dave18/EBAZ4205-Daughter-Board/Test_Code/EBAZ4205_Test5.cache/ip/2019.1.3/844bc8edf4976deb/System_processing_system7_0_0_sim_netlist.v

// Copyright 1986-2019 Xilinx, Inc. All Rights Reserved.
// --------------------------------------------------------------------------------
// Tool Version: Vivado v.2019.1.3 (win64) Build 2644227 Wed Sep  4 09:45:24 MDT 2019
// Date        : Sat Jan 30 14:02:05 2021
// Host        : DESKTOP-VR9QE9J running 64-bit major release  (build 9200)
// Command     : write_verilog -force -mode funcsim -rename_top decalper_eb_ot_sdeen_pot_pi_dehcac_xnilix -prefix
//               decalper_eb_ot_sdeen_pot_pi_dehcac_xnilix_ System_processing_system7_0_0_sim_netlist.v
// Design      : System_processing_system7_0_0
// Purpose     : This verilog netlist is a functional simulation representation of the design and should not be modified
//               or synthesized. This netlist cannot be used for SDF annotated simulation.
// Device      : xc7z010clg400-1
// --------------------------------------------------------------------------------
`timescale 1 ps / 1 ps

(* CHECK_LICENSE_TYPE = "System_processing_system7_0_0,processing_system7_v5_5_processing_system7,{}" *) (* DowngradeIPIdentifiedWarnings = "yes" *) (* X_CORE_INFO = "processing_system7_v5_5_processing_system7,Vivado 2019.1.3" *) 
(* NotValidForBitStream *)
module decalper_eb_ot_sdeen_pot_pi_dehcac_xnilix
   (FCLK_CLK0,
    FCLK_RESET0_N,
    MIO,
    DDR_CAS_n,
    DDR_CKE,
    DDR_Clk_n,
    DDR_Clk,
    DDR_CS_n,
    DDR_DRSTB,
    DDR_ODT,
    DDR_RAS_n,
    DDR_WEB,
    DDR_BankAddr,
    DDR_Addr,
    DDR_VRN,
    DDR_VRP,
    DDR_DM,
    DDR_DQ,
    DDR_DQS_n,
    DDR_DQS,
    PS_SRSTB,
    PS_CLK,
    PS_PORB);
  (* X_INTERFACE_INFO = "xilinx.com:signal:clock:1.0 FCLK_CLK0 CLK" *) (* X_INTERFACE_PARAMETER = "XIL_INTERFACENAME FCLK_CLK0, FREQ_HZ 50000000, PHASE 0.000, CLK_DOMAIN System_processing_system7_0_0_FCLK_CLK0, INSERT_VIP 0" *) output FCLK_CLK0;
  (* X_INTERFACE_INFO = "xilinx.com:signal:reset:1.0 FCLK_RESET0_N RST" *) (* X_INTERFACE_PARAMETER = "XIL_INTERFACENAME FCLK_RESET0_N, POLARITY ACTIVE_LOW, INSERT_VIP 0" *) output FCLK_RESET0_N;
  (* X_INTERFACE_INFO = "xilinx.com:display_processing_system7:fixedio:1.0 FIXED_IO MIO" *) inout [53:0]MIO;
  (* X_INTERFACE_INFO = "xilinx.com:interface:ddrx:1.0 DDR CAS_N" *) inout DDR_CAS_n;
  (* X_INTERFACE_INFO = "xilinx.com:interface:ddrx:1.0 DDR CKE" *) inout DDR_CKE;
  (* X_INTERFACE_INFO = "xilinx.com:interface:ddrx:1.0 DDR CK_N" *) inout DDR_Clk_n;
  (* X_INTERFACE_INFO = "xilinx.com:interface:ddrx:1.0 DDR CK_P" *) inout DDR_Clk;
  (* X_INTERFACE_INFO = "xilinx.com:interface:ddrx:1.0 DDR CS_N" *) inout DDR_CS_n;
  (* X_INTERFACE_INFO = "xilinx.com:interface:ddrx:1.0 DDR RESET_N" *) inout DDR_DRSTB;
  (* X_INTERFACE_INFO = "xilinx.com:interface:ddrx:1.0 DDR ODT" *) inout DDR_ODT;
  (* X_INTERFACE_INFO = "xilinx.com:interface:ddrx:1.0 DDR RAS_N" *) inout DDR_RAS_n;
  (* X_INTERFACE_INFO = "xilinx.com:interface:ddrx:1.0 DDR WE_N" *) inout DDR_WEB;
  (* X_INTERFACE_INFO = "xilinx.com:interface:ddrx:1.0 DDR BA" *) inout [2:0]DDR_BankAddr;
  (* X_INTERFACE_INFO = "xilinx.com:interface:ddrx:1.0 DDR ADDR" *) inout [14:0]DDR_Addr;
  (* X_INTERFACE_INFO = "xilinx.com:display_processing_system7:fixedio:1.0 FIXED_IO DDR_VRN" *) inout DDR_VRN;
  (* X_INTERFACE_INFO = "xilinx.com:display_processing_system7:fixedio:1.0 FIXED_IO DDR_VRP" *) inout DDR_VRP;
  (* X_INTERFACE_INFO = "xilinx.com:interface:ddrx:1.0 DDR DM" *) inout [3:0]DDR_DM;
  (* X_INTERFACE_INFO = "xilinx.com:interface:ddrx:1.0 DDR DQ" *) inout [31:0]DDR_DQ;
  (* X_INTERFACE_INFO = "xilinx.com:interface:ddrx:1.0 DDR DQS_N" *) inout [3:0]DDR_DQS_n;
  (* X_INTERFACE_INFO = "xilinx.com:interface:ddrx:1.0 DDR DQS_P" *) (* X_INTERFACE_PARAMETER = "XIL_INTERFACENAME DDR, CAN_DEBUG false, TIMEPERIOD_PS 1250, MEMORY_TYPE COMPONENTS, DATA_WIDTH 8, CS_ENABLED true, DATA_MASK_ENABLED true, SLOT Single, MEM_ADDR_MAP ROW_COLUMN_BANK, BURST_LENGTH 8, AXI_ARBITRATION_SCHEME TDM, CAS_LATENCY 11, CAS_WRITE_LATENCY 11" *) inout [3:0]DDR_DQS;
  (* X_INTERFACE_INFO = "xilinx.com:display_processing_system7:fixedio:1.0 FIXED_IO PS_SRSTB" *) inout PS_SRSTB;
  (* X_INTERFACE_INFO = "xilinx.com:display_processing_system7:fixedio:1.0 FIXED_IO PS_CLK" *) inout PS_CLK;
  (* X_INTERFACE_INFO = "xilinx.com:display_processing_system7:fixedio:1.0 FIXED_IO PS_PORB" *) (* X_INTERFACE_PARAMETER = "XIL_INTERFACENAME FIXED_IO, CAN_DEBUG false" *) inout PS_PORB;

  wire [14:0]DDR_Addr;
  wire [2:0]DDR_BankAddr;
  wire DDR_CAS_n;
  wire DDR_CKE;
  wire DDR_CS_n;
  wire DDR_Clk;
  wire DDR_Clk_n;
  wire [3:0]DDR_DM;
  wire [31:0]DDR_DQ;
  wire [3:0]DDR_DQS;
  wire [3:0]DDR_DQS_n;
  wire DDR_DRSTB;
  wire DDR_ODT;
  wire DDR_RAS_n;
  wire DDR_VRN;
  wire DDR_VRP;
  wire DDR_WEB;
  wire FCLK_CLK0;
  wire FCLK_RESET0_N;
  wire [53:0]MIO;
  wire PS_CLK;
  wire PS_PORB;
  wire PS_SRSTB;
  wire NLW_inst_CAN0_PHY_TX_UNCONNECTED;
  wire NLW_inst_CAN1_PHY_TX_UNCONNECTED;
  wire NLW_inst_DMA0_DAVALID_UNCONNECTED;
  wire NLW_inst_DMA0_DRREADY_UNCONNECTED;
  wire NLW_inst_DMA0_RSTN_UNCONNECTED;
  wire NLW_inst_DMA1_DAVALID_UNCONNECTED;
  wire NLW_inst_DMA1_DRREADY_UNCONNECTED;
  wire NLW_inst_DMA1_RSTN_UNCONNECTED;
  wire NLW_inst_DMA2_DAVALID_UNCONNECTED;
  wire NLW_inst_DMA2_DRREADY_UNCONNECTED;
  wire NLW_inst_DMA2_RSTN_UNCONNECTED;
  wire NLW_inst_DMA3_DAVALID_UNCONNECTED;
  wire NLW_inst_DMA3_DRREADY_UNCONNECTED;
  wire NLW_inst_DMA3_RSTN_UNCONNECTED;
  wire NLW_inst_ENET0_GMII_TX_EN_UNCONNECTED;
  wire NLW_inst_ENET0_GMII_TX_ER_UNCONNECTED;
  wire NLW_inst_ENET0_MDIO_MDC_UNCONNECTED;
  wire NLW_inst_ENET0_MDIO_O_UNCONNECTED;
  wire NLW_inst_ENET0_MDIO_T_UNCONNECTED;
  wire NLW_inst_ENET0_PTP_DELAY_REQ_RX_UNCONNECTED;
  wire NLW_inst_ENET0_PTP_DELAY_REQ_TX_UNCONNECTED;
  wire NLW_inst_ENET0_PTP_PDELAY_REQ_RX_UNCONNECTED;
  wire NLW_inst_ENET0_PTP_PDELAY_REQ_TX_UNCONNECTED;
  wire NLW_inst_ENET0_PTP_PDELAY_RESP_RX_UNCONNECTED;
  wire NLW_inst_ENET0_PTP_PDELAY_RESP_TX_UNCONNECTED;
  wire NLW_inst_ENET0_PTP_SYNC_FRAME_RX_UNCONNECTED;
  wire NLW_inst_ENET0_PTP_SYNC_FRAME_TX_UNCONNECTED;
  wire NLW_inst_ENET0_SOF_RX_UNCONNECTED;
  wire NLW_inst_ENET0_SOF_TX_UNCONNECTED;
  wire NLW_inst_ENET1_GMII_TX_EN_UNCONNECTED;
  wire NLW_inst_ENET1_GMII_TX_ER_UNCONNECTED;
  wire NLW_inst_ENET1_MDIO_MDC_UNCONNECTED;
  wire NLW_inst_ENET1_MDIO_O_UNCONNECTED;
  wire NLW_inst_ENET1_MDIO_T_UNCONNECTED;
  wire NLW_inst_ENET1_PTP_DELAY_REQ_RX_UNCONNECTED;
  wire NLW_inst_ENET1_PTP_DELAY_REQ_TX_UNCONNECTED;
  wire NLW_inst_ENET1_PTP_PDELAY_REQ_RX_UNCONNECTED;
  wire NLW_inst_ENET1_PTP_PDELAY_REQ_TX_UNCONNECTED;
  wire NLW_inst_ENET1_PTP_PDELAY_RESP_RX_UNCONNECTED;
  wire NLW_inst_ENET1_PTP_PDELAY_RESP_TX_UNCONNECTED;
  wire NLW_inst_ENET1_PTP_SYNC_FRAME_RX_UNCONNECTED;
  wire NLW_inst_ENET1_PTP_SYNC_FRAME_TX_UNCONNECTED;
  wire NLW_inst_ENET1_SOF_RX_UNCONNECTED;
  wire NLW_inst_ENET1_SOF_TX_UNCONNECTED;
  wire NLW_inst_EVENT_EVENTO_UNCONNECTED;
  wire NLW_inst_FCLK_CLK1_UNCONNECTED;
  wire NLW_inst_FCLK_CLK2_UNCONNECTED;
  wire NLW_inst_FCLK_CLK3_UNCONNECTED;
  wire NLW_inst_FCLK_RESET1_N_UNCONNECTED;
  wire NLW_inst_FCLK_RESET2_N_UNCONNECTED;
  wire NLW_inst_FCLK_RESET3_N_UNCONNECTED;
  wire NLW_inst_FTMT_F2P_TRIGACK_0_UNCONNECTED;
  wire NLW_inst_FTMT_F2P_TRIGACK_1_UNCONNECTED;
  wire NLW_inst_FTMT_F2P_TRIGACK_2_UNCONNECTED;
  wire NLW_inst_FTMT_F2P_TRIGACK_3_UNCONNECTED;
  wire NLW_inst_FTMT_P2F_TRIG_0_UNCONNECTED;
  wire NLW_inst_FTMT_P2F_TRIG_1_UNCONNECTED;
  wire NLW_inst_FTMT_P2F_TRIG_2_UNCONNECTED;
  wire NLW_inst_FTMT_P2F_TRIG_3_UNCONNECTED;
  wire NLW_inst_I2C0_SCL_O_UNCONNECTED;
  wire NLW_inst_I2C0_SCL_T_UNCONNECTED;
  wire NLW_inst_I2C0_SDA_O_UNCONNECTED;
  wire NLW_inst_I2C0_SDA_T_UNCONNECTED;
  wire NLW_inst_I2C1_SCL_O_UNCONNECTED;
  wire NLW_inst_I2C1_SCL_T_UNCONNECTED;
  wire NLW_inst_I2C1_SDA_O_UNCONNECTED;
  wire NLW_inst_I2C1_SDA_T_UNCONNECTED;
  wire NLW_inst_IRQ_P2F_CAN0_UNCONNECTED;
  wire NLW_inst_IRQ_P2F_CAN1_UNCONNECTED;
  wire NLW_inst_IRQ_P2F_CTI_UNCONNECTED;
  wire NLW_inst_IRQ_P2F_DMAC0_UNCONNECTED;
  wire NLW_inst_IRQ_P2F_DMAC1_UNCONNECTED;
  wire NLW_inst_IRQ_P2F_DMAC2_UNCONNECTED;
  wire NLW_inst_IRQ_P2F_DMAC3_UNCONNECTED;
  wire NLW_inst_IRQ_P2F_DMAC4_UNCONNECTED;
  wire NLW_inst_IRQ_P2F_DMAC5_UNCONNECTED;
  wire NLW_inst_IRQ_P2F_DMAC6_UNCONNECTED;
  wire NLW_inst_IRQ_P2F_DMAC7_UNCONNECTED;
  wire NLW_inst_IRQ_P2F_DMAC_ABORT_UNCONNECTED;
  wire NLW_inst_IRQ_P2F_ENET0_UNCONNECTED;
  wire NLW_inst_IRQ_P2F_ENET1_UNCONNECTED;
  wire NLW_inst_IRQ_P2F_ENET_WAKE0_UNCONNECTED;
  wire NLW_inst_IRQ_P2F_ENET_WAKE1_UNCONNECTED;
  wire NLW_inst_IRQ_P2F_GPIO_UNCONNECTED;
  wire NLW_inst_IRQ_P2F_I2C0_UNCONNECTED;
  wire NLW_inst_IRQ_P2F_I2C1_UNCONNECTED;
  wire NLW_inst_IRQ_P2F_QSPI_UNCONNECTED;
  wire NLW_inst_IRQ_P2F_SDIO0_UNCONNECTED;
  wire NLW_inst_IRQ_P2F_SDIO1_UNCONNECTED;
  wire NLW_inst_IRQ_P2F_SMC_UNCONNECTED;
  wire NLW_inst_IRQ_P2F_SPI0_UNCONNECTED;
  wire NLW_inst_IRQ_P2F_SPI1_UNCONNECTED;
  wire NLW_inst_IRQ_P2F_UART0_UNCONNECTED;
  wire NLW_inst_IRQ_P2F_UART1_UNCONNECTED;
  wire NLW_inst_IRQ_P2F_USB0_UNCONNECTED;
  wire NLW_inst_IRQ_P2F_USB1_UNCONNECTED;
  wire NLW_inst_M_AXI_GP0_ARESETN_UNCONNECTED;
  wire NLW_inst_M_AXI_GP0_ARVALID_UNCONNECTED;
  wire NLW_inst_M_AXI_GP0_AWVALID_UNCONNECTED;
  wire NLW_inst_M_AXI_GP0_BREADY_UNCONNECTED;
  wire NLW_inst_M_AXI_GP0_RREADY_UNCONNECTED;
  wire NLW_inst_M_AXI_GP0_WLAST_UNCONNECTED;
  wire NLW_inst_M_AXI_GP0_WVALID_UNCONNECTED;
  wire NLW_inst_M_AXI_GP1_ARESETN_UNCONNECTED;
  wire NLW_inst_M_AXI_GP1_ARVALID_UNCONNECTED;
  wire NLW_inst_M_AXI_GP1_AWVALID_UNCONNECTED;
  wire NLW_inst_M_AXI_GP1_BREADY_UNCONNECTED;
  wire NLW_inst_M_AXI_GP1_RREADY_UNCONNECTED;
  wire NLW_inst_M_AXI_GP1_WLAST_UNCONNECTED;
  wire NLW_inst_M_AXI_GP1_WVALID_UNCONNECTED;
  wire NLW_inst_PJTAG_TDO_UNCONNECTED;
  wire NLW_inst_SDIO0_BUSPOW_UNCONNECTED;
  wire NLW_inst_SDIO0_CLK_UNCONNECTED;
  wire NLW_inst_SDIO0_CMD_O_UNCONNECTED;
  wire NLW_inst_SDIO0_CMD_T_UNCONNECTED;
  wire NLW_inst_SDIO0_LED_UNCONNECTED;
  wire NLW_inst_SDIO1_BUSPOW_UNCONNECTED;
  wire NLW_inst_SDIO1_CLK_UNCONNECTED;
  wire NLW_inst_SDIO1_CMD_O_UNCONNECTED;
  wire NLW_inst_SDIO1_CMD_T_UNCONNECTED;
  wire NLW_inst_SDIO1_LED_UNCONNECTED;
  wire NLW_inst_SPI0_MISO_O_UNCONNECTED;
  wire NLW_inst_SPI0_MISO_T_UNCONNECTED;
  wire NLW_inst_SPI0_MOSI_O_UNCONNECTED;
  wire NLW_inst_SPI0_MOSI_T_UNCONNECTED;
  wire NLW_inst_SPI0_SCLK_O_UNCONNECTED;
  wire NLW_inst_SPI0_SCLK_T_UNCONNECTED;
  wire NLW_inst_SPI0_SS1_O_UNCONNECTED;
  wire NLW_inst_SPI0_SS2_O_UNCONNECTED;
  wire NLW_inst_SPI0_SS_O_UNCONNECTED;
  wire NLW_inst_SPI0_SS_T_UNCONNECTED;
  wire NLW_inst_SPI1_MISO_O_UNCONNECTED;
  wire NLW_inst_SPI1_MISO_T_UNCONNECTED;
  wire NLW_inst_SPI1_MOSI_O_UNCONNECTED;
  wire NLW_inst_SPI1_MOSI_T_UNCONNECTED;
  wire NLW_inst_SPI1_SCLK_O_UNCONNECTED;
  wire NLW_inst_SPI1_SCLK_T_UNCONNECTED;
  wire NLW_inst_SPI1_SS1_O_UNCONNECTED;
  wire NLW_inst_SPI1_SS2_O_UNCONNECTED;
  wire NLW_inst_SPI1_SS_O_UNCONNECTED;
  wire NLW_inst_SPI1_SS_T_UNCONNECTED;
  wire NLW_inst_S_AXI_ACP_ARESETN_UNCONNECTED;
  wire NLW_inst_S_AXI_ACP_ARREADY_UNCONNECTED;
  wire NLW_inst_S_AXI_ACP_AWREADY_UNCONNECTED;
  wire NLW_inst_S_AXI_ACP_BVALID_UNCONNECTED;
  wire NLW_inst_S_AXI_ACP_RLAST_UNCONNECTED;
  wire NLW_inst_S_AXI_ACP_RVALID_UNCONNECTED;
  wire NLW_inst_S_AXI_ACP_WREADY_UNCONNECTED;
  wire NLW_inst_S_AXI_GP0_ARESETN_UNCONNECTED;
  wire NLW_inst_S_AXI_GP0_ARREADY_UNCONNECTED;
  wire NLW_inst_S_AXI_GP0_AWREADY_UNCONNECTED;
  wire NLW_inst_S_AXI_GP0_BVALID_UNCONNECTED;
  wire NLW_inst_S_AXI_GP0_RLAST_UNCONNECTED;
  wire NLW_inst_S_AXI_GP0_RVALID_UNCONNECTED;
  wire NLW_inst_S_AXI_GP0_WREADY_UNCONNECTED;
  wire NLW_inst_S_AXI_GP1_ARESETN_UNCONNECTED;
  wire NLW_inst_S_AXI_GP1_ARREADY_UNCONNECTED;
  wire NLW_inst_S_AXI_GP1_AWREADY_UNCONNECTED;
  wire NLW_inst_S_AXI_GP1_BVALID_UNCONNECTED;
  wire NLW_inst_S_AXI_GP1_RLAST_UNCONNECTED;
  wire NLW_inst_S_AXI_GP1_RVALID_UNCONNECTED;
  wire NLW_inst_S_AXI_GP1_WREADY_UNCONNECTED;
  wire NLW_inst_S_AXI_HP0_ARESETN_UNCONNECTED;
  wire NLW_inst_S_AXI_HP0_ARREADY_UNCONNECTED;
  wire NLW_inst_S_AXI_HP0_AWREADY_UNCONNECTED;
  wire NLW_inst_S_AXI_HP0_BVALID_UNCONNECTED;
  wire NLW_inst_S_AXI_HP0_RLAST_UNCONNECTED;
  wire NLW_inst_S_AXI_HP0_RVALID_UNCONNECTED;
  wire NLW_inst_S_AXI_HP0_WREADY_UNCONNECTED;
  wire NLW_inst_S_AXI_HP1_ARESETN_UNCONNECTED;
  wire NLW_inst_S_AXI_HP1_ARREADY_UNCONNECTED;
  wire NLW_inst_S_AXI_HP1_AWREADY_UNCONNECTED;
  wire NLW_inst_S_AXI_HP1_BVALID_UNCONNECTED;
  wire NLW_inst_S_AXI_HP1_RLAST_UNCONNECTED;
  wire NLW_inst_S_AXI_HP1_RVALID_UNCONNECTED;
  wire NLW_inst_S_AXI_HP1_WREADY_UNCONNECTED;
  wire NLW_inst_S_AXI_HP2_ARESETN_UNCONNECTED;
  wire NLW_inst_S_AXI_HP2_ARREADY_UNCONNECTED;
  wire NLW_inst_S_AXI_HP2_AWREADY_UNCONNECTED;
  wire NLW_inst_S_AXI_HP2_BVALID_UNCONNECTED;
  wire NLW_inst_S_AXI_HP2_RLAST_UNCONNECTED;
  wire NLW_inst_S_AXI_HP2_RVALID_UNCONNECTED;
  wire NLW_inst_S_AXI_HP2_WREADY_UNCONNECTED;
  wire NLW_inst_S_AXI_HP3_ARESETN_UNCONNECTED;
  wire NLW_inst_S_AXI_HP3_ARREADY_UNCONNECTED;
  wire NLW_inst_S_AXI_HP3_AWREADY_UNCONNECTED;
  wire NLW_inst_S_AXI_HP3_BVALID_UNCONNECTED;
  wire NLW_inst_S_AXI_HP3_RLAST_UNCONNECTED;
  wire NLW_inst_S_AXI_HP3_RVALID_UNCONNECTED;
  wire NLW_inst_S_AXI_HP3_WREADY_UNCONNECTED;
  wire NLW_inst_TRACE_CLK_OUT_UNCONNECTED;
  wire NLW_inst_TRACE_CTL_UNCONNECTED;
  wire NLW_inst_TTC0_WAVE0_OUT_UNCONNECTED;
  wire NLW_inst_TTC0_WAVE1_OUT_UNCONNECTED;
  wire NLW_inst_TTC0_WAVE2_OUT_UNCONNECTED;
  wire NLW_inst_TTC1_WAVE0_OUT_UNCONNECTED;
  wire NLW_inst_TTC1_WAVE1_OUT_UNCONNECTED;
  wire NLW_inst_TTC1_WAVE2_OUT_UNCONNECTED;
  wire NLW_inst_UART0_DTRN_UNCONNECTED;
  wire NLW_inst_UART0_RTSN_UNCONNECTED;
  wire NLW_inst_UART0_TX_UNCONNECTED;
  wire NLW_inst_UART1_DTRN_UNCONNECTED;
  wire NLW_inst_UART1_RTSN_UNCONNECTED;
  wire NLW_inst_UART1_TX_UNCONNECTED;
  wire NLW_inst_USB0_VBUS_PWRSELECT_UNCONNECTED;
  wire NLW_inst_USB1_VBUS_PWRSELECT_UNCONNECTED;
  wire NLW_inst_WDT_RST_OUT_UNCONNECTED;
  wire [1:0]NLW_inst_DMA0_DATYPE_UNCONNECTED;
  wire [1:0]NLW_inst_DMA1_DATYPE_UNCONNECTED;
  wire [1:0]NLW_inst_DMA2_DATYPE_UNCONNECTED;
  wire [1:0]NLW_inst_DMA3_DATYPE_UNCONNECTED;
  wire [7:0]NLW_inst_ENET0_GMII_TXD_UNCONNECTED;
  wire [7:0]NLW_inst_ENET1_GMII_TXD_UNCONNECTED;
  wire [1:0]NLW_inst_EVENT_STANDBYWFE_UNCONNECTED;
  wire [1:0]NLW_inst_EVENT_STANDBYWFI_UNCONNECTED;
  wire [31:0]NLW_inst_FTMT_P2F_DEBUG_UNCONNECTED;
  wire [63:0]NLW_inst_GPIO_O_UNCONNECTED;
  wire [63:0]NLW_inst_GPIO_T_UNCONNECTED;
  wire [31:0]NLW_inst_M_AXI_GP0_ARADDR_UNCONNECTED;
  wire [1:0]NLW_inst_M_AXI_GP0_ARBURST_UNCONNECTED;
  wire [3:0]NLW_inst_M_AXI_GP0_ARCACHE_UNCONNECTED;
  wire [11:0]NLW_inst_M_AXI_GP0_ARID_UNCONNECTED;
  wire [3:0]NLW_inst_M_AXI_GP0_ARLEN_UNCONNECTED;
  wire [1:0]NLW_inst_M_AXI_GP0_ARLOCK_UNCONNECTED;
  wire [2:0]NLW_inst_M_AXI_GP0_ARPROT_UNCONNECTED;
  wire [3:0]NLW_inst_M_AXI_GP0_ARQOS_UNCONNECTED;
  wire [2:0]NLW_inst_M_AXI_GP0_ARSIZE_UNCONNECTED;
  wire [31:0]NLW_inst_M_AXI_GP0_AWADDR_UNCONNECTED;
  wire [1:0]NLW_inst_M_AXI_GP0_AWBURST_UNCONNECTED;
  wire [3:0]NLW_inst_M_AXI_GP0_AWCACHE_UNCONNECTED;
  wire [11:0]NLW_inst_M_AXI_GP0_AWID_UNCONNECTED;
  wire [3:0]NLW_inst_M_AXI_GP0_AWLEN_UNCONNECTED;
  wire [1:0]NLW_inst_M_AXI_GP0_AWLOCK_UNCONNECTED;
  wire [2:0]NLW_inst_M_AXI_GP0_AWPROT_UNCONNECTED;
  wire [3:0]NLW_inst_M_AXI_GP0_AWQOS_UNCONNECTED;
  wire [2:0]NLW_inst_M_AXI_GP0_AWSIZE_UNCONNECTED;
  wire [31:0]NLW_inst_M_AXI_GP0_WDATA_UNCONNECTED;
  wire [11:0]NLW_inst_M_AXI_GP0_WID_UNCONNECTED;
  wire [3:0]NLW_inst_M_AXI_GP0_WSTRB_UNCONNECTED;
  wire [31:0]NLW_inst_M_AXI_GP1_ARADDR_UNCONNECTED;
  wire [1:0]NLW_inst_M_AXI_GP1_ARBURST_UNCONNECTED;
  wire [3:0]NLW_inst_M_AXI_GP1_ARCACHE_UNCONNECTED;
  wire [11:0]NLW_inst_M_AXI_GP1_ARID_UNCONNECTED;
  wire [3:0]NLW_inst_M_AXI_GP1_ARLEN_UNCONNECTED;
  wire [1:0]NLW_inst_M_AXI_GP1_ARLOCK_UNCONNECTED;
  wire [2:0]NLW_inst_M_AXI_GP1_ARPROT_UNCONNECTED;
  wire [3:0]NLW_inst_M_AXI_GP1_ARQOS_UNCONNECTED;
  wire [2:0]NLW_inst_M_AXI_GP1_ARSIZE_UNCONNECTED;
  wire [31:0]NLW_inst_M_AXI_GP1_AWADDR_UNCONNECTED;
  wire [1:0]NLW_inst_M_AXI_GP1_AWBURST_UNCONNECTED;
  wire [3:0]NLW_inst_M_AXI_GP1_AWCACHE_UNCONNECTED;
  wire [11:0]NLW_inst_M_AXI_GP1_AWID_UNCONNECTED;
  wire [3:0]NLW_inst_M_AXI_GP1_AWLEN_UNCONNECTED;
  wire [1:0]NLW_inst_M_AXI_GP1_AWLOCK_UNCONNECTED;
  wire [2:0]NLW_inst_M_AXI_GP1_AWPROT_UNCONNECTED;
  wire [3:0]NLW_inst_M_AXI_GP1_AWQOS_UNCONNECTED;
  wire [2:0]NLW_inst_M_AXI_GP1_AWSIZE_UNCONNECTED;
  wire [31:0]NLW_inst_M_AXI_GP1_WDATA_UNCONNECTED;
  wire [11:0]NLW_inst_M_AXI_GP1_WID_UNCONNECTED;
  wire [3:0]NLW_inst_M_AXI_GP1_WSTRB_UNCONNECTED;
  wire [2:0]NLW_inst_SDIO0_BUSVOLT_UNCONNECTED;
  wire [3:0]NLW_inst_SDIO0_DATA_O_UNCONNECTED;
  wire [3:0]NLW_inst_SDIO0_DATA_T_UNCONNECTED;
  wire [2:0]NLW_inst_SDIO1_BUSVOLT_UNCONNECTED;
  wire [3:0]NLW_inst_SDIO1_DATA_O_UNCONNECTED;
  wire [3:0]NLW_inst_SDIO1_DATA_T_UNCONNECTED;
  wire [2:0]NLW_inst_S_AXI_ACP_BID_UNCONNECTED;
  wire [1:0]NLW_inst_S_AXI_ACP_BRESP_UNCONNECTED;
  wire [63:0]NLW_inst_S_AXI_ACP_RDATA_UNCONNECTED;
  wire [2:0]NLW_inst_S_AXI_ACP_RID_UNCONNECTED;
  wire [1:0]NLW_inst_S_AXI_ACP_RRESP_UNCONNECTED;
  wire [5:0]NLW_inst_S_AXI_GP0_BID_UNCONNECTED;
  wire [1:0]NLW_inst_S_AXI_GP0_BRESP_UNCONNECTED;
  wire [31:0]NLW_inst_S_AXI_GP0_RDATA_UNCONNECTED;
  wire [5:0]NLW_inst_S_AXI_GP0_RID_UNCONNECTED;
  wire [1:0]NLW_inst_S_AXI_GP0_RRESP_UNCONNECTED;
  wire [5:0]NLW_inst_S_AXI_GP1_BID_UNCONNECTED;
  wire [1:0]NLW_inst_S_AXI_GP1_BRESP_UNCONNECTED;
  wire [31:0]NLW_inst_S_AXI_GP1_RDATA_UNCONNECTED;
  wire [5:0]NLW_inst_S_AXI_GP1_RID_UNCONNECTED;
  wire [1:0]NLW_inst_S_AXI_GP1_RRESP_UNCONNECTED;
  wire [5:0]NLW_inst_S_AXI_HP0_BID_UNCONNECTED;
  wire [1:0]NLW_inst_S_AXI_HP0_BRESP_UNCONNECTED;
  wire [2:0]NLW_inst_S_AXI_HP0_RACOUNT_UNCONNECTED;
  wire [7:0]NLW_inst_S_AXI_HP0_RCOUNT_UNCONNECTED;
  wire [63:0]NLW_inst_S_AXI_HP0_RDATA_UNCONNECTED;
  wire [5:0]NLW_inst_S_AXI_HP0_RID_UNCONNECTED;
  wire [1:0]NLW_inst_S_AXI_HP0_RRESP_UNCONNECTED;
  wire [5:0]NLW_inst_S_AXI_HP0_WACOUNT_UNCONNECTED;
  wire [7:0]NLW_inst_S_AXI_HP0_WCOUNT_UNCONNECTED;
  wire [5:0]NLW_inst_S_AXI_HP1_BID_UNCONNECTED;
  wire [1:0]NLW_inst_S_AXI_HP1_BRESP_UNCONNECTED;
  wire [2:0]NLW_inst_S_AXI_HP1_RACOUNT_UNCONNECTED;
  wire [7:0]NLW_inst_S_AXI_HP1_RCOUNT_UNCONNECTED;
  wire [63:0]NLW_inst_S_AXI_HP1_RDATA_UNCONNECTED;
  wire [5:0]NLW_inst_S_AXI_HP1_RID_UNCONNECTED;
  wire [1:0]NLW_inst_S_AXI_HP1_RRESP_UNCONNECTED;
  wire [5:0]NLW_inst_S_AXI_HP1_WACOUNT_UNCONNECTED;
  wire [7:0]NLW_inst_S_AXI_HP1_WCOUNT_UNCONNECTED;
  wire [5:0]NLW_inst_S_AXI_HP2_BID_UNCONNECTED;
  wire [1:0]NLW_inst_S_AXI_HP2_BRESP_UNCONNECTED;
  wire [2:0]NLW_inst_S_AXI_HP2_RACOUNT_UNCONNECTED;
  wire [7:0]NLW_inst_S_AXI_HP2_RCOUNT_UNCONNECTED;
  wire [63:0]NLW_inst_S_AXI_HP2_RDATA_UNCONNECTED;
  wire [5:0]NLW_inst_S_AXI_HP2_RID_UNCONNECTED;
  wire [1:0]NLW_inst_S_AXI_HP2_RRESP_UNCONNECTED;
  wire [5:0]NLW_inst_S_AXI_HP2_WACOUNT_UNCONNECTED;
  wire [7:0]NLW_inst_S_AXI_HP2_WCOUNT_UNCONNECTED;
  wire [5:0]NLW_inst_S_AXI_HP3_BID_UNCONNECTED;
  wire [1:0]NLW_inst_S_AXI_HP3_BRESP_UNCONNECTED;
  wire [2:0]NLW_inst_S_AXI_HP3_RACOUNT_UNCONNECTED;
  wire [7:0]NLW_inst_S_AXI_HP3_RCOUNT_UNCONNECTED;
  wire [63:0]NLW_inst_S_AXI_HP3_RDATA_UNCONNECTED;
  wire [5:0]NLW_inst_S_AXI_HP3_RID_UNCONNECTED;
  wire [1:0]NLW_inst_S_AXI_HP3_RRESP_UNCONNECTED;
  wire [5:0]NLW_inst_S_AXI_HP3_WACOUNT_UNCONNECTED;
  wire [7:0]NLW_inst_S_AXI_HP3_WCOUNT_UNCONNECTED;
  wire [1:0]NLW_inst_TRACE_DATA_UNCONNECTED;
  wire [1:0]NLW_inst_USB0_PORT_INDCTL_UNCONNECTED;
  wire [1:0]NLW_inst_USB1_PORT_INDCTL_UNCONNECTED;

  (* C_DM_WIDTH = "4" *) 
  (* C_DQS_WIDTH = "4" *) 
  (* C_DQ_WIDTH = "32" *) 
  (* C_EMIO_GPIO_WIDTH = "64" *) 
  (* C_EN_EMIO_ENET0 = "0" *) 
  (* C_EN_EMIO_ENET1 = "0" *) 
  (* C_EN_EMIO_PJTAG = "0" *) 
  (* C_EN_EMIO_TRACE = "0" *) 
  (* C_FCLK_CLK0_BUF = "TRUE" *) 
  (* C_FCLK_CLK1_BUF = "FALSE" *) 
  (* C_FCLK_CLK2_BUF = "FALSE" *) 
  (* C_FCLK_CLK3_BUF = "FALSE" *) 
  (* C_GP0_EN_MODIFIABLE_TXN = "1" *) 
  (* C_GP1_EN_MODIFIABLE_TXN = "1" *) 
  (* C_INCLUDE_ACP_TRANS_CHECK = "0" *) 
  (* C_INCLUDE_TRACE_BUFFER = "0" *) 
  (* C_IRQ_F2P_MODE = "DIRECT" *) 
  (* C_MIO_PRIMITIVE = "54" *) 
  (* C_M_AXI_GP0_ENABLE_STATIC_REMAP = "0" *) 
  (* C_M_AXI_GP0_ID_WIDTH = "12" *) 
  (* C_M_AXI_GP0_THREAD_ID_WIDTH = "12" *) 
  (* C_M_AXI_GP1_ENABLE_STATIC_REMAP = "0" *) 
  (* C_M_AXI_GP1_ID_WIDTH = "12" *) 
  (* C_M_AXI_GP1_THREAD_ID_WIDTH = "12" *) 
  (* C_NUM_F2P_INTR_INPUTS = "1" *) 
  (* C_PACKAGE_NAME = "clg400" *) 
  (* C_PS7_SI_REV = "PRODUCTION" *) 
  (* C_S_AXI_ACP_ARUSER_VAL = "31" *) 
  (* C_S_AXI_ACP_AWUSER_VAL = "31" *) 
  (* C_S_AXI_ACP_ID_WIDTH = "3" *) 
  (* C_S_AXI_GP0_ID_WIDTH = "6" *) 
  (* C_S_AXI_GP1_ID_WIDTH = "6" *) 
  (* C_S_AXI_HP0_DATA_WIDTH = "64" *) 
  (* C_S_AXI_HP0_ID_WIDTH = "6" *) 
  (* C_S_AXI_HP1_DATA_WIDTH = "64" *) 
  (* C_S_AXI_HP1_ID_WIDTH = "6" *) 
  (* C_S_AXI_HP2_DATA_WIDTH = "64" *) 
  (* C_S_AXI_HP2_ID_WIDTH = "6" *) 
  (* C_S_AXI_HP3_DATA_WIDTH = "64" *) 
  (* C_S_AXI_HP3_ID_WIDTH = "6" *) 
  (* C_TRACE_BUFFER_CLOCK_DELAY = "12" *) 
  (* C_TRACE_BUFFER_FIFO_SIZE = "128" *) 
  (* C_TRACE_INTERNAL_WIDTH = "2" *) 
  (* C_TRACE_PIPELINE_WIDTH = "8" *) 
  (* C_USE_AXI_NONSECURE = "0" *) 
  (* C_USE_DEFAULT_ACP_USER_VAL = "0" *) 
  (* C_USE_M_AXI_GP0 = "0" *) 
  (* C_USE_M_AXI_GP1 = "0" *) 
  (* C_USE_S_AXI_ACP = "0" *) 
  (* C_USE_S_AXI_GP0 = "0" *) 
  (* C_USE_S_AXI_GP1 = "0" *) 
  (* C_USE_S_AXI_HP0 = "0" *) 
  (* C_USE_S_AXI_HP1 = "0" *) 
  (* C_USE_S_AXI_HP2 = "0" *) 
  (* C_USE_S_AXI_HP3 = "0" *) 
  (* HW_HANDOFF = "System_processing_system7_0_0.hwdef" *) 
  (* POWER = "<PROCESSOR name={system} numA9Cores={2} clockFreq={666.666666} load={0.5} /><MEMORY name={code} memType={DDR3} dataWidth={16} clockFreq={533.333333} readRate={0.5} writeRate={0.5} /><IO interface={UART} ioStandard={LVCMOS33} bidis={2} ioBank={Vcco_p1} clockFreq={100.000000} usageRate={0.5} /><IO interface={NAND} ioStandard={} bidis={14} ioBank={} clockFreq={100.000000} usageRate={0.5} /><PLL domain={Processor} vco={1333.333} /><PLL domain={Memory} vco={1066.667} /><PLL domain={IO} vco={1600.000} />/>" *) 
  (* USE_TRACE_DATA_EDGE_DETECTOR = "0" *) 
  decalper_eb_ot_sdeen_pot_pi_dehcac_xnilix_processing_system7_v5_5_processing_system7 inst
       (.CAN0_PHY_RX(1'b0),
        .CAN0_PHY_TX(NLW_inst_CAN0_PHY_TX_UNCONNECTED),
        .CAN1_PHY_RX(1'b0),
        .CAN1_PHY_TX(NLW_inst_CAN1_PHY_TX_UNCONNECTED),
        .Core0_nFIQ(1'b0),
        .Core0_nIRQ(1'b0),
        .Core1_nFIQ(1'b0),
        .Core1_nIRQ(1'b0),
        .DDR_ARB({1'b0,1'b0,1'b0,1'b0}),
        .DDR_Addr(DDR_Addr),
        .DDR_BankAddr(DDR_BankAddr),
        .DDR_CAS_n(DDR_CAS_n),
        .DDR_CKE(DDR_CKE),
        .DDR_CS_n(DDR_CS_n),
        .DDR_Clk(DDR_Clk),
        .DDR_Clk_n(DDR_Clk_n),
        .DDR_DM(DDR_DM),
        .DDR_DQ(DDR_DQ),
        .DDR_DQS(DDR_DQS),
        .DDR_DQS_n(DDR_DQS_n),
        .DDR_DRSTB(DDR_DRSTB),
        .DDR_ODT(DDR_ODT),
        .DDR_RAS_n(DDR_RAS_n),
        .DDR_VRN(DDR_VRN),
        .DDR_VRP(DDR_VRP),
        .DDR_WEB(DDR_WEB),
        .DMA0_ACLK(1'b0),
        .DMA0_DAREADY(1'b0),
        .DMA0_DATYPE(NLW_inst_DMA0_DATYPE_UNCONNECTED[1:0]),
        .DMA0_DAVALID(NLW_inst_DMA0_DAVALID_UNCONNECTED),
        .DMA0_DRLAST(1'b0),
        .DMA0_DRREADY(NLW_inst_DMA0_DRREADY_UNCONNECTED),
        .DMA0_DRTYPE({1'b0,1'b0}),
        .DMA0_DRVALID(1'b0),
        .DMA0_RSTN(NLW_inst_DMA0_RSTN_UNCONNECTED),
        .DMA1_ACLK(1'b0),
        .DMA1_DAREADY(1'b0),
        .DMA1_DATYPE(NLW_inst_DMA1_DATYPE_UNCONNECTED[1:0]),
        .DMA1_DAVALID(NLW_inst_DMA1_DAVALID_UNCONNECTED),
        .DMA1_DRLAST(1'b0),
        .DMA1_DRREADY(NLW_inst_DMA1_DRREADY_UNCONNECTED),
        .DMA1_DRTYPE({1'b0,1'b0}),
        .DMA1_DRVALID(1'b0),
        .DMA1_RSTN(NLW_inst_DMA1_RSTN_UNCONNECTED),
        .DMA2_ACLK(1'b0),
        .DMA2_DAREADY(1'b0),
        .DMA2_DATYPE(NLW_inst_DMA2_DATYPE_UNCONNECTED[1:0]),
        .DMA2_DAVALID(NLW_inst_DMA2_DAVALID_UNCONNECTED),
        .DMA2_DRLAST(1'b0),
        .DMA2_DRREADY(NLW_inst_DMA2_DRREADY_UNCONNECTED),
        .DMA2_DRTYPE({1'b0,1'b0}),
        .DMA2_DRVALID(1'b0),
        .DMA2_RSTN(NLW_inst_DMA2_RSTN_UNCONNECTED),
        .DMA3_ACLK(1'b0),
        .DMA3_DAREADY(1'b0),
        .DMA3_DATYPE(NLW_inst_DMA3_DATYPE_UNCONNECTED[1:0]),
        .DMA3_DAVALID(NLW_inst_DMA3_DAVALID_UNCONNECTED),
        .DMA3_DRLAST(1'b0),
        .DMA3_DRREADY(NLW_inst_DMA3_DRREADY_UNCONNECTED),
        .DMA3_DRTYPE({1'b0,1'b0}),
        .DMA3_DRVALID(1'b0),
        .DMA3_RSTN(NLW_inst_DMA3_RSTN_UNCONNECTED),
        .ENET0_EXT_INTIN(1'b0),
        .ENET0_GMII_COL(1'b0),
        .ENET0_GMII_CRS(1'b0),
        .ENET0_GMII_RXD({1'b0,1'b0,1'b0,1'b0,1'b0,1'b0,1'b0,1'b0}),
        .ENET0_GMII_RX_CLK(1'b0),
        .ENET0_GMII_RX_DV(1'b0),
        .ENET0_GMII_RX_ER(1'b0),
        .ENET0_GMII_TXD(NLW_inst_ENET0_GMII_TXD_UNCONNECTED[7:0]),
        .ENET0_GMII_TX_CLK(1'b0),
        .ENET0_GMII_TX_EN(NLW_inst_ENET0_GMII_TX_EN_UNCONNECTED),
        .ENET0_GMII_TX_ER(NLW_inst_ENET0_GMII_TX_ER_UNCONNECTED),
        .ENET0_MDIO_I(1'b0),
        .ENET0_MDIO_MDC(NLW_inst_ENET0_MDIO_MDC_UNCONNECTED),
        .ENET0_MDIO_O(NLW_inst_ENET0_MDIO_O_UNCONNECTED),
        .ENET0_MDIO_T(NLW_inst_ENET0_MDIO_T_UNCONNECTED),
        .ENET0_PTP_DELAY_REQ_RX(NLW_inst_ENET0_PTP_DELAY_REQ_RX_UNCONNECTED),
        .ENET0_PTP_DELAY_REQ_TX(NLW_inst_ENET0_PTP_DELAY_REQ_TX_UNCONNECTED),
        .ENET0_PTP_PDELAY_REQ_RX(NLW_inst_ENET0_PTP_PDELAY_REQ_RX_UNCONNECTED),
        .ENET0_PTP_PDELAY_REQ_TX(NLW_inst_ENET0_PTP_PDELAY_REQ_TX_UNCONNECTED),
        .ENET0_PTP_PDELAY_RESP_RX(NLW_inst_ENET0_PTP_PDELAY_RESP_RX_UNCONNECTED),
        .ENET0_PTP_PDELAY_RESP_TX(NLW_inst_ENET0_PTP_PDELAY_RESP_TX_UNCONNECTED),
        .ENET0_PTP_SYNC_FRAME_RX(NLW_inst_ENET0_PTP_SYNC_FRAME_RX_UNCONNECTED),
        .ENET0_PTP_SYNC_FRAME_TX(NLW_inst_ENET0_PTP_SYNC_FRAME_TX_UNCONNECTED),
        .ENET0_SOF_RX(NLW_inst_ENET0_SOF_RX_UNCONNECTED),
        .ENET0_SOF_TX(NLW_inst_ENET0_SOF_TX_UNCONNECTED),
        .ENET1_EXT_INTIN(1'b0),
        .ENET1_GMII_COL(1'b0),
        .ENET1_GMII_CRS(1'b0),
        .ENET1_GMII_RXD({1'b0,1'b0,1'b0,1'b0,1'b0,1'b0,1'b0,1'b0}),
        .ENET1_GMII_RX_CLK(1'b0),
        .ENET1_GMII_RX_DV(1'b0),
        .ENET1_GMII_RX_ER(1'b0),
        .ENET1_GMII_TXD(NLW_inst_ENET1_GMII_TXD_UNCONNECTED[7:0]),
        .ENET1_GMII_TX_CLK(1'b0),
        .ENET1_GMII_TX_EN(NLW_inst_ENET1_GMII_TX_EN_UNCONNECTED),
        .ENET1_GMII_TX_ER(NLW_inst_ENET1_GMII_TX_ER_UNCONNECTED),
        .ENET1_MDIO_I(1'b0),
        .ENET1_MDIO_MDC(NLW_inst_ENET1_MDIO_MDC_UNCONNECTED),
        .ENET1_MDIO_O(NLW_inst_ENET1_MDIO_O_UNCONNECTED),
        .ENET1_MDIO_T(NLW_inst_ENET1_MDIO_T_UNCONNECTED),
        .ENET1_PTP_DELAY_REQ_RX(NLW_inst_ENET1_PTP_DELAY_REQ_RX_UNCONNECTED),
        .ENET1_PTP_DELAY_REQ_TX(NLW_inst_ENET1_PTP_DELAY_REQ_TX_UNCONNECTED),
        .ENET1_PTP_PDELAY_REQ_RX(NLW_inst_ENET1_PTP_PDELAY_REQ_RX_UNCONNECTED),
        .ENET1_PTP_PDELAY_REQ_TX(NLW_inst_ENET1_PTP_PDELAY_REQ_TX_UNCONNECTED),
        .ENET1_PTP_PDELAY_RESP_RX(NLW_inst_ENET1_PTP_PDELAY_RESP_RX_UNCONNECTED),
        .ENET1_PTP_PDELAY_RESP_TX(NLW_inst_ENET1_PTP_PDELAY_RESP_TX_UNCONNECTED),
        .ENET1_PTP_SYNC_FRAME_RX(NLW_inst_ENET1_PTP_SYNC_FRAME_RX_UNCONNECTED),
        .ENET1_PTP_SYNC_FRAME_TX(NLW_inst_ENET1_PTP_SYNC_FRAME_TX_UNCONNECTED),
        .ENET1_SOF_RX(NLW_inst_ENET1_SOF_RX_UNCONNECTED),
        .ENET1_SOF_TX(NLW_inst_ENET1_SOF_TX_UNCONNECTED),
        .EVENT_EVENTI(1'b0),
        .EVENT_EVENTO(NLW_inst_EVENT_EVENTO_UNCONNECTED),
        .EVENT_STANDBYWFE(NLW_inst_EVENT_STANDBYWFE_UNCONNECTED[1:0]),
        .EVENT_STANDBYWFI(NLW_inst_EVENT_STANDBYWFI_UNCONNECTED[1:0]),
        .FCLK_CLK0(FCLK_CLK0),
        .FCLK_CLK1(NLW_inst_FCLK_CLK1_UNCONNECTED),
        .FCLK_CLK2(NLW_inst_FCLK_CLK2_UNCONNECTED),
        .FCLK_CLK3(NLW_inst_FCLK_CLK3_UNCONNECTED),
        .FCLK_CLKTRIG0_N(1'b0),
        .FCLK_CLKTRIG1_N(1'b0),
        .FCLK_CLKTRIG2_N(1'b0),
        .FCLK_CLKTRIG3_N(1'b0),
        .FCLK_RESET0_N(FCLK_RESET0_N),
        .FCLK_RESET1_N(NLW_inst_FCLK_RESET1_N_UNCONNECTED),
        .FCLK_RESET2_N(NLW_inst_FCLK_RESET2_N_UNCONNECTED),
        .FCLK_RESET3_N(NLW_inst_FCLK_RESET3_N_UNCONNECTED),
        .FPGA_IDLE_N(1'b0),
        .FTMD_TRACEIN_ATID({1'b0,1'b0,1'b0,1'b0}),
        .FTMD_TRACEIN_CLK(1'b0),
        .FTMD_TRACEIN_DATA({1'b0,1'b0,1'b0,1'b0,1'b0,1'b0,1'b0,1'b0,1'b0,1'b0,1'b0,1'b0,1'b0,1'b0,1'b0,1'b0,1'b0,1'b0,1'b0,1'b0,1'b0,1'b0,1'b0,1'b0,1'b0,1'b0,1'b0,1'b0,1'b0,1'b0,1'b0,1'b0}),
        .FTMD_TRACEIN_VALID(1'b0),
        .FTMT_F2P_DEBUG({1'b0,1'b0,1'b0,1'b0,1'b0,1'b0,1'b0,1'b0,1'b0,1'b0,1'b0,1'b0,1'b0,1'b0,1'b0,1'b0,1'b0,1'b0,1'b0,1'b0,1'b0,1'b0,1'b0,1'b0,1'b0,1'b0,1'b0,1'b0,1'b0,1'b0,1'b0,1'b0}),
        .FTMT_F2P_TRIGACK_0(NLW_inst_FTMT_F2P_TRIGACK_0_UNCONNECTED),
        .FTMT_F2P_TRIGACK_1(NLW_inst_FTMT_F2P_TRIGACK_1_UNCONNECTED),
        .FTMT_F2P_TRIGACK_2(NLW_inst_FTMT_F2P_TRIGACK_2_UNCONNECTED),
        .FTMT_F2P_TRIGACK_3(NLW_inst_FTMT_F2P_TRIGACK_3_UNCONNECTED),
        .FTMT_F2P_TRIG_0(1'b0),
        .FTMT_F2P_TRIG_1(1'b0),
        .FTMT_F2P_TRIG_2(1'b0),
        .FTMT_F2P_TRIG_3(1'b0),
        .FTMT_P2F_DEBUG(NLW_inst_FTMT_P2F_DEBUG_UNCONNECTED[31:0]),
        .FTMT_P2F_TRIGACK_0(1'b0),
        .FTMT_P2F_TRIGACK_1(1'b0),
        .FTMT_P2F_TRIGACK_2(1'b0),
        .FTMT_P2F_TRIGACK_3(1'b0),
        .FTMT_P2F_TRIG_0(NLW_inst_FTMT_P2F_TRIG_0_UNCONNECTED),
        .FTMT_P2F_TRIG_1(NLW_inst_FTMT_P2F_TRIG_1_UNCONNECTED),
        .FTMT_P2F_TRIG_2(NLW_inst_FTMT_P2F_TRIG_2_UNCONNECTED),
        .FTMT_P2F_TRIG_3(NLW_inst_FTMT_P2F_TRIG_3_UNCONNECTED),
        .GPIO_I({1'b0,1'b0,1'b0,1'b0,1'b0,1'b0,1'b0,1'b0,1'b0,1'b0,1'b0,1'b0,1'b0,1'b0,1'b0,1'b0,1'b0,1'b0,1'b0,1'b0,1'b0,1'b0,1'b0,1'b0,1'b0,1'b0,1'b0,1'b0,1'b0,1'b0,1'b0,1'b0,1'b0,1'b0,1'b0,1'b0,1'b0,1'b0,1'b0,1'b0,1'b0,1'b0,1'b0,1'b0,1'b0,1'b0,1'b0,1'b0,1'b0,1'b0,1'b0,1'b0,1'b0,1'b0,1'b0,1'b0,1'b0,1'b0,1'b0,1'b0,1'b0,1'b0,1'b0,1'b0}),
        .GPIO_O(NLW_inst_GPIO_O_UNCONNECTED[63:0]),
        .GPIO_T(NLW_inst_GPIO_T_UNCONNECTED[63:0]),
        .I2C0_SCL_I(1'b0),
        .I2C0_SCL_O(NLW_inst_I2C0_SCL_O_UNCONNECTED),
        .I2C0_SCL_T(NLW_inst_I2C0_SCL_T_UNCONNECTED),
        .I2C0_SDA_I(1'b0),
        .I2C0_SDA_O(NLW_inst_I2C0_SDA_O_UNCONNECTED),
        .I2C0_SDA_T(NLW_inst_I2C0_SDA_T_UNCONNECTED),
        .I2C1_SCL_I(1'b0),
        .I2C1_SCL_O(NLW_inst_I2C1_SCL_O_UNCONNECTED),
        .I2C1_SCL_T(NLW_inst_I2C1_SCL_T_UNCONNECTED),
        .I2C1_SDA_I(1'b0),
        .I2C1_SDA_O(NLW_inst_I2C1_SDA_O_UNCONNECTED),
        .I2C1_SDA_T(NLW_inst_I2C1_SDA_T_UNCONNECTED),
        .IRQ_F2P(1'b0),
        .IRQ_P2F_CAN0(NLW_inst_IRQ_P2F_CAN0_UNCONNECTED),
        .IRQ_P2F_CAN1(NLW_inst_IRQ_P2F_CAN1_UNCONNECTED),
        .IRQ_P2F_CTI(NLW_inst_IRQ_P2F_CTI_UNCONNECTED),
        .IRQ_P2F_DMAC0(NLW_inst_IRQ_P2F_DMAC0_UNCONNECTED),
        .IRQ_P2F_DMAC1(NLW_inst_IRQ_P2F_DMAC1_UNCONNECTED),
        .IRQ_P2F_DMAC2(NLW_inst_IRQ_P2F_DMAC2_UNCONNECTED),
        .IRQ_P2F_DMAC3(NLW_inst_IRQ_P2F_DMAC3_UNCONNECTED),
        .IRQ_P2F_DMAC4(NLW_inst_IRQ_P2F_DMAC4_UNCONNECTED),
        .IRQ_P2F_DMAC5(NLW_inst_IRQ_P2F_DMAC5_UNCONNECTED),
        .IRQ_P2F_DMAC6(NLW_inst_IRQ_P2F_DMAC6_UNCONNECTED),
        .IRQ_P2F_DMAC7(NLW_inst_IRQ_P2F_DMAC7_UNCONNECTED),
        .IRQ_P2F_DMAC_ABORT(NLW_inst_IRQ_P2F_DMAC_ABORT_UNCONNECTED),
        .IRQ_P2F_ENET0(NLW_inst_IRQ_P2F_ENET0_UNCONNECTED),
        .IRQ_P2F_ENET1(NLW_inst_IRQ_P2F_ENET1_UNCONNECTED),
        .IRQ_P2F_ENET_WAKE0(NLW_inst_IRQ_P2F_ENET_WAKE0_UNCONNECTED),
        .IRQ_P2F_ENET_WAKE1(NLW_inst_IRQ_P2F_ENET_WAKE1_UNCONNECTED),
        .IRQ_P2F_GPIO(NLW_inst_IRQ_P2F_GPIO_UNCONNECTED),
        .IRQ_P2F_I2C0(NLW_inst_IRQ_P2F_I2C0_UNCONNECTED),
        .IRQ_P2F_I2C1(NLW_inst_IRQ_P2F_I2C1_UNCONNECTED),
        .IRQ_P2F_QSPI(NLW_inst_IRQ_P2F_QSPI_UNCONNECTED),
        .IRQ_P2F_SDIO0(NLW_inst_IRQ_P2F_SDIO0_UNCONNECTED),
        .IRQ_P2F_SDIO1(NLW_inst_IRQ_P2F_SDIO1_UNCONNECTED),
        .IRQ_P2F_SMC(NLW_inst_IRQ_P2F_SMC_UNCONNECTED),
        .IRQ_P2F_SPI0(NLW_inst_IRQ_P2F_SPI0_UNCONNECTED),
        .IRQ_P2F_SPI1(NLW_inst_IRQ_P2F_SPI1_UNCONNECTED),
        .IRQ_P2F_UART0(NLW_inst_IRQ_P2F_UART0_UNCONNECTED),
        .IRQ_P2F_UART1(NLW_inst_IRQ_P2F_UART1_UNCONNECTED),
        .IRQ_P2F_USB0(NLW_inst_IRQ_P2F_USB0_UNCONNECTED),
        .IRQ_P2F_USB1(NLW_inst_IRQ_P2F_USB1_UNCONNECTED),
        .MIO(MIO),
        .M_AXI_GP0_ACLK(1'b0),
        .M_AXI_GP0_ARADDR(NLW_inst_M_AXI_GP0_ARADDR_UNCONNECTED[31:0]),
        .M_AXI_GP0_ARBURST(NLW_inst_M_AXI_GP0_ARBURST_UNCONNECTED[1:0]),
        .M_AXI_GP0_ARCACHE(NLW_inst_M_AXI_GP0_ARCACHE_UNCONNECTED[3:0]),
        .M_AXI_GP0_ARESETN(NLW_inst_M_AXI_GP0_ARESETN_UNCONNECTED),
        .M_AXI_GP0_ARID(NLW_inst_M_AXI_GP0_ARID_UNCONNECTED[11:0]),
        .M_AXI_GP0_ARLEN(NLW_inst_M_AXI_GP0_ARLEN_UNCONNECTED[3:0]),
        .M_AXI_GP0_ARLOCK(NLW_inst_M_AXI_GP0_ARLOCK_UNCONNECTED[1:0]),
        .M_AXI_GP0_ARPROT(NLW_inst_M_AXI_GP0_ARPROT_UNCONNECTED[2:0]),
        .M_AXI_GP0_ARQOS(NLW_inst_M_AXI_GP0_ARQOS_UNCONNECTED[3:0]),
        .M_AXI_GP0_ARREADY(1'b0),
        .M_AXI_GP0_ARSIZE(NLW_inst_M_AXI_GP0_ARSIZE_UNCONNECTED[2:0]),
        .M_AXI_GP0_ARVALID(NLW_inst_M_AXI_GP0_ARVALID_UNCONNECTED),
        .M_AXI_GP0_AWADDR(NLW_inst_M_AXI_GP0_AWADDR_UNCONNECTED[31:0]),
        .M_AXI_GP0_AWBURST(NLW_inst_M_AXI_GP0_AWBURST_UNCONNECTED[1:0]),
        .M_AXI_GP0_AWCACHE(NLW_inst_M_AXI_GP0_AWCACHE_UNCONNECTED[3:0]),
        .M_AXI_GP0_AWID(NLW_inst_M_AXI_GP0_AWID_UNCONNECTED[11:0]),
        .M_AXI_GP0_AWLEN(NLW_inst_M_AXI_GP0_AWLEN_UNCONNECTED[3:0]),
        .M_AXI_GP0_AWLOCK(NLW_inst_M_AXI_GP0_AWLOCK_UNCONNECTED[1:0]),
        .M_AXI_GP0_AWPROT(NLW_inst_M_AXI_GP0_AWPROT_UNCONNECTED[2:0]),
        .M_AXI_GP0_AWQOS(NLW_inst_M_AXI_GP0_AWQOS_UNCONNECTED[3:0]),
        .M_AXI_GP0_AWREADY(1'b0),
        .M_AXI_GP0_AWSIZE(NLW_inst_M_AXI_GP0_AWSIZE_UNCONNECTED[2:0]),
        .M_AXI_GP0_AWVALID(NLW_inst_M_AXI_GP0_AWVALID_UNCONNECTED),
        .M_AXI_GP0_BID({1'b0,1'b0,1'b0,1'b0,1'b0,1'b0,1'b0,1'b0,1'b0,1'b0,1'b0,1'b0}),
        .M_AXI_GP0_BREADY(NLW_inst_M_AXI_GP0_BREADY_UNCONNECTED),
        .M_AXI_GP0_BRESP({1'b0,1'b0}),
        .M_AXI_GP0_BVALID(1'b0),
        .M_AXI_GP0_RDATA({1'b0,1'b0,1'b0,1'b0,1'b0,1'b0,1'b0,1'b0,1'b0,1'b0,1'b0,1'b0,1'b0,1'b0,1'b0,1'b0,1'b0,1'b0,1'b0,1'b0,1'b0,1'b0,1'b0,1'b0,1'b0,1'b0,1'b0,1'b0,1'b0,1'b0,1'b0,1'b0}),
        .M_AXI_GP0_RID({1'b0,1'b0,1'b0,1'b0,1'b0,1'b0,1'b0,1'b0,1'b0,1'b0,1'b0,1'b0}),
        .M_AXI_GP0_RLAST(1'b0),
        .M_AXI_GP0_RREADY(NLW_inst_M_AXI_GP0_RREADY_UNCONNECTED),
        .M_AXI_GP0_RRESP({1'b0,1'b0}),
        .M_AXI_GP0_RVALID(1'b0),
        .M_AXI_GP0_WDATA(NLW_inst_M_AXI_GP0_WDATA_UNCONNECTED[31:0]),
        .M_AXI_GP0_WID(NLW_inst_M_AXI_GP0_WID_UNCONNECTED[11:0]),
        .M_AXI_GP0_WLAST(NLW_inst_M_AXI_GP0_WLAST_UNCONNECTED),
        .M_AXI_GP0_WREADY(1'b0),
        .M_AXI_GP0_WSTRB(NLW_inst_M_AXI_GP0_WSTRB_UNCONNECTED[3:0]),
        .M_AXI_GP0_WVALID(NLW_inst_M_AXI_GP0_WVALID_UNCONNECTED),
        .M_AXI_GP1_ACLK(1'b0),
        .M_AXI_GP1_ARADDR(NLW_inst_M_AXI_GP1_ARADDR_UNCONNECTED[31:0]),
        .M_AXI_GP1_ARBURST(NLW_inst_M_AXI_GP1_ARBURST_UNCONNECTED[1:0]),
        .M_AXI_GP1_ARCACHE(NLW_inst_M_AXI_GP1_ARCACHE_UNCONNECTED[3:0]),
        .M_AXI_GP1_ARESETN(NLW_inst_M_AXI_GP1_ARESETN_UNCONNECTED),
        .M_AXI_GP1_ARID(NLW_inst_M_AXI_GP1_ARID_UNCONNECTED[11:0]),
        .M_AXI_GP1_ARLEN(NLW_inst_M_AXI_GP1_ARLEN_UNCONNECTED[3:0]),
        .M_AXI_GP1_ARLOCK(NLW_inst_M_AXI_GP1_ARLOCK_UNCONNECTED[1:0]),
        .M_AXI_GP1_ARPROT(NLW_inst_M_AXI_GP1_ARPROT_UNCONNECTED[2:0]),
        .M_AXI_GP1_ARQOS(NLW_inst_M_AXI_GP1_ARQOS_UNCONNECTED[3:0]),
        .M_AXI_GP1_ARREADY(1'b0),
        .M_AXI_GP1_ARSIZE(NLW_inst_M_AXI_GP1_ARSIZE_UNCONNECTED[2:0]),
        .M_AXI_GP1_ARVALID(NLW_inst_M_AXI_GP1_ARVALID_UNCONNECTED),
        .M_AXI_GP1_AWADDR(NLW_inst_M_AXI_GP1_AWADDR_UNCONNECTED[31:0]),
        .M_AXI_GP1_AWBURST(NLW_inst_M_AXI_GP1_AWBURST_UNCONNECTED[1:0]),
        .M_AXI_GP1_AWCACHE(NLW_inst_M_AXI_GP1_AWCACHE_UNCONNECTED[3:0]),
        .M_AXI_GP1_AWID(NLW_inst_M_AXI_GP1_AWID_UNCONNECTED[11:0]),
        .M_AXI_GP1_AWLEN(NLW_inst_M_AXI_GP1_AWLEN_UNCONNECTED[3:0]),
        .M_AXI_GP1_AWLOCK(NLW_inst_M_AXI_GP1_AWLOCK_UNCONNECTED[1:0]),
        .M_AXI_GP1_AWPROT(NLW_inst_M_AXI_GP1_AWPROT_UNCONNECTED[2:0]),
        .M_AXI_GP1_AWQOS(NLW_inst_M_AXI_GP1_AWQOS_UNCONNECTED[3:0]),
        .M_AXI_GP1_AWREADY(1'b0),
        .M_AXI_GP1_AWSIZE(NLW_inst_M_AXI_GP1_AWSIZE_UNCONNECTED[2:0]),
        .M_AXI_GP1_AWVALID(NLW_inst_M_AXI_GP1_AWVALID_UNCONNECTED),
        .M_AXI_GP1_BID({1'b0,1'b0,1'b0,1'b0,1'b0,1'b0,1'b0,1'b0,1'b0,1'b0,1'b0,1'b0}),
        .M_AXI_GP1_BREADY(NLW_inst_M_AXI_GP1_BREADY_UNCONNECTED),
        .M_AXI_GP1_BRESP({1'b0,1'b0}),
        .M_AXI_GP1_BVALID(1'b0),
        .M_AXI_GP1_RDATA({1'b0,1'b0,1'b0,1'b0,1'b0,1'b0,1'b0,1'b0,1'b0,1'b0,1'b0,1'b0,1'b0,1'b0,1'b0,1'b0,1'b0,1'b0,1'b0,1'b0,1'b0,1'b0,1'b0,1'b0,1'b0,1'b0,1'b0,1'b0,1'b0,1'b0,1'b0,1'b0}),
        .M_AXI_GP1_RID({1'b0,1'b0,1'b0,1'b0,1'b0,1'b0,1'b0,1'b0,1'b0,1'b0,1'b0,1'b0}),
        .M_AXI_GP1_RLAST(1'b0),
        .M_AXI_GP1_RREADY(NLW_inst_M_AXI_GP1_RREADY_UNCONNECTED),
        .M_AXI_GP1_RRESP({1'b0,1'b0}),
        .M_AXI_GP1_RVALID(1'b0),
        .M_AXI_GP1_WDATA(NLW_inst_M_AXI_GP1_WDATA_UNCONNECTED[31:0]),
        .M_AXI_GP1_WID(NLW_inst_M_AXI_GP1_WID_UNCONNECTED[11:0]),
        .M_AXI_GP1_WLAST(NLW_inst_M_AXI_GP1_WLAST_UNCONNECTED),
        .M_AXI_GP1_WREADY(1'b0),
        .M_AXI_GP1_WSTRB(NLW_inst_M_AXI_GP1_WSTRB_UNCONNECTED[3:0]),
        .M_AXI_GP1_WVALID(NLW_inst_M_AXI_GP1_WVALID_UNCONNECTED),
        .PJTAG_TCK(1'b0),
        .PJTAG_TDI(1'b0),
        .PJTAG_TDO(NLW_inst_PJTAG_TDO_UNCONNECTED),
        .PJTAG_TMS(1'b0),
        .PS_CLK(PS_CLK),
        .PS_PORB(PS_PORB),
        .PS_SRSTB(PS_SRSTB),
        .SDIO0_BUSPOW(NLW_inst_SDIO0_BUSPOW_UNCONNECTED),
        .SDIO0_BUSVOLT(NLW_inst_SDIO0_BUSVOLT_UNCONNECTED[2:0]),
        .SDIO0_CDN(1'b0),
        .SDIO0_CLK(NLW_inst_SDIO0_CLK_UNCONNECTED),
        .SDIO0_CLK_FB(1'b0),
        .SDIO0_CMD_I(1'b0),
        .SDIO0_CMD_O(NLW_inst_SDIO0_CMD_O_UNCONNECTED),
        .SDIO0_CMD_T(NLW_inst_SDIO0_CMD_T_UNCONNECTED),
        .SDIO0_DATA_I({1'b0,1'b0,1'b0,1'b0}),
        .SDIO0_DATA_O(NLW_inst_SDIO0_DATA_O_UNCONNECTED[3:0]),
        .SDIO0_DATA_T(NLW_inst_SDIO0_DATA_T_UNCONNECTED[3:0]),
        .SDIO0_LED(NLW_inst_SDIO0_LED_UNCONNECTED),
        .SDIO0_WP(1'b0),
        .SDIO1_BUSPOW(NLW_inst_SDIO1_BUSPOW_UNCONNECTED),
        .SDIO1_BUSVOLT(NLW_inst_SDIO1_BUSVOLT_UNCONNECTED[2:0]),
        .SDIO1_CDN(1'b0),
        .SDIO1_CLK(NLW_inst_SDIO1_CLK_UNCONNECTED),
        .SDIO1_CLK_FB(1'b0),
        .SDIO1_CMD_I(1'b0),
        .SDIO1_CMD_O(NLW_inst_SDIO1_CMD_O_UNCONNECTED),
        .SDIO1_CMD_T(NLW_inst_SDIO1_CMD_T_UNCONNECTED),
        .SDIO1_DATA_I({1'b0,1'b0,1'b0,1'b0}),
        .SDIO1_DATA_O(NLW_inst_SDIO1_DATA_O_UNCONNECTED[3:0]),
        .SDIO1_DATA_T(NLW_inst_SDIO1_DATA_T_UNCONNECTED[3:0]),
        .SDIO1_LED(NLW_inst_SDIO1_LED_UNCONNECTED),
        .SDIO1_WP(1'b0),
        .SPI0_MISO_I(1'b0),
        .SPI0_MISO_O(NLW_inst_SPI0_MISO_O_UNCONNECTED),
        .SPI0_MISO_T(NLW_inst_SPI0_MISO_T_UNCONNECTED),
        .SPI0_MOSI_I(1'b0),
        .SPI0_MOSI_O(NLW_inst_SPI0_MOSI_O_UNCONNECTED),
        .SPI0_MOSI_T(NLW_inst_SPI0_MOSI_T_UNCONNECTED),
        .SPI0_SCLK_I(1'b0),
        .SPI0_SCLK_O(NLW_inst_SPI0_SCLK_O_UNCONNECTED),
        .SPI0_SCLK_T(NLW_inst_SPI0_SCLK_T_UNCONNECTED),
        .SPI0_SS1_O(NLW_inst_SPI0_SS1_O_UNCONNECTED),
        .SPI0_SS2_O(NLW_inst_SPI0_SS2_O_UNCONNECTED),
        .SPI0_SS_I(1'b0),
        .SPI0_SS_O(NLW_inst_SPI0_SS_O_UNCONNECTED),
        .SPI0_SS_T(NLW_inst_SPI0_SS_T_UNCONNECTED),
        .SPI1_MISO_I(1'b0),
        .SPI1_MISO_O(NLW_inst_SPI1_MISO_O_UNCONNECTED),
        .SPI1_MISO_T(NLW_inst_SPI1_MISO_T_UNCONNECTED),
        .SPI1_MOSI_I(1'b0),
        .SPI1_MOSI_O(NLW_inst_SPI1_MOSI_O_UNCONNECTED),
        .SPI1_MOSI_T(NLW_inst_SPI1_MOSI_T_UNCONNECTED),
        .SPI1_SCLK_I(1'b0),
        .SPI1_SCLK_O(NLW_inst_SPI1_SCLK_O_UNCONNECTED),
        .SPI1_SCLK_T(NLW_inst_SPI1_SCLK_T_UNCONNECTED),
        .SPI1_SS1_O(NLW_inst_SPI1_SS1_O_UNCONNECTED),
        .SPI1_SS2_O(NLW_inst_SPI1_SS2_O_UNCONNECTED),
        .SPI1_SS_I(1'b0),
        .SPI1_SS_O(NLW_inst_SPI1_SS_O_UNCONNECTED),
        .SPI1_SS_T(NLW_inst_SPI1_SS_T_UNCONNECTED),
        .SRAM_INTIN(1'b0),
        .S_AXI_ACP_ACLK(1'b0),
        .S_AXI_ACP_ARADDR({1'b0,1'b0,1'b0,1'b0,1'b0,1'b0,1'b0,1'b0,1'b0,1'b0,1'b0,1'b0,1'b0,1'b0,1'b0,1'b0,1'b0,1'b0,1'b0,1'b0,1'b0,1'b0,1'b0,1'b0,1'b0,1'b0,1'b0,1'b0,1'b0,1'b0,1'b0,1'b0}),
        .S_AXI_ACP_ARBURST({1'b0,1'b0}),
        .S_AXI_ACP_ARCACHE({1'b0,1'b0,1'b0,1'b0}),
        .S_AXI_ACP_ARESETN(NLW_inst_S_AXI_ACP_ARESETN_UNCONNECTED),
        .S_AXI_ACP_ARID({1'b0,1'b0,1'b0}),
        .S_AXI_ACP_ARLEN({1'b0,1'b0,1'b0,1'b0}),
        .S_AXI_ACP_ARLOCK({1'b0,1'b0}),
        .S_AXI_ACP_ARPROT({1'b0,1'b0,1'b0}),
        .S_AXI_ACP_ARQOS({1'b0,1'b0,1'b0,1'b0}),
        .S_AXI_ACP_ARREADY(NLW_inst_S_AXI_ACP_ARREADY_UNCONNECTED),
        .S_AXI_ACP_ARSIZE({1'b0,1'b0,1'b0}),
        .S_AXI_ACP_ARUSER({1'b0,1'b0,1'b0,1'b0,1'b0}),
        .S_AXI_ACP_ARVALID(1'b0),
        .S_AXI_ACP_AWADDR({1'b0,1'b0,1'b0,1'b0,1'b0,1'b0,1'b0,1'b0,1'b0,1'b0,1'b0,1'b0,1'b0,1'b0,1'b0,1'b0,1'b0,1'b0,1'b0,1'b0,1'b0,1'b0,1'b0,1'b0,1'b0,1'b0,1'b0,1'b0,1'b0,1'b0,1'b0,1'b0}),
        .S_AXI_ACP_AWBURST({1'b0,1'b0}),
        .S_AXI_ACP_AWCACHE({1'b0,1'b0,1'b0,1'b0}),
        .S_AXI_ACP_AWID({1'b0,1'b0,1'b0}),
        .S_AXI_ACP_AWLEN({1'b0,1'b0,1'b0,1'b0}),
        .S_AXI_ACP_AWLOCK({1'b0,1'b0}),
        .S_AXI_ACP_AWPROT({1'b0,1'b0,1'b0}),
        .S_AXI_ACP_AWQOS({1'b0,1'b0,1'b0,1'b0}),
        .S_AXI_ACP_AWREADY(NLW_inst_S_AXI_ACP_AWREADY_UNCONNECTED),
        .S_AXI_ACP_AWSIZE({1'b0,1'b0,1'b0}),
        .S_AXI_ACP_AWUSER({1'b0,1'b0,1'b0,1'b0,1'b0}),
        .S_AXI_ACP_AWVALID(1'b0),
        .S_AXI_ACP_BID(NLW_inst_S_AXI_ACP_BID_UNCONNECTED[2:0]),
        .S_AXI_ACP_BREADY(1'b0),
        .S_AXI_ACP_BRESP(NLW_inst_S_AXI_ACP_BRESP_UNCONNECTED[1:0]),
        .S_AXI_ACP_BVALID(NLW_inst_S_AXI_ACP_BVALID_UNCONNECTED),
        .S_AXI_ACP_RDATA(NLW_inst_S_AXI_ACP_RDATA_UNCONNECTED[63:0]),
        .S_AXI_ACP_RID(NLW_inst_S_AXI_ACP_RID_UNCONNECTED[2:0]),
        .S_AXI_ACP_RLAST(NLW_inst_S_AXI_ACP_RLAST_UNCONNECTED),
        .S_AXI_ACP_RREADY(1'b0),
        .S_AXI_ACP_RRESP(NLW_inst_S_AXI_ACP_RRESP_UNCONNECTED[1:0]),
        .S_AXI_ACP_RVALID(NLW_inst_S_AXI_ACP_RVALID_UNCONNECTED),
        .S_AXI_ACP_WDATA({1'b0,1'b0,1'b0,1'b0,1'b0,1'b0,1'b0,1'b0,1'b0,1'b0,1'b0,1'b0,1'b0,1'b0,1'b0,1'b0,1'b0,1'b0,1'b0,1'b0,1'b0,1'b0,1'b0,1'b0,1'b0,1'b0,1'b0,1'b0,1'b0,1'b0,1'b0,1'b0,1'b0,1'b0,1'b0,1'b0,1'b0,1'b0,1'b0,1'b0,1'b0,1'b0,1'b0,1'b0,1'b0,1'b0,1'b0,1'b0,1'b0,1'b0,1'b0,1'b0,1'b0,1'b0,1'b0,1'b0,1'b0,1'b0,1'b0,1'b0,1'b0,1'b0,1'b0,1'b0}),
        .S_AXI_ACP_WID({1'b0,1'b0,1'b0}),
        .S_AXI_ACP_WLAST(1'b0),
        .S_AXI_ACP_WREADY(NLW_inst_S_AXI_ACP_WREADY_UNCONNECTED),
        .S_AXI_ACP_WSTRB({1'b0,1'b0,1'b0,1'b0,1'b0,1'b0,1'b0,1'b0}),
        .S_AXI_ACP_WVALID(1'b0),
        .S_AXI_GP0_ACLK(1'b0),
        .S_AXI_GP0_ARADDR({1'b0,1'b0,1'b0,1'b0,1'b0,1'b0,1'b0,1'b0,1'b0,1'b0,1'b0,1'b0,1'b0,1'b0,1'b0,1'b0,1'b0,1'b0,1'b0,1'b0,1'b0,1'b0,1'b0,1'b0,1'b0,1'b0,1'b0,1'b0,1'b0,1'b0,1'b0,1'b0}),
        .S_AXI_GP0_ARBURST({1'b0,1'b0}),
        .S_AXI_GP0_ARCACHE({1'b0,1'b0,1'b0,1'b0}),
        .S_AXI_GP0_ARESETN(NLW_inst_S_AXI_GP0_ARESETN_UNCONNECTED),
        .S_AXI_GP0_ARID({1'b0,1'b0,1'b0,1'b0,1'b0,1'b0}),
        .S_AXI_GP0_ARLEN({1'b0,1'b0,1'b0,1'b0}),
        .S_AXI_GP0_ARLOCK({1'b0,1'b0}),
        .S_AXI_GP0_ARPROT({1'b0,1'b0,1'b0}),
        .S_AXI_GP0_ARQOS({1'b0,1'b0,1'b0,1'b0}),
        .S_AXI_GP0_ARREADY(NLW_inst_S_AXI_GP0_ARREADY_UNCONNECTED),
        .S_AXI_GP0_ARSIZE({1'b0,1'b0,1'b0}),
        .S_AXI_GP0_ARVALID(1'b0),
        .S_AXI_GP0_AWADDR({1'b0,1'b0,1'b0,1'b0,1'b0,1'b0,1'b0,1'b0,1'b0,1'b0,1'b0,1'b0,1'b0,1'b0,1'b0,1'b0,1'b0,1'b0,1'b0,1'b0,1'b0,1'b0,1'b0,1'b0,1'b0,1'b0,1'b0,1'b0,1'b0,1'b0,1'b0,1'b0}),
        .S_AXI_GP0_AWBURST({1'b0,1'b0}),
        .S_AXI_GP0_AWCACHE({1'b0,1'b0,1'b0,1'b0}),
        .S_AXI_GP0_AWID({1'b0,1'b0,1'b0,1'b0,1'b0,1'b0}),
        .S_AXI_GP0_AWLEN({1'b0,1'b0,1'b0,1'b0}),
        .S_AXI_GP0_AWLOCK({1'b0,1'b0}),
        .S_AXI_GP0_AWPROT({1'b0,1'b0,1'b0}),
        .S_AXI_GP0_AWQOS({1'b0,1'b0,1'b0,1'b0}),
        .S_AXI_GP0_AWREADY(NLW_inst_S_AXI_GP0_AWREADY_UNCONNECTED),
        .S_AXI_GP0_AWSIZE({1'b0,1'b0,1'b0}),
        .S_AXI_GP0_AWVALID(1'b0),
        .S_AXI_GP0_BID(NLW_inst_S_AXI_GP0_BID_UNCONNECTED[5:0]),
        .S_AXI_GP0_BREADY(1'b0),
        .S_AXI_GP0_BRESP(NLW_inst_S_AXI_GP0_BRESP_UNCONNECTED[1:0]),
        .S_AXI_GP0_BVALID(NLW_inst_S_AXI_GP0_BVALID_UNCONNECTED),
        .S_AXI_GP0_RDATA(NLW_inst_S_AXI_GP0_RDATA_UNCONNECTED[31:0]),
        .S_AXI_GP0_RID(NLW_inst_S_AXI_GP0_RID_UNCONNECTED[5:0]),
        .S_AXI_GP0_RLAST(NLW_inst_S_AXI_GP0_RLAST_UNCONNECTED),
        .S_AXI_GP0_RREADY(1'b0),
        .S_AXI_GP0_RRESP(NLW_inst_S_AXI_GP0_RRESP_UNCONNECTED[1:0]),
        .S_AXI_GP0_RVALID(NLW_inst_S_AXI_GP0_RVALID_UNCONNECTED),
        .S_AXI_GP0_WDATA({1'b0,1'b0,1'b0,1'b0,1'b0,1'b0,1'b0,1'b0,1'b0,1'b0,1'b0,1'b0,1'b0,1'b0,1'b0,1'b0,1'b0,1'b0,1'b0,1'b0,1'b0,1'b0,1'b0,1'b0,1'b0,1'b0,1'b0,1'b0,1'b0,1'b0,1'b0,1'b0}),
        .S_AXI_GP0_WID({1'b0,1'b0,1'b0,1'b0,1'b0,1'b0}),
        .S_AXI_GP0_WLAST(1'b0),
        .S_AXI_GP0_WREADY(NLW_inst_S_AXI_GP0_WREADY_UNCONNECTED),
        .S_AXI_GP0_WSTRB({1'b0,1'b0,1'b0,1'b0}),
        .S_AXI_GP0_WVALID(1'b0),
        .S_AXI_GP1_ACLK(1'b0),
        .S_AXI_GP1_ARADDR({1'b0,1'b0,1'b0,1'b0,1'b0,1'b0,1'b0,1'b0,1'b0,1'b0,1'b0,1'b0,1'b0,1'b0,1'b0,1'b0,1'b0,1'b0,1'b0,1'b0,1'b0,1'b0,1'b0,1'b0,1'b0,1'b0,1'b0,1'b0,1'b0,1'b0,1'b0,1'b0}),
        .S_AXI_GP1_ARBURST({1'b0,1'b0}),
        .S_AXI_GP1_ARCACHE({1'b0,1'b0,1'b0,1'b0}),
        .S_AXI_GP1_ARESETN(NLW_inst_S_AXI_GP1_ARESETN_UNCONNECTED),
        .S_AXI_GP1_ARID({1'b0,1'b0,1'b0,1'b0,1'b0,1'b0}),
        .S_AXI_GP1_ARLEN({1'b0,1'b0,1'b0,1'b0}),
        .S_AXI_GP1_ARLOCK({1'b0,1'b0}),
        .S_AXI_GP1_ARPROT({1'b0,1'b0,1'b0}),
        .S_AXI_GP1_ARQOS({1'b0,1'b0,1'b0,1'b0}),
        .S_AXI_GP1_ARREADY(NLW_inst_S_AXI_GP1_ARREADY_UNCONNECTED),
        .S_AXI_GP1_ARSIZE({1'b0,1'b0,1'b0}),
        .S_AXI_GP1_ARVALID(1'b0),
        .S_AXI_GP1_AWADDR({1'b0,1'b0,1'b0,1'b0,1'b0,1'b0,1'b0,1'b0,1'b0,1'b0,1'b0,1'b0,1'b0,1'b0,1'b0,1'b0,1'b0,1'b0,1'b0,1'b0,1'b0,1'b0,1'b0,1'b0,1'b0,1'b0,1'b0,1'b0,1'b0,1'b0,1'b0,1'b0}),
        .S_AXI_GP1_AWBURST({1'b0,1'b0}),
        .S_AXI_GP1_AWCACHE({1'b0,1'b0,1'b0,1'b0}),
        .S_AXI_GP1_AWID({1'b0,1'b0,1'b0,1'b0,1'b0,1'b0}),
        .S_AXI_GP1_AWLEN({1'b0,1'b0,1'b0,1'b0}),
        .S_AXI_GP1_AWLOCK({1'b0,1'b0}),
        .S_AXI_GP1_AWPROT({1'b0,1'b0,1'b0}),
        .S_AXI_GP1_AWQOS({1'b0,1'b0,1'b0,1'b0}),
        .S_AXI_GP1_AWREADY(NLW_inst_S_AXI_GP1_AWREADY_UNCONNECTED),
        .S_AXI_GP1_AWSIZE({1'b0,1'b0,1'b0}),
        .S_AXI_GP1_AWVALID(1'b0),
        .S_AXI_GP1_BID(NLW_inst_S_AXI_GP1_BID_UNCONNECTED[5:0]),
        .S_AXI_GP1_BREADY(1'b0),
        .S_AXI_GP1_BRESP(NLW_inst_S_AXI_GP1_BRESP_UNCONNECTED[1:0]),
        .S_AXI_GP1_BVALID(NLW_inst_S_AXI_GP1_BVALID_UNCONNECTED),
        .S_AXI_GP1_RDATA(NLW_inst_S_AXI_GP1_RDATA_UNCONNECTED[31:0]),
        .S_AXI_GP1_RID(NLW_inst_S_AXI_GP1_RID_UNCONNECTED[5:0]),
        .S_AXI_GP1_RLAST(NLW_inst_S_AXI_GP1_RLAST_UNCONNECTED),
        .S_AXI_GP1_RREADY(1'b0),
        .S_AXI_GP1_RRESP(NLW_inst_S_AXI_GP1_RRESP_UNCONNECTED[1:0]),
        .S_AXI_GP1_RVALID(NLW_inst_S_AXI_GP1_RVALID_UNCONNECTED),
        .S_AXI_GP1_WDATA({1'b0,1'b0,1'b0,1'b0,1'b0,1'b0,1'b0,1'b0,1'b0,1'b0,1'b0,1'b0,1'b0,1'b0,1'b0,1'b0,1'b0,1'b0,1'b0,1'b0,1'b0,1'b0,1'b0,1'b0,1'b0,1'b0,1'b0,1'b0,1'b0,1'b0,1'b0,1'b0}),
        .S_AXI_GP1_WID({1'b0,1'b0,1'b0,1'b0,1'b0,1'b0}),
        .S_AXI_GP1_WLAST(1'b0),
        .S_AXI_GP1_WREADY(NLW_inst_S_AXI_GP1_WREADY_UNCONNECTED),
        .S_AXI_GP1_WSTRB({1'b0,1'b0,1'b0,1'b0}),
        .S_AXI_GP1_WVALID(1'b0),
        .S_AXI_HP0_ACLK(1'b0),
        .S_AXI_HP0_ARADDR({1'b0,1'b0,1'b0,1'b0,1'b0,1'b0,1'b0,1'b0,1'b0,1'b0,1'b0,1'b0,1'b0,1'b0,1'b0,1'b0,1'b0,1'b0,1'b0,1'b0,1'b0,1'b0,1'b0,1'b0,1'b0,1'b0,1'b0,1'b0,1'b0,1'b0,1'b0,1'b0}),
        .S_AXI_HP0_ARBURST({1'b0,1'b0}),
        .S_AXI_HP0_ARCACHE({1'b0,1'b0,1'b0,1'b0}),
        .S_AXI_HP0_ARESETN(NLW_inst_S_AXI_HP0_ARESETN_UNCONNECTED),
        .S_AXI_HP0_ARID({1'b0,1'b0,1'b0,1'b0,1'b0,1'b0}),
        .S_AXI_HP0_ARLEN({1'b0,1'b0,1'b0,1'b0}),
        .S_AXI_HP0_ARLOCK({1'b0,1'b0}),
        .S_AXI_HP0_ARPROT({1'b0,1'b0,1'b0}),
        .S_AXI_HP0_ARQOS({1'b0,1'b0,1'b0,1'b0}),
        .S_AXI_HP0_ARREADY(NLW_inst_S_AXI_HP0_ARREADY_UNCONNECTED),
        .S_AXI_HP0_ARSIZE({1'b0,1'b0,1'b0}),
        .S_AXI_HP0_ARVALID(1'b0),
        .S_AXI_HP0_AWADDR({1'b0,1'b0,1'b0,1'b0,1'b0,1'b0,1'b0,1'b0,1'b0,1'b0,1'b0,1'b0,1'b0,1'b0,1'b0,1'b0,1'b0,1'b0,1'b0,1'b0,1'b0,1'b0,1'b0,1'b0,1'b0,1'b0,1'b0,1'b0,1'b0,1'b0,1'b0,1'b0}),
        .S_AXI_HP0_AWBURST({1'b0,1'b0}),
        .S_AXI_HP0_AWCACHE({1'b0,1'b0,1'b0,1'b0}),
        .S_AXI_HP0_AWID({1'b0,1'b0,1'b0,1'b0,1'b0,1'b0}),
        .S_AXI_HP0_AWLEN({1'b0,1'b0,1'b0,1'b0}),
        .S_AXI_HP0_AWLOCK({1'b0,1'b0}),
        .S_AXI_HP0_AWPROT({1'b0,1'b0,1'b0}),
        .S_AXI_HP0_AWQOS({1'b0,1'b0,1'b0,1'b0}),
        .S_AXI_HP0_AWREADY(NLW_inst_S_AXI_HP0_AWREADY_UNCONNECTED),
        .S_AXI_HP0_AWSIZE({1'b0,1'b0,1'b0}),
        .S_AXI_HP0_AWVALID(1'b0),
        .S_AXI_HP0_BID(NLW_inst_S_AXI_HP0_BID_UNCONNECTED[5:0]),
        .S_AXI_HP0_BREADY(1'b0),
        .S_AXI_HP0_BRESP(NLW_inst_S_AXI_HP0_BRESP_UNCONNECTED[1:0]),
        .S_AXI_HP0_BVALID(NLW_inst_S_AXI_HP0_BVALID_UNCONNECTED),
        .S_AXI_HP0_RACOUNT(NLW_inst_S_AXI_HP0_RACOUNT_UNCONNECTED[2:0]),
        .S_AXI_HP0_RCOUNT(NLW_inst_S_AXI_HP0_RCOUNT_UNCONNECTED[7:0]),
        .S_AXI_HP0_RDATA(NLW_inst_S_AXI_HP0_RDATA_UNCONNECTED[63:0]),
        .S_AXI_HP0_RDISSUECAP1_EN(1'b0),
        .S_AXI_HP0_RID(NLW_inst_S_AXI_HP0_RID_UNCONNECTED[5:0]),
        .S_AXI_HP0_RLAST(NLW_inst_S_AXI_HP0_RLAST_UNCONNECTED),
        .S_AXI_HP0_RREADY(1'b0),
        .S_AXI_HP0_RRESP(NLW_inst_S_AXI_HP0_RRESP_UNCONNECTED[1:0]),
        .S_AXI_HP0_RVALID(NLW_inst_S_AXI_HP0_RVALID_UNCONNECTED),
        .S_AXI_HP0_WACOUNT(NLW_inst_S_AXI_HP0_WACOUNT_UNCONNECTED[5:0]),
        .S_AXI_HP0_WCOUNT(NLW_inst_S_AXI_HP0_WCOUNT_UNCONNECTED[7:0]),
        .S_AXI_HP0_WDATA({1'b0,1'b0,1'b0,1'b0,1'b0,1'b0,1'b0,1'b0,1'b0,1'b0,1'b0,1'b0,1'b0,1'b0,1'b0,1'b0,1'b0,1'b0,1'b0,1'b0,1'b0,1'b0,1'b0,1'b0,1'b0,1'b0,1'b0,1'b0,1'b0,1'b0,1'b0,1'b0,1'b0,1'b0,1'b0,1'b0,1'b0,1'b0,1'b0,1'b0,1'b0,1'b0,1'b0,1'b0,1'b0,1'b0,1'b0,1'b0,1'b0,1'b0,1'b0,1'b0,1'b0,1'b0,1'b0,1'b0,1'b0,1'b0,1'b0,1'b0,1'b0,1'b0,1'b0,1'b0}),
        .S_AXI_HP0_WID({1'b0,1'b0,1'b0,1'b0,1'b0,1'b0}),
        .S_AXI_HP0_WLAST(1'b0),
        .S_AXI_HP0_WREADY(NLW_inst_S_AXI_HP0_WREADY_UNCONNECTED),
        .S_AXI_HP0_WRISSUECAP1_EN(1'b0),
        .S_AXI_HP0_WSTRB({1'b0,1'b0,1'b0,1'b0,1'b0,1'b0,1'b0,1'b0}),
        .S_AXI_HP0_WVALID(1'b0),
        .S_AXI_HP1_ACLK(1'b0),
        .S_AXI_HP1_ARADDR({1'b0,1'b0,1'b0,1'b0,1'b0,1'b0,1'b0,1'b0,1'b0,1'b0,1'b0,1'b0,1'b0,1'b0,1'b0,1'b0,1'b0,1'b0,1'b0,1'b0,1'b0,1'b0,1'b0,1'b0,1'b0,1'b0,1'b0,1'b0,1'b0,1'b0,1'b0,1'b0}),
        .S_AXI_HP1_ARBURST({1'b0,1'b0}),
        .S_AXI_HP1_ARCACHE({1'b0,1'b0,1'b0,1'b0}),
        .S_AXI_HP1_ARESETN(NLW_inst_S_AXI_HP1_ARESETN_UNCONNECTED),
        .S_AXI_HP1_ARID({1'b0,1'b0,1'b0,1'b0,1'b0,1'b0}),
        .S_AXI_HP1_ARLEN({1'b0,1'b0,1'b0,1'b0}),
        .S_AXI_HP1_ARLOCK({1'b0,1'b0}),
        .S_AXI_HP1_ARPROT({1'b0,1'b0,1'b0}),
        .S_AXI_HP1_ARQOS({1'b0,1'b0,1'b0,1'b0}),
        .S_AXI_HP1_ARREADY(NLW_inst_S_AXI_HP1_ARREADY_UNCONNECTED),
        .S_AXI_HP1_ARSIZE({1'b0,1'b0,1'b0}),
        .S_AXI_HP1_ARVALID(1'b0),
        .S_AXI_HP1_AWADDR({1'b0,1'b0,1'b0,1'b0,1'b0,1'b0,1'b0,1'b0,1'b0,1'b0,1'b0,1'b0,1'b0,1'b0,1'b0,1'b0,1'b0,1'b0,1'b0,1'b0,1'b0,1'b0,1'b0,1'b0,1'b0,1'b0,1'b0,1'b0,1'b0,1'b0,1'b0,1'b0}),
        .S_AXI_HP1_AWBURST({1'b0,1'b0}),
        .S_AXI_HP1_AWCACHE({1'b0,1'b0,1'b0,1'b0}),
        .S_AXI_HP1_AWID({1'b0,1'b0,1'b0,1'b0,1'b0,1'b0}),
        .S_AXI_HP1_AWLEN({1'b0,1'b0,1'b0,1'b0}),
        .S_AXI_HP1_AWLOCK({1'b0,1'b0}),
        .S_AXI_HP1_AWPROT({1'b0,1'b0,1'b0}),
        .S_AXI_HP1_AWQOS({1'b0,1'b0,1'b0,1'b0}),
        .S_AXI_HP1_AWREADY(NLW_inst_S_AXI_HP1_AWREADY_UNCONNECTED),
        .S_AXI_HP1_AWSIZE({1'b0,1'b0,1'b0}),
        .S_AXI_HP1_AWVALID(1'b0),
        .S_AXI_HP1_BID(NLW_inst_S_AXI_HP1_BID_UNCONNECTED[5:0]),
        .S_AXI_HP1_BREADY(1'b0),
        .S_AXI_HP1_BRESP(NLW_inst_S_AXI_HP1_BRESP_UNCONNECTED[1:0]),
        .S_AXI_HP1_BVALID(NLW_inst_S_AXI_HP1_BVALID_UNCONNECTED),
        .S_AXI_HP1_RACOUNT(NLW_inst_S_AXI_HP1_RACOUNT_UNCONNECTED[2:0]),
        .S_AXI_HP1_RCOUNT(NLW_inst_S_AXI_HP1_RCOUNT_UNCONNECTED[7:0]),
        .S_AXI_HP1_RDATA(NLW_inst_S_AXI_HP1_RDATA_UNCONNECTED[63:0]),
        .S_AXI_HP1_RDISSUECAP1_EN(1'b0),
        .S_AXI_HP1_RID(NLW_inst_S_AXI_HP1_RID_UNCONNECTED[5:0]),
        .S_AXI_HP1_RLAST(NLW_inst_S_AXI_HP1_RLAST_UNCONNECTED),
        .S_AXI_HP1_RREADY(1'b0),
        .S_AXI_HP1_RRESP(NLW_inst_S_AXI_HP1_RRESP_UNCONNECTED[1:0]),
        .S_AXI_HP1_RVALID(NLW_inst_S_AXI_HP1_RVALID_UNCONNECTED),
        .S_AXI_HP1_WACOUNT(NLW_inst_S_AXI_HP1_WACOUNT_UNCONNECTED[5:0]),
        .S_AXI_HP1_WCOUNT(NLW_inst_S_AXI_HP1_WCOUNT_UNCONNECTED[7:0]),
        .S_AXI_HP1_WDATA({1'b0,1'b0,1'b0,1'b0,1'b0,1'b0,1'b0,1'b0,1'b0,1'b0,1'b0,1'b0,1'b0,1'b0,1'b0,1'b0,1'b0,1'b0,1'b0,1'b0,1'b0,1'b0,1'b0,1'b0,1'b0,1'b0,1'b0,1'b0,1'b0,1'b0,1'b0,1'b0,1'b0,1'b0,1'b0,1'b0,1'b0,1'b0,1'b0,1'b0,1'b0,1'b0,1'b0,1'b0,1'b0,1'b0,1'b0,1'b0,1'b0,1'b0,1'b0,1'b0,1'b0,1'b0,1'b0,1'b0,1'b0,1'b0,1'b0,1'b0,1'b0,1'b0,1'b0,1'b0}),
        .S_AXI_HP1_WID({1'b0,1'b0,1'b0,1'b0,1'b0,1'b0}),
        .S_AXI_HP1_WLAST(1'b0),
        .S_AXI_HP1_WREADY(NLW_inst_S_AXI_HP1_WREADY_UNCONNECTED),
        .S_AXI_HP1_WRISSUECAP1_EN(1'b0),
        .S_AXI_HP1_WSTRB({1'b0,1'b0,1'b0,1'b0,1'b0,1'b0,1'b0,1'b0}),
        .S_AXI_HP1_WVALID(1'b0),
        .S_AXI_HP2_ACLK(1'b0),
        .S_AXI_HP2_ARADDR({1'b0,1'b0,1'b0,1'b0,1'b0,1'b0,1'b0,1'b0,1'b0,1'b0,1'b0,1'b0,1'b0,1'b0,1'b0,1'b0,1'b0,1'b0,1'b0,1'b0,1'b0,1'b0,1'b0,1'b0,1'b0,1'b0,1'b0,1'b0,1'b0,1'b0,1'b0,1'b0}),
        .S_AXI_HP2_ARBURST({1'b0,1'b0}),
        .S_AXI_HP2_ARCACHE({1'b0,1'b0,1'b0,1'b0}),
        .S_AXI_HP2_ARESETN(NLW_inst_S_AXI_HP2_ARESETN_UNCONNECTED),
        .S_AXI_HP2_ARID({1'b0,1'b0,1'b0,1'b0,1'b0,1'b0}),
        .S_AXI_HP2_ARLEN({1'b0,1'b0,1'b0,1'b0}),
        .S_AXI_HP2_ARLOCK({1'b0,1'b0}),
        .S_AXI_HP2_ARPROT({1'b0,1'b0,1'b0}),
        .S_AXI_HP2_ARQOS({1'b0,1'b0,1'b0,1'b0}),
        .S_AXI_HP2_ARREADY(NLW_inst_S_AXI_HP2_ARREADY_UNCONNECTED),
        .S_AXI_HP2_ARSIZE({1'b0,1'b0,1'b0}),
        .S_AXI_HP2_ARVALID(1'b0),
        .S_AXI_HP2_AWADDR({1'b0,1'b0,1'b0,1'b0,1'b0,1'b0,1'b0,1'b0,1'b0,1'b0,1'b0,1'b0,1'b0,1'b0,1'b0,1'b0,1'b0,1'b0,1'b0,1'b0,1'b0,1'b0,1'b0,1'b0,1'b0,1'b0,1'b0,1'b0,1'b0,1'b0,1'b0,1'b0}),
        .S_AXI_HP2_AWBURST({1'b0,1'b0}),
        .S_AXI_HP2_AWCACHE({1'b0,1'b0,1'b0,1'b0}),
        .S_AXI_HP2_AWID({1'b0,1'b0,1'b0,1'b0,1'b0,1'b0}),
        .S_AXI_HP2_AWLEN({1'b0,1'b0,1'b0,1'b0}),
        .S_AXI_HP2_AWLOCK({1'b0,1'b0}),
        .S_AXI_HP2_AWPROT({1'b0,1'b0,1'b0}),
        .S_AXI_HP2_AWQOS({1'b0,1'b0,1'b0,1'b0}),
        .S_AXI_HP2_AWREADY(NLW_inst_S_AXI_HP2_AWREADY_UNCONNECTED),
        .S_AXI_HP2_AWSIZE({1'b0,1'b0,1'b0}),
        .S_AXI_HP2_AWVALID(1'b0),
        .S_AXI_HP2_BID(NLW_inst_S_AXI_HP2_BID_UNCONNECTED[5:0]),
        .S_AXI_HP2_BREADY(1'b0),
        .S_AXI_HP2_BRESP(NLW_inst_S_AXI_HP2_BRESP_UNCONNECTED[1:0]),
        .S_AXI_HP2_BVALID(NLW_inst_S_AXI_HP2_BVALID_UNCONNECTED),
        .S_AXI_HP2_RACOUNT(NLW_inst_S_AXI_HP2_RACOUNT_UNCONNECTED[2:0]),
        .S_AXI_HP2_RCOUNT(NLW_inst_S_AXI_HP2_RCOUNT_UNCONNECTED[7:0]),
        .S_AXI_HP2_RDATA(NLW_inst_S_AXI_HP2_RDATA_UNCONNECTED[63:0]),
        .S_AXI_HP2_RDISSUECAP1_EN(1'b0),
        .S_AXI_HP2_RID(NLW_inst_S_AXI_HP2_RID_UNCONNECTED[5:0]),
        .S_AXI_HP2_RLAST(NLW_inst_S_AXI_HP2_RLAST_UNCONNECTED),
        .S_AXI_HP2_RREADY(1'b0),
        .S_AXI_HP2_RRESP(NLW_inst_S_AXI_HP2_RRESP_UNCONNECTED[1:0]),
        .S_AXI_HP2_RVALID(NLW_inst_S_AXI_HP2_RVALID_UNCONNECTED),
        .S_AXI_HP2_WACOUNT(NLW_inst_S_AXI_HP2_WACOUNT_UNCONNECTED[5:0]),
        .S_AXI_HP2_WCOUNT(NLW_inst_S_AXI_HP2_WCOUNT_UNCONNECTED[7:0]),
        .S_AXI_HP2_WDATA({1'b0,1'b0,1'b0,1'b0,1'b0,1'b0,1'b0,1'b0,1'b0,1'b0,1'b0,1'b0,1'b0,1'b0,1'b0,1'b0,1'b0,1'b0,1'b0,1'b0,1'b0,1'b0,1'b0,1'b0,1'b0,1'b0,1'b0,1'b0,1'b0,1'b0,1'b0,1'b0,1'b0,1'b0,1'b0,1'b0,1'b0,1'b0,1'b0,1'b0,1'b0,1'b0,1'b0,1'b0,1'b0,1'b0,1'b0,1'b0,1'b0,1'b0,1'b0,1'b0,1'b0,1'b0,1'b0,1'b0,1'b0,1'b0,1'b0,1'b0,1'b0,1'b0,1'b0,1'b0}),
        .S_AXI_HP2_WID({1'b0,1'b0,1'b0,1'b0,1'b0,1'b0}),
        .S_AXI_HP2_WLAST(1'b0),
        .S_AXI_HP2_WREADY(NLW_inst_S_AXI_HP2_WREADY_UNCONNECTED),
        .S_AXI_HP2_WRISSUECAP1_EN(1'b0),
        .S_AXI_HP2_WSTRB({1'b0,1'b0,1'b0,1'b0,1'b0,1'b0,1'b0,1'b0}),
        .S_AXI_HP2_WVALID(1'b0),
        .S_AXI_HP3_ACLK(1'b0),
        .S_AXI_HP3_ARADDR({1'b0,1'b0,1'b0,1'b0,1'b0,1'b0,1'b0,1'b0,1'b0,1'b0,1'b0,1'b0,1'b0,1'b0,1'b0,1'b0,1'b0,1'b0,1'b0,1'b0,1'b0,1'b0,1'b0,1'b0,1'b0,1'b0,1'b0,1'b0,1'b0,1'b0,1'b0,1'b0}),
        .S_AXI_HP3_ARBURST({1'b0,1'b0}),
        .S_AXI_HP3_ARCACHE({1'b0,1'b0,1'b0,1'b0}),
        .S_AXI_HP3_ARESETN(NLW_inst_S_AXI_HP3_ARESETN_UNCONNECTED),
        .S_AXI_HP3_ARID({1'b0,1'b0,1'b0,1'b0,1'b0,1'b0}),
        .S_AXI_HP3_ARLEN({1'b0,1'b0,1'b0,1'b0}),
        .S_AXI_HP3_ARLOCK({1'b0,1'b0}),
        .S_AXI_HP3_ARPROT({1'b0,1'b0,1'b0}),
        .S_AXI_HP3_ARQOS({1'b0,1'b0,1'b0,1'b0}),
        .S_AXI_HP3_ARREADY(NLW_inst_S_AXI_HP3_ARREADY_UNCONNECTED),
        .S_AXI_HP3_ARSIZE({1'b0,1'b0,1'b0}),
        .S_AXI_HP3_ARVALID(1'b0),
        .S_AXI_HP3_AWADDR({1'b0,1'b0,1'b0,1'b0,1'b0,1'b0,1'b0,1'b0,1'b0,1'b0,1'b0,1'b0,1'b0,1'b0,1'b0,1'b0,1'b0,1'b0,1'b0,1'b0,1'b0,1'b0,1'b0,1'b0,1'b0,1'b0,1'b0,1'b0,1'b0,1'b0,1'b0,1'b0}),
        .S_AXI_HP3_AWBURST({1'b0,1'b0}),
        .S_AXI_HP3_AWCACHE({1'b0,1'b0,1'b0,1'b0}),
        .S_AXI_HP3_AWID({1'b0,1'b0,1'b0,1'b0,1'b0,1'b0}),
        .S_AXI_HP3_AWLEN({1'b0,1'b0,1'b0,1'b0}),
        .S_AXI_HP3_AWLOCK({1'b0,1'b0}),
        .S_AXI_HP3_AWPROT({1'b0,1'b0,1'b0}),
        .S_AXI_HP3_AWQOS({1'b0,1'b0,1'b0,1'b0}),
        .S_AXI_HP3_AWREADY(NLW_inst_S_AXI_HP3_AWREADY_UNCONNECTED),
        .S_AXI_HP3_AWSIZE({1'b0,1'b0,1'b0}),
        .S_AXI_HP3_AWVALID(1'b0),
        .S_AXI_HP3_BID(NLW_inst_S_AXI_HP3_BID_UNCONNECTED[5:0]),
        .S_AXI_HP3_BREADY(1'b0),
        .S_AXI_HP3_BRESP(NLW_inst_S_AXI_HP3_BRESP_UNCONNECTED[1:0]),
        .S_AXI_HP3_BVALID(NLW_inst_S_AXI_HP3_BVALID_UNCONNECTED),
        .S_AXI_HP3_RACOUNT(NLW_inst_S_AXI_HP3_RACOUNT_UNCONNECTED[2:0]),
        .S_AXI_HP3_RCOUNT(NLW_inst_S_AXI_HP3_RCOUNT_UNCONNECTED[7:0]),
        .S_AXI_HP3_RDATA(NLW_inst_S_AXI_HP3_RDATA_UNCONNECTED[63:0]),
        .S_AXI_HP3_RDISSUECAP1_EN(1'b0),
        .S_AXI_HP3_RID(NLW_inst_S_AXI_HP3_RID_UNCONNECTED[5:0]),
        .S_AXI_HP3_RLAST(NLW_inst_S_AXI_HP3_RLAST_UNCONNECTED),
        .S_AXI_HP3_RREADY(1'b0),
        .S_AXI_HP3_RRESP(NLW_inst_S_AXI_HP3_RRESP_UNCONNECTED[1:0]),
        .S_AXI_HP3_RVALID(NLW_inst_S_AXI_HP3_RVALID_UNCONNECTED),
        .S_AXI_HP3_WACOUNT(NLW_inst_S_AXI_HP3_WACOUNT_UNCONNECTED[5:0]),
        .S_AXI_HP3_WCOUNT(NLW_inst_S_AXI_HP3_WCOUNT_UNCONNECTED[7:0]),
        .S_AXI_HP3_WDATA({1'b0,1'b0,1'b0,1'b0,1'b0,1'b0,1'b0,1'b0,1'b0,1'b0,1'b0,1'b0,1'b0,1'b0,1'b0,1'b0,1'b0,1'b0,1'b0,1'b0,1'b0,1'b0,1'b0,1'b0,1'b0,1'b0,1'b0,1'b0,1'b0,1'b0,1'b0,1'b0,1'b0,1'b0,1'b0,1'b0,1'b0,1'b0,1'b0,1'b0,1'b0,1'b0,1'b0,1'b0,1'b0,1'b0,1'b0,1'b0,1'b0,1'b0,1'b0,1'b0,1'b0,1'b0,1'b0,1'b0,1'b0,1'b0,1'b0,1'b0,1'b0,1'b0,1'b0,1'b0}),
        .S_AXI_HP3_WID({1'b0,1'b0,1'b0,1'b0,1'b0,1'b0}),
        .S_AXI_HP3_WLAST(1'b0),
        .S_AXI_HP3_WREADY(NLW_inst_S_AXI_HP3_WREADY_UNCONNECTED),
        .S_AXI_HP3_WRISSUECAP1_EN(1'b0),
        .S_AXI_HP3_WSTRB({1'b0,1'b0,1'b0,1'b0,1'b0,1'b0,1'b0,1'b0}),
        .S_AXI_HP3_WVALID(1'b0),
        .TRACE_CLK(1'b0),
        .TRACE_CLK_OUT(NLW_inst_TRACE_CLK_OUT_UNCONNECTED),
        .TRACE_CTL(NLW_inst_TRACE_CTL_UNCONNECTED),
        .TRACE_DATA(NLW_inst_TRACE_DATA_UNCONNECTED[1:0]),
        .TTC0_CLK0_IN(1'b0),
        .TTC0_CLK1_IN(1'b0),
        .TTC0_CLK2_IN(1'b0),
        .TTC0_WAVE0_OUT(NLW_inst_TTC0_WAVE0_OUT_UNCONNECTED),
        .TTC0_WAVE1_OUT(NLW_inst_TTC0_WAVE1_OUT_UNCONNECTED),
        .TTC0_WAVE2_OUT(NLW_inst_TTC0_WAVE2_OUT_UNCONNECTED),
        .TTC1_CLK0_IN(1'b0),
        .TTC1_CLK1_IN(1'b0),
        .TTC1_CLK2_IN(1'b0),
        .TTC1_WAVE0_OUT(NLW_inst_TTC1_WAVE0_OUT_UNCONNECTED),
        .TTC1_WAVE1_OUT(NLW_inst_TTC1_WAVE1_OUT_UNCONNECTED),
        .TTC1_WAVE2_OUT(NLW_inst_TTC1_WAVE2_OUT_UNCONNECTED),
        .UART0_CTSN(1'b0),
        .UART0_DCDN(1'b0),
        .UART0_DSRN(1'b0),
        .UART0_DTRN(NLW_inst_UART0_DTRN_UNCONNECTED),
        .UART0_RIN(1'b0),
        .UART0_RTSN(NLW_inst_UART0_RTSN_UNCONNECTED),
        .UART0_RX(1'b1),
        .UART0_TX(NLW_inst_UART0_TX_UNCONNECTED),
        .UART1_CTSN(1'b0),
        .UART1_DCDN(1'b0),
        .UART1_DSRN(1'b0),
        .UART1_DTRN(NLW_inst_UART1_DTRN_UNCONNECTED),
        .UART1_RIN(1'b0),
        .UART1_RTSN(NLW_inst_UART1_RTSN_UNCONNECTED),
        .UART1_RX(1'b1),
        .UART1_TX(NLW_inst_UART1_TX_UNCONNECTED),
        .USB0_PORT_INDCTL(NLW_inst_USB0_PORT_INDCTL_UNCONNECTED[1:0]),
        .USB0_VBUS_PWRFAULT(1'b0),
        .USB0_VBUS_PWRSELECT(NLW_inst_USB0_VBUS_PWRSELECT_UNCONNECTED),
        .USB1_PORT_INDCTL(NLW_inst_USB1_PORT_INDCTL_UNCONNECTED[1:0]),
        .USB1_VBUS_PWRFAULT(1'b0),
        .USB1_VBUS_PWRSELECT(NLW_inst_USB1_VBUS_PWRSELECT_UNCONNECTED),
        .WDT_CLK_IN(1'b0),
        .WDT_RST_OUT(NLW_inst_WDT_RST_OUT_UNCONNECTED));
endmodule

(* C_DM_WIDTH = "4" *) (* C_DQS_WIDTH = "4" *) (* C_DQ_WIDTH = "32" *) 
(* C_EMIO_GPIO_WIDTH = "64" *) (* C_EN_EMIO_ENET0 = "0" *) (* C_EN_EMIO_ENET1 = "0" *) 
(* C_EN_EMIO_PJTAG = "0" *) (* C_EN_EMIO_TRACE = "0" *) (* C_FCLK_CLK0_BUF = "TRUE" *) 
(* C_FCLK_CLK1_BUF = "FALSE" *) (* C_FCLK_CLK2_BUF = "FALSE" *) (* C_FCLK_CLK3_BUF = "FALSE" *) 
(* C_GP0_EN_MODIFIABLE_TXN = "1" *) (* C_GP1_EN_MODIFIABLE_TXN = "1" *) (* C_INCLUDE_ACP_TRANS_CHECK = "0" *) 
(* C_INCLUDE_TRACE_BUFFER = "0" *) (* C_IRQ_F2P_MODE = "DIRECT" *) (* C_MIO_PRIMITIVE = "54" *) 
(* C_M_AXI_GP0_ENABLE_STATIC_REMAP = "0" *) (* C_M_AXI_GP0_ID_WIDTH = "12" *) (* C_M_AXI_GP0_THREAD_ID_WIDTH = "12" *) 
(* C_M_AXI_GP1_ENABLE_STATIC_REMAP = "0" *) (* C_M_AXI_GP1_ID_WIDTH = "12" *) (* C_M_AXI_GP1_THREAD_ID_WIDTH = "12" *) 
(* C_NUM_F2P_INTR_INPUTS = "1" *) (* C_PACKAGE_NAME = "clg400" *) (* C_PS7_SI_REV = "PRODUCTION" *) 
(* C_S_AXI_ACP_ARUSER_VAL = "31" *) (* C_S_AXI_ACP_AWUSER_VAL = "31" *) (* C_S_AXI_ACP_ID_WIDTH = "3" *) 
(* C_S_AXI_GP0_ID_WIDTH = "6" *) (* C_S_AXI_GP1_ID_WIDTH = "6" *) (* C_S_AXI_HP0_DATA_WIDTH = "64" *) 
(* C_S_AXI_HP0_ID_WIDTH = "6" *) (* C_S_AXI_HP1_DATA_WIDTH = "64" *) (* C_S_AXI_HP1_ID_WIDTH = "6" *) 
(* C_S_AXI_HP2_DATA_WIDTH = "64" *) (* C_S_AXI_HP2_ID_WIDTH = "6" *) (* C_S_AXI_HP3_DATA_WIDTH = "64" *) 
(* C_S_AXI_HP3_ID_WIDTH = "6" *) (* C_TRACE_BUFFER_CLOCK_DELAY = "12" *) (* C_TRACE_BUFFER_FIFO_SIZE = "128" *) 
(* C_TRACE_INTERNAL_WIDTH = "2" *) (* C_TRACE_PIPELINE_WIDTH = "8" *) (* C_USE_AXI_NONSECURE = "0" *) 
(* C_USE_DEFAULT_ACP_USER_VAL = "0" *) (* C_USE_M_AXI_GP0 = "0" *) (* C_USE_M_AXI_GP1 = "0" *) 
(* C_USE_S_AXI_ACP = "0" *) (* C_USE_S_AXI_GP0 = "0" *) (* C_USE_S_AXI_GP1 = "0" *) 
(* C_USE_S_AXI_HP0 = "0" *) (* C_USE_S_AXI_HP1 = "0" *) (* C_USE_S_AXI_HP2 = "0" *) 
(* C_USE_S_AXI_HP3 = "0" *) (* HW_HANDOFF = "System_processing_system7_0_0.hwdef" *) (* POWER = "<PROCESSOR name={system} numA9Cores={2} clockFreq={666.666666} load={0.5} /><MEMORY name={code} memType={DDR3} dataWidth={16} clockFreq={533.333333} readRate={0.5} writeRate={0.5} /><IO interface={UART} ioStandard={LVCMOS33} bidis={2} ioBank={Vcco_p1} clockFreq={100.000000} usageRate={0.5} /><IO interface={NAND} ioStandard={} bidis={14} ioBank={} clockFreq={100.000000} usageRate={0.5} /><PLL domain={Processor} vco={1333.333} /><PLL domain={Memory} vco={1066.667} /><PLL domain={IO} vco={1600.000} />/>" *) 
(* USE_TRACE_DATA_EDGE_DETECTOR = "0" *) 
module decalper_eb_ot_sdeen_pot_pi_dehcac_xnilix_processing_system7_v5_5_processing_system7
   (CAN0_PHY_TX,
    CAN0_PHY_RX,
    CAN1_PHY_TX,
    CAN1_PHY_RX,
    ENET0_GMII_TX_EN,
    ENET0_GMII_TX_ER,
    ENET0_MDIO_MDC,
    ENET0_MDIO_O,
    ENET0_MDIO_T,
    ENET0_PTP_DELAY_REQ_RX,
    ENET0_PTP_DELAY_REQ_TX,
    ENET0_PTP_PDELAY_REQ_RX,
    ENET0_PTP_PDELAY_REQ_TX,
    ENET0_PTP_PDELAY_RESP_RX,
    ENET0_PTP_PDELAY_RESP_TX,
    ENET0_PTP_SYNC_FRAME_RX,
    ENET0_PTP_SYNC_FRAME_TX,
    ENET0_SOF_RX,
    ENET0_SOF_TX,
    ENET0_GMII_TXD,
    ENET0_GMII_COL,
    ENET0_GMII_CRS,
    ENET0_GMII_RX_CLK,
    ENET0_GMII_RX_DV,
    ENET0_GMII_RX_ER,
    ENET0_GMII_TX_CLK,
    ENET0_MDIO_I,
    ENET0_EXT_INTIN,
    ENET0_GMII_RXD,
    ENET1_GMII_TX_EN,
    ENET1_GMII_TX_ER,
    ENET1_MDIO_MDC,
    ENET1_MDIO_O,
    ENET1_MDIO_T,
    ENET1_PTP_DELAY_REQ_RX,
    ENET1_PTP_DELAY_REQ_TX,
    ENET1_PTP_PDELAY_REQ_RX,
    ENET1_PTP_PDELAY_REQ_TX,
    ENET1_PTP_PDELAY_RESP_RX,
    ENET1_PTP_PDELAY_RESP_TX,
    ENET1_PTP_SYNC_FRAME_RX,
    ENET1_PTP_SYNC_FRAME_TX,
    ENET1_SOF_RX,
    ENET1_SOF_TX,
    ENET1_GMII_TXD,
    ENET1_GMII_COL,
    ENET1_GMII_CRS,
    ENET1_GMII_RX_CLK,
    ENET1_GMII_RX_DV,
    ENET1_GMII_RX_ER,
    ENET1_GMII_TX_CLK,
    ENET1_MDIO_I,
    ENET1_EXT_INTIN,
    ENET1_GMII_RXD,
    GPIO_I,
    GPIO_O,
    GPIO_T,
    I2C0_SDA_I,
    I2C0_SDA_O,
    I2C0_SDA_T,
    I2C0_SCL_I,
    I2C0_SCL_O,
    I2C0_SCL_T,
    I2C1_SDA_I,
    I2C1_SDA_O,
    I2C1_SDA_T,
    I2C1_SCL_I,
    I2C1_SCL_O,
    I2C1_SCL_T,
    PJTAG_TCK,
    PJTAG_TMS,
    PJTAG_TDI,
    PJTAG_TDO,
    SDIO0_CLK,
    SDIO0_CLK_FB,
    SDIO0_CMD_O,
    SDIO0_CMD_I,
    SDIO0_CMD_T,
    SDIO0_DATA_I,
    SDIO0_DATA_O,
    SDIO0_DATA_T,
    SDIO0_LED,
    SDIO0_CDN,
    SDIO0_WP,
    SDIO0_BUSPOW,
    SDIO0_BUSVOLT,
    SDIO1_CLK,
    SDIO1_CLK_FB,
    SDIO1_CMD_O,
    SDIO1_CMD_I,
    SDIO1_CMD_T,
    SDIO1_DATA_I,
    SDIO1_DATA_O,
    SDIO1_DATA_T,
    SDIO1_LED,
    SDIO1_CDN,
    SDIO1_WP,
    SDIO1_BUSPOW,
    SDIO1_BUSVOLT,
    SPI0_SCLK_I,
    SPI0_SCLK_O,
    SPI0_SCLK_T,
    SPI0_MOSI_I,
    SPI0_MOSI_O,
    SPI0_MOSI_T,
    SPI0_MISO_I,
    SPI0_MISO_O,
    SPI0_MISO_T,
    SPI0_SS_I,
    SPI0_SS_O,
    SPI0_SS1_O,
    SPI0_SS2_O,
    SPI0_SS_T,
    SPI1_SCLK_I,
    SPI1_SCLK_O,
    SPI1_SCLK_T,
    SPI1_MOSI_I,
    SPI1_MOSI_O,
    SPI1_MOSI_T,
    SPI1_MISO_I,
    SPI1_MISO_O,
    SPI1_MISO_T,
    SPI1_SS_I,
    SPI1_SS_O,
    SPI1_SS1_O,
    SPI1_SS2_O,
    SPI1_SS_T,
    UART0_DTRN,
    UART0_RTSN,
    UART0_TX,
    UART0_CTSN,
    UART0_DCDN,
    UART0_DSRN,
    UART0_RIN,
    UART0_RX,
    UART1_DTRN,
    UART1_RTSN,
    UART1_TX,
    UART1_CTSN,
    UART1_DCDN,
    UART1_DSRN,
    UART1_RIN,
    UART1_RX,
    TTC0_WAVE0_OUT,
    TTC0_WAVE1_OUT,
    TTC0_WAVE2_OUT,
    TTC0_CLK0_IN,
    TTC0_CLK1_IN,
    TTC0_CLK2_IN,
    TTC1_WAVE0_OUT,
    TTC1_WAVE1_OUT,
    TTC1_WAVE2_OUT,
    TTC1_CLK0_IN,
    TTC1_CLK1_IN,
    TTC1_CLK2_IN,
    WDT_CLK_IN,
    WDT_RST_OUT,
    TRACE_CLK,
    TRACE_CTL,
    TRACE_DATA,
    TRACE_CLK_OUT,
    USB0_PORT_INDCTL,
    USB0_VBUS_PWRSELECT,
    USB0_VBUS_PWRFAULT,
    USB1_PORT_INDCTL,
    USB1_VBUS_PWRSELECT,
    USB1_VBUS_PWRFAULT,
    SRAM_INTIN,
    M_AXI_GP0_ARESETN,
    M_AXI_GP0_ARVALID,
    M_AXI_GP0_AWVALID,
    M_AXI_GP0_BREADY,
    M_AXI_GP0_RREADY,
    M_AXI_GP0_WLAST,
    M_AXI_GP0_WVALID,
    M_AXI_GP0_ARID,
    M_AXI_GP0_AWID,
    M_AXI_GP0_WID,
    M_AXI_GP0_ARBURST,
    M_AXI_GP0_ARLOCK,
    M_AXI_GP0_ARSIZE,
    M_AXI_GP0_AWBURST,
    M_AXI_GP0_AWLOCK,
    M_AXI_GP0_AWSIZE,
    M_AXI_GP0_ARPROT,
    M_AXI_GP0_AWPROT,
    M_AXI_GP0_ARADDR,
    M_AXI_GP0_AWADDR,
    M_AXI_GP0_WDATA,
    M_AXI_GP0_ARCACHE,
    M_AXI_GP0_ARLEN,
    M_AXI_GP0_ARQOS,
    M_AXI_GP0_AWCACHE,
    M_AXI_GP0_AWLEN,
    M_AXI_GP0_AWQOS,
    M_AXI_GP0_WSTRB,
    M_AXI_GP0_ACLK,
    M_AXI_GP0_ARREADY,
    M_AXI_GP0_AWREADY,
    M_AXI_GP0_BVALID,
    M_AXI_GP0_RLAST,
    M_AXI_GP0_RVALID,
    M_AXI_GP0_WREADY,
    M_AXI_GP0_BID,
    M_AXI_GP0_RID,
    M_AXI_GP0_BRESP,
    M_AXI_GP0_RRESP,
    M_AXI_GP0_RDATA,
    M_AXI_GP1_ARESETN,
    M_AXI_GP1_ARVALID,
    M_AXI_GP1_AWVALID,
    M_AXI_GP1_BREADY,
    M_AXI_GP1_RREADY,
    M_AXI_GP1_WLAST,
    M_AXI_GP1_WVALID,
    M_AXI_GP1_ARID,
    M_AXI_GP1_AWID,
    M_AXI_GP1_WID,
    M_AXI_GP1_ARBURST,
    M_AXI_GP1_ARLOCK,
    M_AXI_GP1_ARSIZE,
    M_AXI_GP1_AWBURST,
    M_AXI_GP1_AWLOCK,
    M_AXI_GP1_AWSIZE,
    M_AXI_GP1_ARPROT,
    M_AXI_GP1_AWPROT,
    M_AXI_GP1_ARADDR,
    M_AXI_GP1_AWADDR,
    M_AXI_GP1_WDATA,
    M_AXI_GP1_ARCACHE,
    M_AXI_GP1_ARLEN,
    M_AXI_GP1_ARQOS,
    M_AXI_GP1_AWCACHE,
    M_AXI_GP1_AWLEN,
    M_AXI_GP1_AWQOS,
    M_AXI_GP1_WSTRB,
    M_AXI_GP1_ACLK,
    M_AXI_GP1_ARREADY,
    M_AXI_GP1_AWREADY,
    M_AXI_GP1_BVALID,
    M_AXI_GP1_RLAST,
    M_AXI_GP1_RVALID,
    M_AXI_GP1_WREADY,
    M_AXI_GP1_BID,
    M_AXI_GP1_RID,
    M_AXI_GP1_BRESP,
    M_AXI_GP1_RRESP,
    M_AXI_GP1_RDATA,
    S_AXI_GP0_ARESETN,
    S_AXI_GP0_ARREADY,
    S_AXI_GP0_AWREADY,
    S_AXI_GP0_BVALID,
    S_AXI_GP0_RLAST,
    S_AXI_GP0_RVALID,
    S_AXI_GP0_WREADY,
    S_AXI_GP0_BRESP,
    S_AXI_GP0_RRESP,
    S_AXI_GP0_RDATA,
    S_AXI_GP0_BID,
    S_AXI_GP0_RID,
    S_AXI_GP0_ACLK,
    S_AXI_GP0_ARVALID,
    S_AXI_GP0_AWVALID,
    S_AXI_GP0_BREADY,
    S_AXI_GP0_RREADY,
    S_AXI_GP0_WLAST,
    S_AXI_GP0_WVALID,
    S_AXI_GP0_ARBURST,
    S_AXI_GP0_ARLOCK,
    S_AXI_GP0_ARSIZE,
    S_AXI_GP0_AWBURST,
    S_AXI_GP0_AWLOCK,
    S_AXI_GP0_AWSIZE,
    S_AXI_GP0_ARPROT,
    S_AXI_GP0_AWPROT,
    S_AXI_GP0_ARADDR,
    S_AXI_GP0_AWADDR,
    S_AXI_GP0_WDATA,
    S_AXI_GP0_ARCACHE,
    S_AXI_GP0_ARLEN,
    S_AXI_GP0_ARQOS,
    S_AXI_GP0_AWCACHE,
    S_AXI_GP0_AWLEN,
    S_AXI_GP0_AWQOS,
    S_AXI_GP0_WSTRB,
    S_AXI_GP0_ARID,
    S_AXI_GP0_AWID,
    S_AXI_GP0_WID,
    S_AXI_GP1_ARESETN,
    S_AXI_GP1_ARREADY,
    S_AXI_GP1_AWREADY,
    S_AXI_GP1_BVALID,
    S_AXI_GP1_RLAST,
    S_AXI_GP1_RVALID,
    S_AXI_GP1_WREADY,
    S_AXI_GP1_BRESP,
    S_AXI_GP1_RRESP,
    S_AXI_GP1_RDATA,
    S_AXI_GP1_BID,
    S_AXI_GP1_RID,
    S_AXI_GP1_ACLK,
    S_AXI_GP1_ARVALID,
    S_AXI_GP1_AWVALID,
    S_AXI_GP1_BREADY,
    S_AXI_GP1_RREADY,
    S_AXI_GP1_WLAST,
    S_AXI_GP1_WVALID,
    S_AXI_GP1_ARBURST,
    S_AXI_GP1_ARLOCK,
    S_AXI_GP1_ARSIZE,
    S_AXI_GP1_AWBURST,
    S_AXI_GP1_AWLOCK,
    S_AXI_GP1_AWSIZE,
    S_AXI_GP1_ARPROT,
    S_AXI_GP1_AWPROT,
    S_AXI_GP1_ARADDR,
    S_AXI_GP1_AWADDR,
    S_AXI_GP1_WDATA,
    S_AXI_GP1_ARCACHE,
    S_AXI_GP1_ARLEN,
    S_AXI_GP1_ARQOS,
    S_AXI_GP1_AWCACHE,
    S_AXI_GP1_AWLEN,
    S_AXI_GP1_AWQOS,
    S_AXI_GP1_WSTRB,
    S_AXI_GP1_ARID,
    S_AXI_GP1_AWID,
    S_AXI_GP1_WID,
    S_AXI_ACP_ARESETN,
    S_AXI_ACP_ARREADY,
    S_AXI_ACP_AWREADY,
    S_AXI_ACP_BVALID,
    S_AXI_ACP_RLAST,
    S_AXI_ACP_RVALID,
    S_AXI_ACP_WREADY,
    S_AXI_ACP_BRESP,
    S_AXI_ACP_RRESP,
    S_AXI_ACP_BID,
    S_AXI_ACP_RID,
    S_AXI_ACP_RDATA,
    S_AXI_ACP_ACLK,
    S_AXI_ACP_ARVALID,
    S_AXI_ACP_AWVALID,
    S_AXI_ACP_BREADY,
    S_AXI_ACP_RREADY,
    S_AXI_ACP_WLAST,
    S_AXI_ACP_WVALID,
    S_AXI_ACP_ARID,
    S_AXI_ACP_ARPROT,
    S_AXI_ACP_AWID,
    S_AXI_ACP_AWPROT,
    S_AXI_ACP_WID,
    S_AXI_ACP_ARADDR,
    S_AXI_ACP_AWADDR,
    S_AXI_ACP_ARCACHE,
    S_AXI_ACP_ARLEN,
    S_AXI_ACP_ARQOS,
    S_AXI_ACP_AWCACHE,
    S_AXI_ACP_AWLEN,
    S_AXI_ACP_AWQOS,
    S_AXI_ACP_ARBURST,
    S_AXI_ACP_ARLOCK,
    S_AXI_ACP_ARSIZE,
    S_AXI_ACP_AWBURST,
    S_AXI_ACP_AWLOCK,
    S_AXI_ACP_AWSIZE,
    S_AXI_ACP_ARUSER,
    S_AXI_ACP_AWUSER,
    S_AXI_ACP_WDATA,
    S_AXI_ACP_WSTRB,
    S_AXI_HP0_ARESETN,
    S_AXI_HP0_ARREADY,
    S_AXI_HP0_AWREADY,
    S_AXI_HP0_BVALID,
    S_AXI_HP0_RLAST,
    S_AXI_HP0_RVALID,
    S_AXI_HP0_WREADY,
    S_AXI_HP0_BRESP,
    S_AXI_HP0_RRESP,
    S_AXI_HP0_BID,
    S_AXI_HP0_RID,
    S_AXI_HP0_RDATA,
    S_AXI_HP0_RCOUNT,
    S_AXI_HP0_WCOUNT,
    S_AXI_HP0_RACOUNT,
    S_AXI_HP0_WACOUNT,
    S_AXI_HP0_ACLK,
    S_AXI_HP0_ARVALID,
    S_AXI_HP0_AWVALID,
    S_AXI_HP0_BREADY,
    S_AXI_HP0_RDISSUECAP1_EN,
    S_AXI_HP0_RREADY,
    S_AXI_HP0_WLAST,
    S_AXI_HP0_WRISSUECAP1_EN,
    S_AXI_HP0_WVALID,
    S_AXI_HP0_ARBURST,
    S_AXI_HP0_ARLOCK,
    S_AXI_HP0_ARSIZE,
    S_AXI_HP0_AWBURST,
    S_AXI_HP0_AWLOCK,
    S_AXI_HP0_AWSIZE,
    S_AXI_HP0_ARPROT,
    S_AXI_HP0_AWPROT,
    S_AXI_HP0_ARADDR,
    S_AXI_HP0_AWADDR,
    S_AXI_HP0_ARCACHE,
    S_AXI_HP0_ARLEN,
    S_AXI_HP0_ARQOS,
    S_AXI_HP0_AWCACHE,
    S_AXI_HP0_AWLEN,
    S_AXI_HP0_AWQOS,
    S_AXI_HP0_ARID,
    S_AXI_HP0_AWID,
    S_AXI_HP0_WID,
    S_AXI_HP0_WDATA,
    S_AXI_HP0_WSTRB,
    S_AXI_HP1_ARESETN,
    S_AXI_HP1_ARREADY,
    S_AXI_HP1_AWREADY,
    S_AXI_HP1_BVALID,
    S_AXI_HP1_RLAST,
    S_AXI_HP1_RVALID,
    S_AXI_HP1_WREADY,
    S_AXI_HP1_BRESP,
    S_AXI_HP1_RRESP,
    S_AXI_HP1_BID,
    S_AXI_HP1_RID,
    S_AXI_HP1_RDATA,
    S_AXI_HP1_RCOUNT,
    S_AXI_HP1_WCOUNT,
    S_AXI_HP1_RACOUNT,
    S_AXI_HP1_WACOUNT,
    S_AXI_HP1_ACLK,
    S_AXI_HP1_ARVALID,
    S_AXI_HP1_AWVALID,
    S_AXI_HP1_BREADY,
    S_AXI_HP1_RDISSUECAP1_EN,
    S_AXI_HP1_RREADY,
    S_AXI_HP1_WLAST,
    S_AXI_HP1_WRISSUECAP1_EN,
    S_AXI_HP1_WVALID,
    S_AXI_HP1_ARBURST,
    S_AXI_HP1_ARLOCK,
    S_AXI_HP1_ARSIZE,
    S_AXI_HP1_AWBURST,
    S_AXI_HP1_AWLOCK,
    S_AXI_HP1_AWSIZE,
    S_AXI_HP1_ARPROT,
    S_AXI_HP1_AWPROT,
    S_AXI_HP1_ARADDR,
    S_AXI_HP1_AWADDR,
    S_AXI_HP1_ARCACHE,
    S_AXI_HP1_ARLEN,
    S_AXI_HP1_ARQOS,
    S_AXI_HP1_AWCACHE,
    S_AXI_HP1_AWLEN,
    S_AXI_HP1_AWQOS,
    S_AXI_HP1_ARID,
    S_AXI_HP1_AWID,
    S_AXI_HP1_WID,
    S_AXI_HP1_WDATA,
    S_AXI_HP1_WSTRB,
    S_AXI_HP2_ARESETN,
    S_AXI_HP2_ARREADY,
    S_AXI_HP2_AWREADY,
    S_AXI_HP2_BVALID,
    S_AXI_HP2_RLAST,
    S_AXI_HP2_RVALID,
    S_AXI_HP2_WREADY,
    S_AXI_HP2_BRESP,
    S_AXI_HP2_RRESP,
    S_AXI_HP2_BID,
    S_AXI_HP2_RID,
    S_AXI_HP2_RDATA,
    S_AXI_HP2_RCOUNT,
    S_AXI_HP2_WCOUNT,
    S_AXI_HP2_RACOUNT,
    S_AXI_HP2_WACOUNT,
    S_AXI_HP2_ACLK,
    S_AXI_HP2_ARVALID,
    S_AXI_HP2_AWVALID,
    S_AXI_HP2_BREADY,
    S_AXI_HP2_RDISSUECAP1_EN,
    S_AXI_HP2_RREADY,
    S_AXI_HP2_WLAST,
    S_AXI_HP2_WRISSUECAP1_EN,
    S_AXI_HP2_WVALID,
    S_AXI_HP2_ARBURST,
    S_AXI_HP2_ARLOCK,
    S_AXI_HP2_ARSIZE,
    S_AXI_HP2_AWBURST,
    S_AXI_HP2_AWLOCK,
    S_AXI_HP2_AWSIZE,
    S_AXI_HP2_ARPROT,
    S_AXI_HP2_AWPROT,
    S_AXI_HP2_ARADDR,
    S_AXI_HP2_AWADDR,
    S_AXI_HP2_ARCACHE,
    S_AXI_HP2_ARLEN,
    S_AXI_HP2_ARQOS,
    S_AXI_HP2_AWCACHE,
    S_AXI_HP2_AWLEN,
    S_AXI_HP2_AWQOS,
    S_AXI_HP2_ARID,
    S_AXI_HP2_AWID,
    S_AXI_HP2_WID,
    S_AXI_HP2_WDATA,
    S_AXI_HP2_WSTRB,
    S_AXI_HP3_ARESETN,
    S_AXI_HP3_ARREADY,
    S_AXI_HP3_AWREADY,
    S_AXI_HP3_BVALID,
    S_AXI_HP3_RLAST,
    S_AXI_HP3_RVALID,
    S_AXI_HP3_WREADY,
    S_AXI_HP3_BRESP,
    S_AXI_HP3_RRESP,
    S_AXI_HP3_BID,
    S_AXI_HP3_RID,
    S_AXI_HP3_RDATA,
    S_AXI_HP3_RCOUNT,
    S_AXI_HP3_WCOUNT,
    S_AXI_HP3_RACOUNT,
    S_AXI_HP3_WACOUNT,
    S_AXI_HP3_ACLK,
    S_AXI_HP3_ARVALID,
    S_AXI_HP3_AWVALID,
    S_AXI_HP3_BREADY,
    S_AXI_HP3_RDISSUECAP1_EN,
    S_AXI_HP3_RREADY,
    S_AXI_HP3_WLAST,
    S_AXI_HP3_WRISSUECAP1_EN,
    S_AXI_HP3_WVALID,
    S_AXI_HP3_ARBURST,
    S_AXI_HP3_ARLOCK,
    S_AXI_HP3_ARSIZE,
    S_AXI_HP3_AWBURST,
    S_AXI_HP3_AWLOCK,
    S_AXI_HP3_AWSIZE,
    S_AXI_HP3_ARPROT,
    S_AXI_HP3_AWPROT,
    S_AXI_HP3_ARADDR,
    S_AXI_HP3_AWADDR,
    S_AXI_HP3_ARCACHE,
    S_AXI_HP3_ARLEN,
    S_AXI_HP3_ARQOS,
    S_AXI_HP3_AWCACHE,
    S_AXI_HP3_AWLEN,
    S_AXI_HP3_AWQOS,
    S_AXI_HP3_ARID,
    S_AXI_HP3_AWID,
    S_AXI_HP3_WID,
    S_AXI_HP3_WDATA,
    S_AXI_HP3_WSTRB,
    IRQ_P2F_DMAC_ABORT,
    IRQ_P2F_DMAC0,
    IRQ_P2F_DMAC1,
    IRQ_P2F_DMAC2,
    IRQ_P2F_DMAC3,
    IRQ_P2F_DMAC4,
    IRQ_P2F_DMAC5,
    IRQ_P2F_DMAC6,
    IRQ_P2F_DMAC7,
    IRQ_P2F_SMC,
    IRQ_P2F_QSPI,
    IRQ_P2F_CTI,
    IRQ_P2F_GPIO,
    IRQ_P2F_USB0,
    IRQ_P2F_ENET0,
    IRQ_P2F_ENET_WAKE0,
    IRQ_P2F_SDIO0,
    IRQ_P2F_I2C0,
    IRQ_P2F_SPI0,
    IRQ_P2F_UART0,
    IRQ_P2F_CAN0,
    IRQ_P2F_USB1,
    IRQ_P2F_ENET1,
    IRQ_P2F_ENET_WAKE1,
    IRQ_P2F_SDIO1,
    IRQ_P2F_I2C1,
    IRQ_P2F_SPI1,
    IRQ_P2F_UART1,
    IRQ_P2F_CAN1,
    IRQ_F2P,
    Core0_nFIQ,
    Core0_nIRQ,
    Core1_nFIQ,
    Core1_nIRQ,
    DMA0_DATYPE,
    DMA0_DAVALID,
    DMA0_DRREADY,
    DMA0_RSTN,
    DMA1_DATYPE,
    DMA1_DAVALID,
    DMA1_DRREADY,
    DMA1_RSTN,
    DMA2_DATYPE,
    DMA2_DAVALID,
    DMA2_DRREADY,
    DMA2_RSTN,
    DMA3_DATYPE,
    DMA3_DAVALID,
    DMA3_DRREADY,
    DMA3_RSTN,
    DMA0_ACLK,
    DMA0_DAREADY,
    DMA0_DRLAST,
    DMA0_DRVALID,
    DMA1_ACLK,
    DMA1_DAREADY,
    DMA1_DRLAST,
    DMA1_DRVALID,
    DMA2_ACLK,
    DMA2_DAREADY,
    DMA2_DRLAST,
    DMA2_DRVALID,
    DMA3_ACLK,
    DMA3_DAREADY,
    DMA3_DRLAST,
    DMA3_DRVALID,
    DMA0_DRTYPE,
    DMA1_DRTYPE,
    DMA2_DRTYPE,
    DMA3_DRTYPE,
    FCLK_CLK3,
    FCLK_CLK2,
    FCLK_CLK1,
    FCLK_CLK0,
    FCLK_CLKTRIG3_N,
    FCLK_CLKTRIG2_N,
    FCLK_CLKTRIG1_N,
    FCLK_CLKTRIG0_N,
    FCLK_RESET3_N,
    FCLK_RESET2_N,
    FCLK_RESET1_N,
    FCLK_RESET0_N,
    FTMD_TRACEIN_DATA,
    FTMD_TRACEIN_VALID,
    FTMD_TRACEIN_CLK,
    FTMD_TRACEIN_ATID,
    FTMT_F2P_TRIG_0,
    FTMT_F2P_TRIGACK_0,
    FTMT_F2P_TRIG_1,
    FTMT_F2P_TRIGACK_1,
    FTMT_F2P_TRIG_2,
    FTMT_F2P_TRIGACK_2,
    FTMT_F2P_TRIG_3,
    FTMT_F2P_TRIGACK_3,
    FTMT_F2P_DEBUG,
    FTMT_P2F_TRIGACK_0,
    FTMT_P2F_TRIG_0,
    FTMT_P2F_TRIGACK_1,
    FTMT_P2F_TRIG_1,
    FTMT_P2F_TRIGACK_2,
    FTMT_P2F_TRIG_2,
    FTMT_P2F_TRIGACK_3,
    FTMT_P2F_TRIG_3,
    FTMT_P2F_DEBUG,
    FPGA_IDLE_N,
    EVENT_EVENTO,
    EVENT_STANDBYWFE,
    EVENT_STANDBYWFI,
    EVENT_EVENTI,
    DDR_ARB,
    MIO,
    DDR_CAS_n,
    DDR_CKE,
    DDR_Clk_n,
    DDR_Clk,
    DDR_CS_n,
    DDR_DRSTB,
    DDR_ODT,
    DDR_RAS_n,
    DDR_WEB,
    DDR_BankAddr,
    DDR_Addr,
    DDR_VRN,
    DDR_VRP,
    DDR_DM,
    DDR_DQ,
    DDR_DQS_n,
    DDR_DQS,
    PS_SRSTB,
    PS_CLK,
    PS_PORB);
  output CAN0_PHY_TX;
  input CAN0_PHY_RX;
  output CAN1_PHY_TX;
  input CAN1_PHY_RX;
  output ENET0_GMII_TX_EN;
  output ENET0_GMII_TX_ER;
  output ENET0_MDIO_MDC;
  output ENET0_MDIO_O;
  output ENET0_MDIO_T;
  output ENET0_PTP_DELAY_REQ_RX;
  output ENET0_PTP_DELAY_REQ_TX;
  output ENET0_PTP_PDELAY_REQ_RX;
  output ENET0_PTP_PDELAY_REQ_TX;
  output ENET0_PTP_PDELAY_RESP_RX;
  output ENET0_PTP_PDELAY_RESP_TX;
  output ENET0_PTP_SYNC_FRAME_RX;
  output ENET0_PTP_SYNC_FRAME_TX;
  output ENET0_SOF_RX;
  output ENET0_SOF_TX;
  output [7:0]ENET0_GMII_TXD;
  input ENET0_GMII_COL;
  input ENET0_GMII_CRS;
  input ENET0_GMII_RX_CLK;
  input ENET0_GMII_RX_DV;
  input ENET0_GMII_RX_ER;
  input ENET0_GMII_TX_CLK;
  input ENET0_MDIO_I;
  input ENET0_EXT_INTIN;
  input [7:0]ENET0_GMII_RXD;
  output ENET1_GMII_TX_EN;
  output ENET1_GMII_TX_ER;
  output ENET1_MDIO_MDC;
  output ENET1_MDIO_O;
  output ENET1_MDIO_T;
  output ENET1_PTP_DELAY_REQ_RX;
  output ENET1_PTP_DELAY_REQ_TX;
  output ENET1_PTP_PDELAY_REQ_RX;
  output ENET1_PTP_PDELAY_REQ_TX;
  output ENET1_PTP_PDELAY_RESP_RX;
  output ENET1_PTP_PDELAY_RESP_TX;
  output ENET1_PTP_SYNC_FRAME_RX;
  output ENET1_PTP_SYNC_FRAME_TX;
  output ENET1_SOF_RX;
  output ENET1_SOF_TX;
  output [7:0]ENET1_GMII_TXD;
  input ENET1_GMII_COL;
  input ENET1_GMII_CRS;
  input ENET1_GMII_RX_CLK;
  input ENET1_GMII_RX_DV;
  input ENET1_GMII_RX_ER;
  input ENET1_GMII_TX_CLK;
  input ENET1_MDIO_I;
  input ENET1_EXT_INTIN;
  input [7:0]ENET1_GMII_RXD;
  input [63:0]GPIO_I;
  output [63:0]GPIO_O;
  output [63:0]GPIO_T;
  input I2C0_SDA_I;
  output I2C0_SDA_O;
  output I2C0_SDA_T;
  input I2C0_SCL_I;
  output I2C0_SCL_O;
  output I2C0_SCL_T;
  input I2C1_SDA_I;
  output I2C1_SDA_O;
  output I2C1_SDA_T;
  input I2C1_SCL_I;
  output I2C1_SCL_O;
  output I2C1_SCL_T;
  input PJTAG_TCK;
  input PJTAG_TMS;
  input PJTAG_TDI;
  output PJTAG_TDO;
  output SDIO0_CLK;
  input SDIO0_CLK_FB;
  output SDIO0_CMD_O;
  input SDIO0_CMD_I;
  output SDIO0_CMD_T;
  input [3:0]SDIO0_DATA_I;
  output [3:0]SDIO0_DATA_O;
  output [3:0]SDIO0_DATA_T;
  output SDIO0_LED;
  input SDIO0_CDN;
  input SDIO0_WP;
  output SDIO0_BUSPOW;
  output [2:0]SDIO0_BUSVOLT;
  output SDIO1_CLK;
  input SDIO1_CLK_FB;
  output SDIO1_CMD_O;
  input SDIO1_CMD_I;
  output SDIO1_CMD_T;
  input [3:0]SDIO1_DATA_I;
  output [3:0]SDIO1_DATA_O;
  output [3:0]SDIO1_DATA_T;
  output SDIO1_LED;
  input SDIO1_CDN;
  input SDIO1_WP;
  output SDIO1_BUSPOW;
  output [2:0]SDIO1_BUSVOLT;
  input SPI0_SCLK_I;
  output SPI0_SCLK_O;
  output SPI0_SCLK_T;
  input SPI0_MOSI_I;
  output SPI0_MOSI_O;
  output SPI0_MOSI_T;
  input SPI0_MISO_I;
  output SPI0_MISO_O;
  output SPI0_MISO_T;
  input SPI0_SS_I;
  output SPI0_SS_O;
  output SPI0_SS1_O;
  output SPI0_SS2_O;
  output SPI0_SS_T;
  input SPI1_SCLK_I;
  output SPI1_SCLK_O;
  output SPI1_SCLK_T;
  input SPI1_MOSI_I;
  output SPI1_MOSI_O;
  output SPI1_MOSI_T;
  input SPI1_MISO_I;
  output SPI1_MISO_O;
  output SPI1_MISO_T;
  input SPI1_SS_I;
  output SPI1_SS_O;
  output SPI1_SS1_O;
  output SPI1_SS2_O;
  output SPI1_SS_T;
  output UART0_DTRN;
  output UART0_RTSN;
  output UART0_TX;
  input UART0_CTSN;
  input UART0_DCDN;
  input UART0_DSRN;
  input UART0_RIN;
  input UART0_RX;
  output UART1_DTRN;
  output UART1_RTSN;
  output UART1_TX;
  input UART1_CTSN;
  input UART1_DCDN;
  input UART1_DSRN;
  input UART1_RIN;
  input UART1_RX;
  output TTC0_WAVE0_OUT;
  output TTC0_WAVE1_OUT;
  output TTC0_WAVE2_OUT;
  input TTC0_CLK0_IN;
  input TTC0_CLK1_IN;
  input TTC0_CLK2_IN;
  output TTC1_WAVE0_OUT;
  output TTC1_WAVE1_OUT;
  output TTC1_WAVE2_OUT;
  input TTC1_CLK0_IN;
  input TTC1_CLK1_IN;
  input TTC1_CLK2_IN;
  input WDT_CLK_IN;
  output WDT_RST_OUT;
  input TRACE_CLK;
  output TRACE_CTL;
  output [1:0]TRACE_DATA;
  output TRACE_CLK_OUT;
  output [1:0]USB0_PORT_INDCTL;
  output USB0_VBUS_PWRSELECT;
  input USB0_VBUS_PWRFAULT;
  output [1:0]USB1_PORT_INDCTL;
  output USB1_VBUS_PWRSELECT;
  input USB1_VBUS_PWRFAULT;
  input SRAM_INTIN;
  output M_AXI_GP0_ARESETN;
  output M_AXI_GP0_ARVALID;
  output M_AXI_GP0_AWVALID;
  output M_AXI_GP0_BREADY;
  output M_AXI_GP0_RREADY;
  output M_AXI_GP0_WLAST;
  output M_AXI_GP0_WVALID;
  output [11:0]M_AXI_GP0_ARID;
  output [11:0]M_AXI_GP0_AWID;
  output [11:0]M_AXI_GP0_WID;
  output [1:0]M_AXI_GP0_ARBURST;
  output [1:0]M_AXI_GP0_ARLOCK;
  output [2:0]M_AXI_GP0_ARSIZE;
  output [1:0]M_AXI_GP0_AWBURST;
  output [1:0]M_AXI_GP0_AWLOCK;
  output [2:0]M_AXI_GP0_AWSIZE;
  output [2:0]M_AXI_GP0_ARPROT;
  output [2:0]M_AXI_GP0_AWPROT;
  output [31:0]M_AXI_GP0_ARADDR;
  output [31:0]M_AXI_GP0_AWADDR;
  output [31:0]M_AXI_GP0_WDATA;
  output [3:0]M_AXI_GP0_ARCACHE;
  output [3:0]M_AXI_GP0_ARLEN;
  output [3:0]M_AXI_GP0_ARQOS;
  output [3:0]M_AXI_GP0_AWCACHE;
  output [3:0]M_AXI_GP0_AWLEN;
  output [3:0]M_AXI_GP0_AWQOS;
  output [3:0]M_AXI_GP0_WSTRB;
  input M_AXI_GP0_ACLK;
  input M_AXI_GP0_ARREADY;
  input M_AXI_GP0_AWREADY;
  input M_AXI_GP0_BVALID;
  input M_AXI_GP0_RLAST;
  input M_AXI_GP0_RVALID;
  input M_AXI_GP0_WREADY;
  input [11:0]M_AXI_GP0_BID;
  input [11:0]M_AXI_GP0_RID;
  input [1:0]M_AXI_GP0_BRESP;
  input [1:0]M_AXI_GP0_RRESP;
  input [31:0]M_AXI_GP0_RDATA;
  output M_AXI_GP1_ARESETN;
  output M_AXI_GP1_ARVALID;
  output M_AXI_GP1_AWVALID;
  output M_AXI_GP1_BREADY;
  output M_AXI_GP1_RREADY;
  output M_AXI_GP1_WLAST;
  output M_AXI_GP1_WVALID;
  output [11:0]M_AXI_GP1_ARID;
  output [11:0]M_AXI_GP1_AWID;
  output [11:0]M_AXI_GP1_WID;
  output [1:0]M_AXI_GP1_ARBURST;
  output [1:0]M_AXI_GP1_ARLOCK;
  output [2:0]M_AXI_GP1_ARSIZE;
  output [1:0]M_AXI_GP1_AWBURST;
  output [1:0]M_AXI_GP1_AWLOCK;
  output [2:0]M_AXI_GP1_AWSIZE;
  output [2:0]M_AXI_GP1_ARPROT;
  output [2:0]M_AXI_GP1_AWPROT;
  output [31:0]M_AXI_GP1_ARADDR;
  output [31:0]M_AXI_GP1_AWADDR;
  output [31:0]M_AXI_GP1_WDATA;
  output [3:0]M_AXI_GP1_ARCACHE;
  output [3:0]M_AXI_GP1_ARLEN;
  output [3:0]M_AXI_GP1_ARQOS;
  output [3:0]M_AXI_GP1_AWCACHE;
  output [3:0]M_AXI_GP1_AWLEN;
  output [3:0]M_AXI_GP1_AWQOS;
  output [3:0]M_AXI_GP1_WSTRB;
  input M_AXI_GP1_ACLK;
  input M_AXI_GP1_ARREADY;
  input M_AXI_GP1_AWREADY;
  input M_AXI_GP1_BVALID;
  input M_AXI_GP1_RLAST;
  input M_AXI_GP1_RVALID;
  input M_AXI_GP1_WREADY;
  input [11:0]M_AXI_GP1_BID;
  input [11:0]M_AXI_GP1_RID;
  input [1:0]M_AXI_GP1_BRESP;
  input [1:0]M_AXI_GP1_RRESP;
  input [31:0]M_AXI_GP1_RDATA;
  output S_AXI_GP0_ARESETN;
  output S_AXI_GP0_ARREADY;
  output S_AXI_GP0_AWREADY;
  output S_AXI_GP0_BVALID;
  output S_AXI_GP0_RLAST;
  output S_AXI_GP0_RVALID;
  output S_AXI_GP0_WREADY;
  output [1:0]S_AXI_GP0_BRESP;
  output [1:0]S_AXI_GP0_RRESP;
  output [31:0]S_AXI_GP0_RDATA;
  output [5:0]S_AXI_GP0_BID;
  output [5:0]S_AXI_GP0_RID;
  input S_AXI_GP0_ACLK;
  input S_AXI_GP0_ARVALID;
  input S_AXI_GP0_AWVALID;
  input S_AXI_GP0_BREADY;
  input S_AXI_GP0_RREADY;
  input S_AXI_GP0_WLAST;
  input S_AXI_GP0_WVALID;
  input [1:0]S_AXI_GP0_ARBURST;
  input [1:0]S_AXI_GP0_ARLOCK;
  input [2:0]S_AXI_GP0_ARSIZE;
  input [1:0]S_AXI_GP0_AWBURST;
  input [1:0]S_AXI_GP0_AWLOCK;
  input [2:0]S_AXI_GP0_AWSIZE;
  input [2:0]S_AXI_GP0_ARPROT;
  input [2:0]S_AXI_GP0_AWPROT;
  input [31:0]S_AXI_GP0_ARADDR;
  input [31:0]S_AXI_GP0_AWADDR;
  input [31:0]S_AXI_GP0_WDATA;
  input [3:0]S_AXI_GP0_ARCACHE;
  input [3:0]S_AXI_GP0_ARLEN;
  input [3:0]S_AXI_GP0_ARQOS;
  input [3:0]S_AXI_GP0_AWCACHE;
  input [3:0]S_AXI_GP0_AWLEN;
  input [3:0]S_AXI_GP0_AWQOS;
  input [3:0]S_AXI_GP0_WSTRB;
  input [5:0]S_AXI_GP0_ARID;
  input [5:0]S_AXI_GP0_AWID;
  input [5:0]S_AXI_GP0_WID;
  output S_AXI_GP1_ARESETN;
  output S_AXI_GP1_ARREADY;
  output S_AXI_GP1_AWREADY;
  output S_AXI_GP1_BVALID;
  output S_AXI_GP1_RLAST;
  output S_AXI_GP1_RVALID;
  output S_AXI_GP1_WREADY;
  output [1:0]S_AXI_GP1_BRESP;
  output [1:0]S_AXI_GP1_RRESP;
  output [31:0]S_AXI_GP1_RDATA;
  output [5:0]S_AXI_GP1_BID;
  output [5:0]S_AXI_GP1_RID;
  input S_AXI_GP1_ACLK;
  input S_AXI_GP1_ARVALID;
  input S_AXI_GP1_AWVALID;
  input S_AXI_GP1_BREADY;
  input S_AXI_GP1_RREADY;
  input S_AXI_GP1_WLAST;
  input S_AXI_GP1_WVALID;
  input [1:0]S_AXI_GP1_ARBURST;
  input [1:0]S_AXI_GP1_ARLOCK;
  input [2:0]S_AXI_GP1_ARSIZE;
  input [1:0]S_AXI_GP1_AWBURST;
  input [1:0]S_AXI_GP1_AWLOCK;
  input [2:0]S_AXI_GP1_AWSIZE;
  input [2:0]S_AXI_GP1_ARPROT;
  input [2:0]S_AXI_GP1_AWPROT;
  input [31:0]S_AXI_GP1_ARADDR;
  input [31:0]S_AXI_GP1_AWADDR;
  input [31:0]S_AXI_GP1_WDATA;
  input [3:0]S_AXI_GP1_ARCACHE;
  input [3:0]S_AXI_GP1_ARLEN;
  input [3:0]S_AXI_GP1_ARQOS;
  input [3:0]S_AXI_GP1_AWCACHE;
  input [3:0]S_AXI_GP1_AWLEN;
  input [3:0]S_AXI_GP1_AWQOS;
  input [3:0]S_AXI_GP1_WSTRB;
  input [5:0]S_AXI_GP1_ARID;
  input [5:0]S_AXI_GP1_AWID;
  input [5:0]S_AXI_GP1_WID;
  output S_AXI_ACP_ARESETN;
  output S_AXI_ACP_ARREADY;
  output S_AXI_ACP_AWREADY;
  output S_AXI_ACP_BVALID;
  output S_AXI_ACP_RLAST;
  output S_AXI_ACP_RVALID;
  output S_AXI_ACP_WREADY;
  output [1:0]S_AXI_ACP_BRESP;
  output [1:0]S_AXI_ACP_RRESP;
  output [2:0]S_AXI_ACP_BID;
  output [2:0]S_AXI_ACP_RID;
  output [63:0]S_AXI_ACP_RDATA;
  input S_AXI_ACP_ACLK;
  input S_AXI_ACP_ARVALID;
  input S_AXI_ACP_AWVALID;
  input S_AXI_ACP_BREADY;
  input S_AXI_ACP_RREADY;
  input S_AXI_ACP_WLAST;
  input S_AXI_ACP_WVALID;
  input [2:0]S_AXI_ACP_ARID;
  input [2:0]S_AXI_ACP_ARPROT;
  input [2:0]S_AXI_ACP_AWID;
  input [2:0]S_AXI_ACP_AWPROT;
  input [2:0]S_AXI_ACP_WID;
  input [31:0]S_AXI_ACP_ARADDR;
  input [31:0]S_AXI_ACP_AWADDR;
  input [3:0]S_AXI_ACP_ARCACHE;
  input [3:0]S_AXI_ACP_ARLEN;
  input [3:0]S_AXI_ACP_ARQOS;
  input [3:0]S_AXI_ACP_AWCACHE;
  input [3:0]S_AXI_ACP_AWLEN;
  input [3:0]S_AXI_ACP_AWQOS;
  input [1:0]S_AXI_ACP_ARBURST;
  input [1:0]S_AXI_ACP_ARLOCK;
  input [2:0]S_AXI_ACP_ARSIZE;
  input [1:0]S_AXI_ACP_AWBURST;
  input [1:0]S_AXI_ACP_AWLOCK;
  input [2:0]S_AXI_ACP_AWSIZE;
  input [4:0]S_AXI_ACP_ARUSER;
  input [4:0]S_AXI_ACP_AWUSER;
  input [63:0]S_AXI_ACP_WDATA;
  input [7:0]S_AXI_ACP_WSTRB;
  output S_AXI_HP0_ARESETN;
  output S_AXI_HP0_ARREADY;
  output S_AXI_HP0_AWREADY;
  output S_AXI_HP0_BVALID;
  output S_AXI_HP0_RLAST;
  output S_AXI_HP0_RVALID;
  output S_AXI_HP0_WREADY;
  output [1:0]S_AXI_HP0_BRESP;
  output [1:0]S_AXI_HP0_RRESP;
  output [5:0]S_AXI_HP0_BID;
  output [5:0]S_AXI_HP0_RID;
  output [63:0]S_AXI_HP0_RDATA;
  output [7:0]S_AXI_HP0_RCOUNT;
  output [7:0]S_AXI_HP0_WCOUNT;
  output [2:0]S_AXI_HP0_RACOUNT;
  output [5:0]S_AXI_HP0_WACOUNT;
  input S_AXI_HP0_ACLK;
  input S_AXI_HP0_ARVALID;
  input S_AXI_HP0_AWVALID;
  input S_AXI_HP0_BREADY;
  input S_AXI_HP0_RDISSUECAP1_EN;
  input S_AXI_HP0_RREADY;
  input S_AXI_HP0_WLAST;
  input S_AXI_HP0_WRISSUECAP1_EN;
  input S_AXI_HP0_WVALID;
  input [1:0]S_AXI_HP0_ARBURST;
  input [1:0]S_AXI_HP0_ARLOCK;
  input [2:0]S_AXI_HP0_ARSIZE;
  input [1:0]S_AXI_HP0_AWBURST;
  input [1:0]S_AXI_HP0_AWLOCK;
  input [2:0]S_AXI_HP0_AWSIZE;
  input [2:0]S_AXI_HP0_ARPROT;
  input [2:0]S_AXI_HP0_AWPROT;
  input [31:0]S_AXI_HP0_ARADDR;
  input [31:0]S_AXI_HP0_AWADDR;
  input [3:0]S_AXI_HP0_ARCACHE;
  input [3:0]S_AXI_HP0_ARLEN;
  input [3:0]S_AXI_HP0_ARQOS;
  input [3:0]S_AXI_HP0_AWCACHE;
  input [3:0]S_AXI_HP0_AWLEN;
  input [3:0]S_AXI_HP0_AWQOS;
  input [5:0]S_AXI_HP0_ARID;
  input [5:0]S_AXI_HP0_AWID;
  input [5:0]S_AXI_HP0_WID;
  input [63:0]S_AXI_HP0_WDATA;
  input [7:0]S_AXI_HP0_WSTRB;
  output S_AXI_HP1_ARESETN;
  output S_AXI_HP1_ARREADY;
  output S_AXI_HP1_AWREADY;
  output S_AXI_HP1_BVALID;
  output S_AXI_HP1_RLAST;
  output S_AXI_HP1_RVALID;
  output S_AXI_HP1_WREADY;
  output [1:0]S_AXI_HP1_BRESP;
  output [1:0]S_AXI_HP1_RRESP;
  output [5:0]S_AXI_HP1_BID;
  output [5:0]S_AXI_HP1_RID;
  output [63:0]S_AXI_HP1_RDATA;
  output [7:0]S_AXI_HP1_RCOUNT;
  output [7:0]S_AXI_HP1_WCOUNT;
  output [2:0]S_AXI_HP1_RACOUNT;
  output [5:0]S_AXI_HP1_WACOUNT;
  input S_AXI_HP1_ACLK;
  input S_AXI_HP1_ARVALID;
  input S_AXI_HP1_AWVALID;
  input S_AXI_HP1_BREADY;
  input S_AXI_HP1_RDISSUECAP1_EN;
  input S_AXI_HP1_RREADY;
  input S_AXI_HP1_WLAST;
  input S_AXI_HP1_WRISSUECAP1_EN;
  input S_AXI_HP1_WVALID;
  input [1:0]S_AXI_HP1_ARBURST;
  input [1:0]S_AXI_HP1_ARLOCK;
  input [2:0]S_AXI_HP1_ARSIZE;
  input [1:0]S_AXI_HP1_AWBURST;
  input [1:0]S_AXI_HP1_AWLOCK;
  input [2:0]S_AXI_HP1_AWSIZE;
  input [2:0]S_AXI_HP1_ARPROT;
  input [2:0]S_AXI_HP1_AWPROT;
  input [31:0]S_AXI_HP1_ARADDR;
  input [31:0]S_AXI_HP1_AWADDR;
  input [3:0]S_AXI_HP1_ARCACHE;
  input [3:0]S_AXI_HP1_ARLEN;
  input [3:0]S_AXI_HP1_ARQOS;
  input [3:0]S_AXI_HP1_AWCACHE;
  input [3:0]S_AXI_HP1_AWLEN;
  input [3:0]S_AXI_HP1_AWQOS;
  input [5:0]S_AXI_HP1_ARID;
  input [5:0]S_AXI_HP1_AWID;
  input [5:0]S_AXI_HP1_WID;
  input [63:0]S_AXI_HP1_WDATA;
  input [7:0]S_AXI_HP1_WSTRB;
  output S_AXI_HP2_ARESETN;
  output S_AXI_HP2_ARREADY;
  output S_AXI_HP2_AWREADY;
  output S_AXI_HP2_BVALID;
  output S_AXI_HP2_RLAST;
  output S_AXI_HP2_RVALID;
  output S_AXI_HP2_WREADY;
  output [1:0]S_AXI_HP2_BRESP;
  output [1:0]S_AXI_HP2_RRESP;
  output [5:0]S_AXI_HP2_BID;
  output [5:0]S_AXI_HP2_RID;
  output [63:0]S_AXI_HP2_RDATA;
  output [7:0]S_AXI_HP2_RCOUNT;
  output [7:0]S_AXI_HP2_WCOUNT;
  output [2:0]S_AXI_HP2_RACOUNT;
  output [5:0]S_AXI_HP2_WACOUNT;
  input S_AXI_HP2_ACLK;
  input S_AXI_HP2_ARVALID;
  input S_AXI_HP2_AWVALID;
  input S_AXI_HP2_BREADY;
  input S_AXI_HP2_RDISSUECAP1_EN;
  input S_AXI_HP2_RREADY;
  input S_AXI_HP2_WLAST;
  input S_AXI_HP2_WRISSUECAP1_EN;
  input S_AXI_HP2_WVALID;
  input [1:0]S_AXI_HP2_ARBURST;
  input [1:0]S_AXI_HP2_ARLOCK;
  input [2:0]S_AXI_HP2_ARSIZE;
  input [1:0]S_AXI_HP2_AWBURST;
  input [1:0]S_AXI_HP2_AWLOCK;
  input [2:0]S_AXI_HP2_AWSIZE;
  input [2:0]S_AXI_HP2_ARPROT;
  input [2:0]S_AXI_HP2_AWPROT;
  input [31:0]S_AXI_HP2_ARADDR;
  input [31:0]S_AXI_HP2_AWADDR;
  input [3:0]S_AXI_HP2_ARCACHE;
  input [3:0]S_AXI_HP2_ARLEN;
  input [3:0]S_AXI_HP2_ARQOS;
  input [3:0]S_AXI_HP2_AWCACHE;
  input [3:0]S_AXI_HP2_AWLEN;
  input [3:0]S_AXI_HP2_AWQOS;
  input [5:0]S_AXI_HP2_ARID;
  input [5:0]S_AXI_HP2_AWID;
  input [5:0]S_AXI_HP2_WID;
  input [63:0]S_AXI_HP2_WDATA;
  input [7:0]S_AXI_HP2_WSTRB;
  output S_AXI_HP3_ARESETN;
  output S_AXI_HP3_ARREADY;
  output S_AXI_HP3_AWREADY;
  output S_AXI_HP3_BVALID;
  output S_AXI_HP3_RLAST;
  output S_AXI_HP3_RVALID;
  output S_AXI_HP3_WREADY;
  output [1:0]S_AXI_HP3_BRESP;
  output [1:0]S_AXI_HP3_RRESP;
  output [5:0]S_AXI_HP3_BID;
  output [5:0]S_AXI_HP3_RID;
  output [63:0]S_AXI_HP3_RDATA;
  output [7:0]S_AXI_HP3_RCOUNT;
  output [7:0]S_AXI_HP3_WCOUNT;
  output [2:0]S_AXI_HP3_RACOUNT;
  output [5:0]S_AXI_HP3_WACOUNT;
  input S_AXI_HP3_ACLK;
  input S_AXI_HP3_ARVALID;
  input S_AXI_HP3_AWVALID;
  input S_AXI_HP3_BREADY;
  input S_AXI_HP3_RDISSUECAP1_EN;
  input S_AXI_HP3_RREADY;
  input S_AXI_HP3_WLAST;
  input S_AXI_HP3_WRISSUECAP1_EN;
  input S_AXI_HP3_WVALID;
  input [1:0]S_AXI_HP3_ARBURST;
  input [1:0]S_AXI_HP3_ARLOCK;
  input [2:0]S_AXI_HP3_ARSIZE;
  input [1:0]S_AXI_HP3_AWBURST;
  input [1:0]S_AXI_HP3_AWLOCK;
  input [2:0]S_AXI_HP3_AWSIZE;
  input [2:0]S_AXI_HP3_ARPROT;
  input [2:0]S_AXI_HP3_AWPROT;
  input [31:0]S_AXI_HP3_ARADDR;
  input [31:0]S_AXI_HP3_AWADDR;
  input [3:0]S_AXI_HP3_ARCACHE;
  input [3:0]S_AXI_HP3_ARLEN;
  input [3:0]S_AXI_HP3_ARQOS;
  input [3:0]S_AXI_HP3_AWCACHE;
  input [3:0]S_AXI_HP3_AWLEN;
  input [3:0]S_AXI_HP3_AWQOS;
  input [5:0]S_AXI_HP3_ARID;
  input [5:0]S_AXI_HP3_AWID;
  input [5:0]S_AXI_HP3_WID;
  input [63:0]S_AXI_HP3_WDATA;
  input [7:0]S_AXI_HP3_WSTRB;
  output IRQ_P2F_DMAC_ABORT;
  output IRQ_P2F_DMAC0;
  output IRQ_P2F_DMAC1;
  output IRQ_P2F_DMAC2;
  output IRQ_P2F_DMAC3;
  output IRQ_P2F_DMAC4;
  output IRQ_P2F_DMAC5;
  output IRQ_P2F_DMAC6;
  output IRQ_P2F_DMAC7;
  output IRQ_P2F_SMC;
  output IRQ_P2F_QSPI;
  output IRQ_P2F_CTI;
  output IRQ_P2F_GPIO;
  output IRQ_P2F_USB0;
  output IRQ_P2F_ENET0;
  output IRQ_P2F_ENET_WAKE0;
  output IRQ_P2F_SDIO0;
  output IRQ_P2F_I2C0;
  output IRQ_P2F_SPI0;
  output IRQ_P2F_UART0;
  output IRQ_P2F_CAN0;
  output IRQ_P2F_USB1;
  output IRQ_P2F_ENET1;
  output IRQ_P2F_ENET_WAKE1;
  output IRQ_P2F_SDIO1;
  output IRQ_P2F_I2C1;
  output IRQ_P2F_SPI1;
  output IRQ_P2F_UART1;
  output IRQ_P2F_CAN1;
  input [0:0]IRQ_F2P;
  input Core0_nFIQ;
  input Core0_nIRQ;
  input Core1_nFIQ;
  input Core1_nIRQ;
  output [1:0]DMA0_DATYPE;
  output DMA0_DAVALID;
  output DMA0_DRREADY;
  output DMA0_RSTN;
  output [1:0]DMA1_DATYPE;
  output DMA1_DAVALID;
  output DMA1_DRREADY;
  output DMA1_RSTN;
  output [1:0]DMA2_DATYPE;
  output DMA2_DAVALID;
  output DMA2_DRREADY;
  output DMA2_RSTN;
  output [1:0]DMA3_DATYPE;
  output DMA3_DAVALID;
  output DMA3_DRREADY;
  output DMA3_RSTN;
  input DMA0_ACLK;
  input DMA0_DAREADY;
  input DMA0_DRLAST;
  input DMA0_DRVALID;
  input DMA1_ACLK;
  input DMA1_DAREADY;
  input DMA1_DRLAST;
  input DMA1_DRVALID;
  input DMA2_ACLK;
  input DMA2_DAREADY;
  input DMA2_DRLAST;
  input DMA2_DRVALID;
  input DMA3_ACLK;
  input DMA3_DAREADY;
  input DMA3_DRLAST;
  input DMA3_DRVALID;
  input [1:0]DMA0_DRTYPE;
  input [1:0]DMA1_DRTYPE;
  input [1:0]DMA2_DRTYPE;
  input [1:0]DMA3_DRTYPE;
  output FCLK_CLK3;
  output FCLK_CLK2;
  output FCLK_CLK1;
  output FCLK_CLK0;
  input FCLK_CLKTRIG3_N;
  input FCLK_CLKTRIG2_N;
  input FCLK_CLKTRIG1_N;
  input FCLK_CLKTRIG0_N;
  output FCLK_RESET3_N;
  output FCLK_RESET2_N;
  output FCLK_RESET1_N;
  output FCLK_RESET0_N;
  input [31:0]FTMD_TRACEIN_DATA;
  input FTMD_TRACEIN_VALID;
  input FTMD_TRACEIN_CLK;
  input [3:0]FTMD_TRACEIN_ATID;
  input FTMT_F2P_TRIG_0;
  output FTMT_F2P_TRIGACK_0;
  input FTMT_F2P_TRIG_1;
  output FTMT_F2P_TRIGACK_1;
  input FTMT_F2P_TRIG_2;
  output FTMT_F2P_TRIGACK_2;
  input FTMT_F2P_TRIG_3;
  output FTMT_F2P_TRIGACK_3;
  input [31:0]FTMT_F2P_DEBUG;
  input FTMT_P2F_TRIGACK_0;
  output FTMT_P2F_TRIG_0;
  input FTMT_P2F_TRIGACK_1;
  output FTMT_P2F_TRIG_1;
  input FTMT_P2F_TRIGACK_2;
  output FTMT_P2F_TRIG_2;
  input FTMT_P2F_TRIGACK_3;
  output FTMT_P2F_TRIG_3;
  output [31:0]FTMT_P2F_DEBUG;
  input FPGA_IDLE_N;
  output EVENT_EVENTO;
  output [1:0]EVENT_STANDBYWFE;
  output [1:0]EVENT_STANDBYWFI;
  input EVENT_EVENTI;
  input [3:0]DDR_ARB;
  inout [53:0]MIO;
  inout DDR_CAS_n;
  inout DDR_CKE;
  inout DDR_Clk_n;
  inout DDR_Clk;
  inout DDR_CS_n;
  inout DDR_DRSTB;
  inout DDR_ODT;
  inout DDR_RAS_n;
  inout DDR_WEB;
  inout [2:0]DDR_BankAddr;
  inout [14:0]DDR_Addr;
  inout DDR_VRN;
  inout DDR_VRP;
  inout [3:0]DDR_DM;
  inout [31:0]DDR_DQ;
  inout [3:0]DDR_DQS_n;
  inout [3:0]DDR_DQS;
  inout PS_SRSTB;
  inout PS_CLK;
  inout PS_PORB;

  wire \<const0> ;
  wire \<const1> ;
  wire CAN0_PHY_RX;
  wire CAN0_PHY_TX;
  wire CAN1_PHY_RX;
  wire CAN1_PHY_TX;
  wire Core0_nFIQ;
  wire Core0_nIRQ;
  wire Core1_nFIQ;
  wire Core1_nIRQ;
  wire [3:0]DDR_ARB;
  wire [14:0]DDR_Addr;
  wire [2:0]DDR_BankAddr;
  wire DDR_CAS_n;
  wire DDR_CKE;
  wire DDR_CS_n;
  wire DDR_Clk;
  wire DDR_Clk_n;
  wire [3:0]DDR_DM;
  wire [31:0]DDR_DQ;
  wire [3:0]DDR_DQS;
  wire [3:0]DDR_DQS_n;
  wire DDR_DRSTB;
  wire DDR_ODT;
  wire DDR_RAS_n;
  wire DDR_VRN;
  wire DDR_VRP;
  wire DDR_WEB;
  wire DMA0_ACLK;
  wire DMA0_DAREADY;
  wire [1:0]DMA0_DATYPE;
  wire DMA0_DAVALID;
  wire DMA0_DRLAST;
  wire DMA0_DRREADY;
  wire [1:0]DMA0_DRTYPE;
  wire DMA0_DRVALID;
  wire DMA0_RSTN;
  wire DMA1_ACLK;
  wire DMA1_DAREADY;
  wire [1:0]DMA1_DATYPE;
  wire DMA1_DAVALID;
  wire DMA1_DRLAST;
  wire DMA1_DRREADY;
  wire [1:0]DMA1_DRTYPE;
  wire DMA1_DRVALID;
  wire DMA1_RSTN;
  wire DMA2_ACLK;
  wire DMA2_DAREADY;
  wire [1:0]DMA2_DATYPE;
  wire DMA2_DAVALID;
  wire DMA2_DRLAST;
  wire DMA2_DRREADY;
  wire [1:0]DMA2_DRTYPE;
  wire DMA2_DRVALID;
  wire DMA2_RSTN;
  wire DMA3_ACLK;
  wire DMA3_DAREADY;
  wire [1:0]DMA3_DATYPE;
  wire DMA3_DAVALID;
  wire DMA3_DRLAST;
  wire DMA3_DRREADY;
  wire [1:0]DMA3_DRTYPE;
  wire DMA3_DRVALID;
  wire DMA3_RSTN;
  wire ENET0_EXT_INTIN;
  wire ENET0_GMII_RX_CLK;
  wire ENET0_GMII_TX_CLK;
  wire ENET0_MDIO_I;
  wire ENET0_MDIO_MDC;
  wire ENET0_MDIO_O;
  wire ENET0_MDIO_T;
  wire ENET0_MDIO_T_n;
  wire ENET0_PTP_DELAY_REQ_RX;
  wire ENET0_PTP_DELAY_REQ_TX;
  wire ENET0_PTP_PDELAY_REQ_RX;
  wire ENET0_PTP_PDELAY_REQ_TX;
  wire ENET0_PTP_PDELAY_RESP_RX;
  wire ENET0_PTP_PDELAY_RESP_TX;
  wire ENET0_PTP_SYNC_FRAME_RX;
  wire ENET0_PTP_SYNC_FRAME_TX;
  wire ENET0_SOF_RX;
  wire ENET0_SOF_TX;
  wire ENET1_EXT_INTIN;
  wire ENET1_GMII_RX_CLK;
  wire ENET1_GMII_TX_CLK;
  wire ENET1_MDIO_I;
  wire ENET1_MDIO_MDC;
  wire ENET1_MDIO_O;
  wire ENET1_MDIO_T;
  wire ENET1_MDIO_T_n;
  wire ENET1_PTP_DELAY_REQ_RX;
  wire ENET1_PTP_DELAY_REQ_TX;
  wire ENET1_PTP_PDELAY_REQ_RX;
  wire ENET1_PTP_PDELAY_REQ_TX;
  wire ENET1_PTP_PDELAY_RESP_RX;
  wire ENET1_PTP_PDELAY_RESP_TX;
  wire ENET1_PTP_SYNC_FRAME_RX;
  wire ENET1_PTP_SYNC_FRAME_TX;
  wire ENET1_SOF_RX;
  wire ENET1_SOF_TX;
  wire EVENT_EVENTI;
  wire EVENT_EVENTO;
  wire [1:0]EVENT_STANDBYWFE;
  wire [1:0]EVENT_STANDBYWFI;
  wire FCLK_CLK0;
  wire FCLK_CLK1;
  wire FCLK_CLK2;
  wire FCLK_CLK3;
  wire [0:0]FCLK_CLK_unbuffered;
  wire FCLK_RESET0_N;
  wire FCLK_RESET1_N;
  wire FCLK_RESET2_N;
  wire FCLK_RESET3_N;
  wire FPGA_IDLE_N;
  wire FTMD_TRACEIN_CLK;
  wire [31:0]FTMT_F2P_DEBUG;
  wire FTMT_F2P_TRIGACK_0;
  wire FTMT_F2P_TRIGACK_1;
  wire FTMT_F2P_TRIGACK_2;
  wire FTMT_F2P_TRIGACK_3;
  wire FTMT_F2P_TRIG_0;
  wire FTMT_F2P_TRIG_1;
  wire FTMT_F2P_TRIG_2;
  wire FTMT_F2P_TRIG_3;
  wire [31:0]FTMT_P2F_DEBUG;
  wire FTMT_P2F_TRIGACK_0;
  wire FTMT_P2F_TRIGACK_1;
  wire FTMT_P2F_TRIGACK_2;
  wire FTMT_P2F_TRIGACK_3;
  wire FTMT_P2F_TRIG_0;
  wire FTMT_P2F_TRIG_1;
  wire FTMT_P2F_TRIG_2;
  wire FTMT_P2F_TRIG_3;
  wire [63:0]GPIO_I;
  wire [63:0]GPIO_O;
  wire [63:0]GPIO_T;
  wire I2C0_SCL_I;
  wire I2C0_SCL_O;
  wire I2C0_SCL_T;
  wire I2C0_SCL_T_n;
  wire I2C0_SDA_I;
  wire I2C0_SDA_O;
  wire I2C0_SDA_T;
  wire I2C0_SDA_T_n;
  wire I2C1_SCL_I;
  wire I2C1_SCL_O;
  wire I2C1_SCL_T;
  wire I2C1_SCL_T_n;
  wire I2C1_SDA_I;
  wire I2C1_SDA_O;
  wire I2C1_SDA_T;
  wire I2C1_SDA_T_n;
  wire [0:0]IRQ_F2P;
  wire IRQ_P2F_CAN0;
  wire IRQ_P2F_CAN1;
  wire IRQ_P2F_CTI;
  wire IRQ_P2F_DMAC0;
  wire IRQ_P2F_DMAC1;
  wire IRQ_P2F_DMAC2;
  wire IRQ_P2F_DMAC3;
  wire IRQ_P2F_DMAC4;
  wire IRQ_P2F_DMAC5;
  wire IRQ_P2F_DMAC6;
  wire IRQ_P2F_DMAC7;
  wire IRQ_P2F_DMAC_ABORT;
  wire IRQ_P2F_ENET0;
  wire IRQ_P2F_ENET1;
  wire IRQ_P2F_ENET_WAKE0;
  wire IRQ_P2F_ENET_WAKE1;
  wire IRQ_P2F_GPIO;
  wire IRQ_P2F_I2C0;
  wire IRQ_P2F_I2C1;
  wire IRQ_P2F_QSPI;
  wire IRQ_P2F_SDIO0;
  wire IRQ_P2F_SDIO1;
  wire IRQ_P2F_SMC;
  wire IRQ_P2F_SPI0;
  wire IRQ_P2F_SPI1;
  wire IRQ_P2F_UART0;
  wire IRQ_P2F_UART1;
  wire IRQ_P2F_USB0;
  wire IRQ_P2F_USB1;
  wire [53:0]MIO;
  wire M_AXI_GP0_ACLK;
  wire [31:0]M_AXI_GP0_ARADDR;
  wire [1:0]M_AXI_GP0_ARBURST;
  wire [3:0]\^M_AXI_GP0_ARCACHE ;
  wire M_AXI_GP0_ARESETN;
  wire [11:0]M_AXI_GP0_ARID;
  wire [3:0]M_AXI_GP0_ARLEN;
  wire [1:0]M_AXI_GP0_ARLOCK;
  wire [2:0]M_AXI_GP0_ARPROT;
  wire [3:0]M_AXI_GP0_ARQOS;
  wire M_AXI_GP0_ARREADY;
  wire [1:0]\^M_AXI_GP0_ARSIZE ;
  wire M_AXI_GP0_ARVALID;
  wire [31:0]M_AXI_GP0_AWADDR;
  wire [1:0]M_AXI_GP0_AWBURST;
  wire [3:0]\^M_AXI_GP0_AWCACHE ;
  wire [11:0]M_AXI_GP0_AWID;
  wire [3:0]M_AXI_GP0_AWLEN;
  wire [1:0]M_AXI_GP0_AWLOCK;
  wire [2:0]M_AXI_GP0_AWPROT;
  wire [3:0]M_AXI_GP0_AWQOS;
  wire M_AXI_GP0_AWREADY;
  wire [1:0]\^M_AXI_GP0_AWSIZE ;
  wire M_AXI_GP0_AWVALID;
  wire [11:0]M_AXI_GP0_BID;
  wire M_AXI_GP0_BREADY;
  wire [1:0]M_AXI_GP0_BRESP;
  wire M_AXI_GP0_BVALID;
  wire [31:0]M_AXI_GP0_RDATA;
  wire [11:0]M_AXI_GP0_RID;
  wire M_AXI_GP0_RLAST;
  wire M_AXI_GP0_RREADY;
  wire [1:0]M_AXI_GP0_RRESP;
  wire M_AXI_GP0_RVALID;
  wire [31:0]M_AXI_GP0_WDATA;
  wire [11:0]M_AXI_GP0_WID;
  wire M_AXI_GP0_WLAST;
  wire M_AXI_GP0_WREADY;
  wire [3:0]M_AXI_GP0_WSTRB;
  wire M_AXI_GP0_WVALID;
  wire M_AXI_GP1_ACLK;
  wire [31:0]M_AXI_GP1_ARADDR;
  wire [1:0]M_AXI_GP1_ARBURST;
  wire [3:0]\^M_AXI_GP1_ARCACHE ;
  wire M_AXI_GP1_ARESETN;
  wire [11:0]M_AXI_GP1_ARID;
  wire [3:0]M_AXI_GP1_ARLEN;
  wire [1:0]M_AXI_GP1_ARLOCK;
  wire [2:0]M_AXI_GP1_ARPROT;
  wire [3:0]M_AXI_GP1_ARQOS;
  wire M_AXI_GP1_ARREADY;
  wire [1:0]\^M_AXI_GP1_ARSIZE ;
  wire M_AXI_GP1_ARVALID;
  wire [31:0]M_AXI_GP1_AWADDR;
  wire [1:0]M_AXI_GP1_AWBURST;
  wire [3:0]\^M_AXI_GP1_AWCACHE ;
  wire [11:0]M_AXI_GP1_AWID;
  wire [3:0]M_AXI_GP1_AWLEN;
  wire [1:0]M_AXI_GP1_AWLOCK;
  wire [2:0]M_AXI_GP1_AWPROT;
  wire [3:0]M_AXI_GP1_AWQOS;
  wire M_AXI_GP1_AWREADY;
  wire [1:0]\^M_AXI_GP1_AWSIZE ;
  wire M_AXI_GP1_AWVALID;
  wire [11:0]M_AXI_GP1_BID;
  wire M_AXI_GP1_BREADY;
  wire [1:0]M_AXI_GP1_BRESP;
  wire M_AXI_GP1_BVALID;
  wire [31:0]M_AXI_GP1_RDATA;
  wire [11:0]M_AXI_GP1_RID;
  wire M_AXI_GP1_RLAST;
  wire M_AXI_GP1_RREADY;
  wire [1:0]M_AXI_GP1_RRESP;
  wire M_AXI_GP1_RVALID;
  wire [31:0]M_AXI_GP1_WDATA;
  wire [11:0]M_AXI_GP1_WID;
  wire M_AXI_GP1_WLAST;
  wire M_AXI_GP1_WREADY;
  wire [3:0]M_AXI_GP1_WSTRB;
  wire M_AXI_GP1_WVALID;
  wire PJTAG_TCK;
  wire PJTAG_TDI;
  wire PJTAG_TMS;
  wire PS_CLK;
  wire PS_PORB;
  wire PS_SRSTB;
  wire SDIO0_BUSPOW;
  wire [2:0]SDIO0_BUSVOLT;
  wire SDIO0_CDN;
  wire SDIO0_CLK;
  wire SDIO0_CLK_FB;
  wire SDIO0_CMD_I;
  wire SDIO0_CMD_O;
  wire SDIO0_CMD_T;
  wire SDIO0_CMD_T_n;
  wire [3:0]SDIO0_DATA_I;
  wire [3:0]SDIO0_DATA_O;
  wire [3:0]SDIO0_DATA_T;
  wire [3:0]SDIO0_DATA_T_n;
  wire SDIO0_LED;
  wire SDIO0_WP;
  wire SDIO1_BUSPOW;
  wire [2:0]SDIO1_BUSVOLT;
  wire SDIO1_CDN;
  wire SDIO1_CLK;
  wire SDIO1_CLK_FB;
  wire SDIO1_CMD_I;
  wire SDIO1_CMD_O;
  wire SDIO1_CMD_T;
  wire SDIO1_CMD_T_n;
  wire [3:0]SDIO1_DATA_I;
  wire [3:0]SDIO1_DATA_O;
  wire [3:0]SDIO1_DATA_T;
  wire [3:0]SDIO1_DATA_T_n;
  wire SDIO1_LED;
  wire SDIO1_WP;
  wire SPI0_MISO_I;
  wire SPI0_MISO_O;
  wire SPI0_MISO_T;
  wire SPI0_MISO_T_n;
  wire SPI0_MOSI_I;
  wire SPI0_MOSI_O;
  wire SPI0_MOSI_T;
  wire SPI0_MOSI_T_n;
  wire SPI0_SCLK_I;
  wire SPI0_SCLK_O;
  wire SPI0_SCLK_T;
  wire SPI0_SCLK_T_n;
  wire SPI0_SS1_O;
  wire SPI0_SS2_O;
  wire SPI0_SS_I;
  wire SPI0_SS_O;
  wire SPI0_SS_T;
  wire SPI0_SS_T_n;
  wire SPI1_MISO_I;
  wire SPI1_MISO_O;
  wire SPI1_MISO_T;
  wire SPI1_MISO_T_n;
  wire SPI1_MOSI_I;
  wire SPI1_MOSI_O;
  wire SPI1_MOSI_T;
  wire SPI1_MOSI_T_n;
  wire SPI1_SCLK_I;
  wire SPI1_SCLK_O;
  wire SPI1_SCLK_T;
  wire SPI1_SCLK_T_n;
  wire SPI1_SS1_O;
  wire SPI1_SS2_O;
  wire SPI1_SS_I;
  wire SPI1_SS_O;
  wire SPI1_SS_T;
  wire SPI1_SS_T_n;
  wire SRAM_INTIN;
  wire S_AXI_ACP_ACLK;
  wire [31:0]S_AXI_ACP_ARADDR;
  wire [1:0]S_AXI_ACP_ARBURST;
  wire [3:0]S_AXI_ACP_ARCACHE;
  wire S_AXI_ACP_ARESETN;
  wire [2:0]S_AXI_ACP_ARID;
  wire [3:0]S_AXI_ACP_ARLEN;
  wire [1:0]S_AXI_ACP_ARLOCK;
  wire [2:0]S_AXI_ACP_ARPROT;
  wire [3:0]S_AXI_ACP_ARQOS;
  wire S_AXI_ACP_ARREADY;
  wire [2:0]S_AXI_ACP_ARSIZE;
  wire [4:0]S_AXI_ACP_ARUSER;
  wire S_AXI_ACP_ARVALID;
  wire [31:0]S_AXI_ACP_AWADDR;
  wire [1:0]S_AXI_ACP_AWBURST;
  wire [3:0]S_AXI_ACP_AWCACHE;
  wire [2:0]S_AXI_ACP_AWID;
  wire [3:0]S_AXI_ACP_AWLEN;
  wire [1:0]S_AXI_ACP_AWLOCK;
  wire [2:0]S_AXI_ACP_AWPROT;
  wire [3:0]S_AXI_ACP_AWQOS;
  wire S_AXI_ACP_AWREADY;
  wire [2:0]S_AXI_ACP_AWSIZE;
  wire [4:0]S_AXI_ACP_AWUSER;
  wire S_AXI_ACP_AWVALID;
  wire [2:0]S_AXI_ACP_BID;
  wire S_AXI_ACP_BREADY;
  wire [1:0]S_AXI_ACP_BRESP;
  wire S_AXI_ACP_BVALID;
  wire [63:0]S_AXI_ACP_RDATA;
  wire [2:0]S_AXI_ACP_RID;
  wire S_AXI_ACP_RLAST;
  wire S_AXI_ACP_RREADY;
  wire [1:0]S_AXI_ACP_RRESP;
  wire S_AXI_ACP_RVALID;
  wire [63:0]S_AXI_ACP_WDATA;
  wire [2:0]S_AXI_ACP_WID;
  wire S_AXI_ACP_WLAST;
  wire S_AXI_ACP_WREADY;
  wire [7:0]S_AXI_ACP_WSTRB;
  wire S_AXI_ACP_WVALID;
  wire S_AXI_GP0_ACLK;
  wire [31:0]S_AXI_GP0_ARADDR;
  wire [1:0]S_AXI_GP0_ARBURST;
  wire [3:0]S_AXI_GP0_ARCACHE;
  wire S_AXI_GP0_ARESETN;
  wire [5:0]S_AXI_GP0_ARID;
  wire [3:0]S_AXI_GP0_ARLEN;
  wire [1:0]S_AXI_GP0_ARLOCK;
  wire [2:0]S_AXI_GP0_ARPROT;
  wire [3:0]S_AXI_GP0_ARQOS;
  wire S_AXI_GP0_ARREADY;
  wire [2:0]S_AXI_GP0_ARSIZE;
  wire S_AXI_GP0_ARVALID;
  wire [31:0]S_AXI_GP0_AWADDR;
  wire [1:0]S_AXI_GP0_AWBURST;
  wire [3:0]S_AXI_GP0_AWCACHE;
  wire [5:0]S_AXI_GP0_AWID;
  wire [3:0]S_AXI_GP0_AWLEN;
  wire [1:0]S_AXI_GP0_AWLOCK;
  wire [2:0]S_AXI_GP0_AWPROT;
  wire [3:0]S_AXI_GP0_AWQOS;
  wire S_AXI_GP0_AWREADY;
  wire [2:0]S_AXI_GP0_AWSIZE;
  wire S_AXI_GP0_AWVALID;
  wire [5:0]S_AXI_GP0_BID;
  wire S_AXI_GP0_BREADY;
  wire [1:0]S_AXI_GP0_BRESP;
  wire S_AXI_GP0_BVALID;
  wire [31:0]S_AXI_GP0_RDATA;
  wire [5:0]S_AXI_GP0_RID;
  wire S_AXI_GP0_RLAST;
  wire S_AXI_GP0_RREADY;
  wire [1:0]S_AXI_GP0_RRESP;
  wire S_AXI_GP0_RVALID;
  wire [31:0]S_AXI_GP0_WDATA;
  wire [5:0]S_AXI_GP0_WID;
  wire S_AXI_GP0_WLAST;
  wire S_AXI_GP0_WREADY;
  wire [3:0]S_AXI_GP0_WSTRB;
  wire S_AXI_GP0_WVALID;
  wire S_AXI_GP1_ACLK;
  wire [31:0]S_AXI_GP1_ARADDR;
  wire [1:0]S_AXI_GP1_ARBURST;
  wire [3:0]S_AXI_GP1_ARCACHE;
  wire S_AXI_GP1_ARESETN;
  wire [5:0]S_AXI_GP1_ARID;
  wire [3:0]S_AXI_GP1_ARLEN;
  wire [1:0]S_AXI_GP1_ARLOCK;
  wire [2:0]S_AXI_GP1_ARPROT;
  wire [3:0]S_AXI_GP1_ARQOS;
  wire S_AXI_GP1_ARREADY;
  wire [2:0]S_AXI_GP1_ARSIZE;
  wire S_AXI_GP1_ARVALID;
  wire [31:0]S_AXI_GP1_AWADDR;
  wire [1:0]S_AXI_GP1_AWBURST;
  wire [3:0]S_AXI_GP1_AWCACHE;
  wire [5:0]S_AXI_GP1_AWID;
  wire [3:0]S_AXI_GP1_AWLEN;
  wire [1:0]S_AXI_GP1_AWLOCK;
  wire [2:0]S_AXI_GP1_AWPROT;
  wire [3:0]S_AXI_GP1_AWQOS;
  wire S_AXI_GP1_AWREADY;
  wire [2:0]S_AXI_GP1_AWSIZE;
  wire S_AXI_GP1_AWVALID;
  wire [5:0]S_AXI_GP1_BID;
  wire S_AXI_GP1_BREADY;
  wire [1:0]S_AXI_GP1_BRESP;
  wire S_AXI_GP1_BVALID;
  wire [31:0]S_AXI_GP1_RDATA;
  wire [5:0]S_AXI_GP1_RID;
  wire S_AXI_GP1_RLAST;
  wire S_AXI_GP1_RREADY;
  wire [1:0]S_AXI_GP1_RRESP;
  wire S_AXI_GP1_RVALID;
  wire [31:0]S_AXI_GP1_WDATA;
  wire [5:0]S_AXI_GP1_WID;
  wire S_AXI_GP1_WLAST;
  wire S_AXI_GP1_WREADY;
  wire [3:0]S_AXI_GP1_WSTRB;
  wire S_AXI_GP1_WVALID;
  wire S_AXI_HP0_ACLK;
  wire [31:0]S_AXI_HP0_ARADDR;
  wire [1:0]S_AXI_HP0_ARBURST;
  wire [3:0]S_AXI_HP0_ARCACHE;
  wire S_AXI_HP0_ARESETN;
  wire [5:0]S_AXI_HP0_ARID;
  wire [3:0]S_AXI_HP0_ARLEN;
  wire [1:0]S_AXI_HP0_ARLOCK;
  wire [2:0]S_AXI_HP0_ARPROT;
  wire [3:0]S_AXI_HP0_ARQOS;
  wire S_AXI_HP0_ARREADY;
  wire [2:0]S_AXI_HP0_ARSIZE;
  wire S_AXI_HP0_ARVALID;
  wire [31:0]S_AXI_HP0_AWADDR;
  wire [1:0]S_AXI_HP0_AWBURST;
  wire [3:0]S_AXI_HP0_AWCACHE;
  wire [5:0]S_AXI_HP0_AWID;
  wire [3:0]S_AXI_HP0_AWLEN;
  wire [1:0]S_AXI_HP0_AWLOCK;
  wire [2:0]S_AXI_HP0_AWPROT;
  wire [3:0]S_AXI_HP0_AWQOS;
  wire S_AXI_HP0_AWREADY;
  wire [2:0]S_AXI_HP0_AWSIZE;
  wire S_AXI_HP0_AWVALID;
  wire [5:0]S_AXI_HP0_BID;
  wire S_AXI_HP0_BREADY;
  wire [1:0]S_AXI_HP0_BRESP;
  wire S_AXI_HP0_BVALID;
  wire [2:0]S_AXI_HP0_RACOUNT;
  wire [7:0]S_AXI_HP0_RCOUNT;
  wire [63:0]S_AXI_HP0_RDATA;
  wire S_AXI_HP0_RDISSUECAP1_EN;
  wire [5:0]S_AXI_HP0_RID;
  wire S_AXI_HP0_RLAST;
  wire S_AXI_HP0_RREADY;
  wire [1:0]S_AXI_HP0_RRESP;
  wire S_AXI_HP0_RVALID;
  wire [5:0]S_AXI_HP0_WACOUNT;
  wire [7:0]S_AXI_HP0_WCOUNT;
  wire [63:0]S_AXI_HP0_WDATA;
  wire [5:0]S_AXI_HP0_WID;
  wire S_AXI_HP0_WLAST;
  wire S_AXI_HP0_WREADY;
  wire S_AXI_HP0_WRISSUECAP1_EN;
  wire [7:0]S_AXI_HP0_WSTRB;
  wire S_AXI_HP0_WVALID;
  wire S_AXI_HP1_ACLK;
  wire [31:0]S_AXI_HP1_ARADDR;
  wire [1:0]S_AXI_HP1_ARBURST;
  wire [3:0]S_AXI_HP1_ARCACHE;
  wire S_AXI_HP1_ARESETN;
  wire [5:0]S_AXI_HP1_ARID;
  wire [3:0]S_AXI_HP1_ARLEN;
  wire [1:0]S_AXI_HP1_ARLOCK;
  wire [2:0]S_AXI_HP1_ARPROT;
  wire [3:0]S_AXI_HP1_ARQOS;
  wire S_AXI_HP1_ARREADY;
  wire [2:0]S_AXI_HP1_ARSIZE;
  wire S_AXI_HP1_ARVALID;
  wire [31:0]S_AXI_HP1_AWADDR;
  wire [1:0]S_AXI_HP1_AWBURST;
  wire [3:0]S_AXI_HP1_AWCACHE;
  wire [5:0]S_AXI_HP1_AWID;
  wire [3:0]S_AXI_HP1_AWLEN;
  wire [1:0]S_AXI_HP1_AWLOCK;
  wire [2:0]S_AXI_HP1_AWPROT;
  wire [3:0]S_AXI_HP1_AWQOS;
  wire S_AXI_HP1_AWREADY;
  wire [2:0]S_AXI_HP1_AWSIZE;
  wire S_AXI_HP1_AWVALID;
  wire [5:0]S_AXI_HP1_BID;
  wire S_AXI_HP1_BREADY;
  wire [1:0]S_AXI_HP1_BRESP;
  wire S_AXI_HP1_BVALID;
  wire [2:0]S_AXI_HP1_RACOUNT;
  wire [7:0]S_AXI_HP1_RCOUNT;
  wire [63:0]S_AXI_HP1_RDATA;
  wire S_AXI_HP1_RDISSUECAP1_EN;
  wire [5:0]S_AXI_HP1_RID;
  wire S_AXI_HP1_RLAST;
  wire S_AXI_HP1_RREADY;
  wire [1:0]S_AXI_HP1_RRESP;
  wire S_AXI_HP1_RVALID;
  wire [5:0]S_AXI_HP1_WACOUNT;
  wire [7:0]S_AXI_HP1_WCOUNT;
  wire [63:0]S_AXI_HP1_WDATA;
  wire [5:0]S_AXI_HP1_WID;
  wire S_AXI_HP1_WLAST;
  wire S_AXI_HP1_WREADY;
  wire S_AXI_HP1_WRISSUECAP1_EN;
  wire [7:0]S_AXI_HP1_WSTRB;
  wire S_AXI_HP1_WVALID;
  wire S_AXI_HP2_ACLK;
  wire [31:0]S_AXI_HP2_ARADDR;
  wire [1:0]S_AXI_HP2_ARBURST;
  wire [3:0]S_AXI_HP2_ARCACHE;
  wire S_AXI_HP2_ARESETN;
  wire [5:0]S_AXI_HP2_ARID;
  wire [3:0]S_AXI_HP2_ARLEN;
  wire [1:0]S_AXI_HP2_ARLOCK;
  wire [2:0]S_AXI_HP2_ARPROT;
  wire [3:0]S_AXI_HP2_ARQOS;
  wire S_AXI_HP2_ARREADY;
  wire [2:0]S_AXI_HP2_ARSIZE;
  wire S_AXI_HP2_ARVALID;
  wire [31:0]S_AXI_HP2_AWADDR;
  wire [1:0]S_AXI_HP2_AWBURST;
  wire [3:0]S_AXI_HP2_AWCACHE;
  wire [5:0]S_AXI_HP2_AWID;
  wire [3:0]S_AXI_HP2_AWLEN;
  wire [1:0]S_AXI_HP2_AWLOCK;
  wire [2:0]S_AXI_HP2_AWPROT;
  wire [3:0]S_AXI_HP2_AWQOS;
  wire S_AXI_HP2_AWREADY;
  wire [2:0]S_AXI_HP2_AWSIZE;
  wire S_AXI_HP2_AWVALID;
  wire [5:0]S_AXI_HP2_BID;
  wire S_AXI_HP2_BREADY;
  wire [1:0]S_AXI_HP2_BRESP;
  wire S_AXI_HP2_BVALID;
  wire [2:0]S_AXI_HP2_RACOUNT;
  wire [7:0]S_AXI_HP2_RCOUNT;
  wire [63:0]S_AXI_HP2_RDATA;
  wire S_AXI_HP2_RDISSUECAP1_EN;
  wire [5:0]S_AXI_HP2_RID;
  wire S_AXI_HP2_RLAST;
  wire S_AXI_HP2_RREADY;
  wire [1:0]S_AXI_HP2_RRESP;
  wire S_AXI_HP2_RVALID;
  wire [5:0]S_AXI_HP2_WACOUNT;
  wire [7:0]S_AXI_HP2_WCOUNT;
  wire [63:0]S_AXI_HP2_WDATA;
  wire [5:0]S_AXI_HP2_WID;
  wire S_AXI_HP2_WLAST;
  wire S_AXI_HP2_WREADY;
  wire S_AXI_HP2_WRISSUECAP1_EN;
  wire [7:0]S_AXI_HP2_WSTRB;
  wire S_AXI_HP2_WVALID;
  wire S_AXI_HP3_ACLK;
  wire [31:0]S_AXI_HP3_ARADDR;
  wire [1:0]S_AXI_HP3_ARBURST;
  wire [3:0]S_AXI_HP3_ARCACHE;
  wire S_AXI_HP3_ARESETN;
  wire [5:0]S_AXI_HP3_ARID;
  wire [3:0]S_AXI_HP3_ARLEN;
  wire [1:0]S_AXI_HP3_ARLOCK;
  wire [2:0]S_AXI_HP3_ARPROT;
  wire [3:0]S_AXI_HP3_ARQOS;
  wire S_AXI_HP3_ARREADY;
  wire [2:0]S_AXI_HP3_ARSIZE;
  wire S_AXI_HP3_ARVALID;
  wire [31:0]S_AXI_HP3_AWADDR;
  wire [1:0]S_AXI_HP3_AWBURST;
  wire [3:0]S_AXI_HP3_AWCACHE;
  wire [5:0]S_AXI_HP3_AWID;
  wire [3:0]S_AXI_HP3_AWLEN;
  wire [1:0]S_AXI_HP3_AWLOCK;
  wire [2:0]S_AXI_HP3_AWPROT;
  wire [3:0]S_AXI_HP3_AWQOS;
  wire S_AXI_HP3_AWREADY;
  wire [2:0]S_AXI_HP3_AWSIZE;
  wire S_AXI_HP3_AWVALID;
  wire [5:0]S_AXI_HP3_BID;
  wire S_AXI_HP3_BREADY;
  wire [1:0]S_AXI_HP3_BRESP;
  wire S_AXI_HP3_BVALID;
  wire [2:0]S_AXI_HP3_RACOUNT;
  wire [7:0]S_AXI_HP3_RCOUNT;
  wire [63:0]S_AXI_HP3_RDATA;
  wire S_AXI_HP3_RDISSUECAP1_EN;
  wire [5:0]S_AXI_HP3_RID;
  wire S_AXI_HP3_RLAST;
  wire S_AXI_HP3_RREADY;
  wire [1:0]S_AXI_HP3_RRESP;
  wire S_AXI_HP3_RVALID;
  wire [5:0]S_AXI_HP3_WACOUNT;
  wire [7:0]S_AXI_HP3_WCOUNT;
  wire [63:0]S_AXI_HP3_WDATA;
  wire [5:0]S_AXI_HP3_WID;
  wire S_AXI_HP3_WLAST;
  wire S_AXI_HP3_WREADY;
  wire S_AXI_HP3_WRISSUECAP1_EN;
  wire [7:0]S_AXI_HP3_WSTRB;
  wire S_AXI_HP3_WVALID;
  wire TRACE_CLK;
  (* RTL_KEEP = "true" *) wire \TRACE_CTL_PIPE[0] ;
  (* RTL_KEEP = "true" *) wire \TRACE_CTL_PIPE[1] ;
  (* RTL_KEEP = "true" *) wire \TRACE_CTL_PIPE[2] ;
  (* RTL_KEEP = "true" *) wire \TRACE_CTL_PIPE[3] ;
  (* RTL_KEEP = "true" *) wire \TRACE_CTL_PIPE[4] ;
  (* RTL_KEEP = "true" *) wire \TRACE_CTL_PIPE[5] ;
  (* RTL_KEEP = "true" *) wire \TRACE_CTL_PIPE[6] ;
  (* RTL_KEEP = "true" *) wire \TRACE_CTL_PIPE[7] ;
  (* RTL_KEEP = "true" *) wire [1:0]\TRACE_DATA_PIPE[0] ;
  (* RTL_KEEP = "true" *) wire [1:0]\TRACE_DATA_PIPE[1] ;
  (* RTL_KEEP = "true" *) wire [1:0]\TRACE_DATA_PIPE[2] ;
  (* RTL_KEEP = "true" *) wire [1:0]\TRACE_DATA_PIPE[3] ;
  (* RTL_KEEP = "true" *) wire [1:0]\TRACE_DATA_PIPE[4] ;
  (* RTL_KEEP = "true" *) wire [1:0]\TRACE_DATA_PIPE[5] ;
  (* RTL_KEEP = "true" *) wire [1:0]\TRACE_DATA_PIPE[6] ;
  (* RTL_KEEP = "true" *) wire [1:0]\TRACE_DATA_PIPE[7] ;
  wire TTC0_CLK0_IN;
  wire TTC0_CLK1_IN;
  wire TTC0_CLK2_IN;
  wire TTC0_WAVE0_OUT;
  wire TTC0_WAVE1_OUT;
  wire TTC0_WAVE2_OUT;
  wire TTC1_CLK0_IN;
  wire TTC1_CLK1_IN;
  wire TTC1_CLK2_IN;
  wire TTC1_WAVE0_OUT;
  wire TTC1_WAVE1_OUT;
  wire TTC1_WAVE2_OUT;
  wire UART0_CTSN;
  wire UART0_DCDN;
  wire UART0_DSRN;
  wire UART0_DTRN;
  wire UART0_RIN;
  wire UART0_RTSN;
  wire UART0_RX;
  wire UART0_TX;
  wire UART1_CTSN;
  wire UART1_DCDN;
  wire UART1_DSRN;
  wire UART1_DTRN;
  wire UART1_RIN;
  wire UART1_RTSN;
  wire UART1_RX;
  wire UART1_TX;
  wire [1:0]USB0_PORT_INDCTL;
  wire USB0_VBUS_PWRFAULT;
  wire USB0_VBUS_PWRSELECT;
  wire [1:0]USB1_PORT_INDCTL;
  wire USB1_VBUS_PWRFAULT;
  wire USB1_VBUS_PWRSELECT;
  wire WDT_CLK_IN;
  wire WDT_RST_OUT;
  wire [14:0]buffered_DDR_Addr;
  wire [2:0]buffered_DDR_BankAddr;
  wire buffered_DDR_CAS_n;
  wire buffered_DDR_CKE;
  wire buffered_DDR_CS_n;
  wire buffered_DDR_Clk;
  wire buffered_DDR_Clk_n;
  wire [3:0]buffered_DDR_DM;
  wire [31:0]buffered_DDR_DQ;
  wire [3:0]buffered_DDR_DQS;
  wire [3:0]buffered_DDR_DQS_n;
  wire buffered_DDR_DRSTB;
  wire buffered_DDR_ODT;
  wire buffered_DDR_RAS_n;
  wire buffered_DDR_VRN;
  wire buffered_DDR_VRP;
  wire buffered_DDR_WEB;
  wire [53:0]buffered_MIO;
  wire buffered_PS_CLK;
  wire buffered_PS_PORB;
  wire buffered_PS_SRSTB;
  wire [63:0]gpio_out_t_n;
  wire NLW_PS7_i_EMIOENET0GMIITXEN_UNCONNECTED;
  wire NLW_PS7_i_EMIOENET0GMIITXER_UNCONNECTED;
  wire NLW_PS7_i_EMIOENET1GMIITXEN_UNCONNECTED;
  wire NLW_PS7_i_EMIOENET1GMIITXER_UNCONNECTED;
  wire NLW_PS7_i_EMIOPJTAGTDO_UNCONNECTED;
  wire NLW_PS7_i_EMIOPJTAGTDTN_UNCONNECTED;
  wire NLW_PS7_i_EMIOTRACECTL_UNCONNECTED;
  wire [7:0]NLW_PS7_i_EMIOENET0GMIITXD_UNCONNECTED;
  wire [7:0]NLW_PS7_i_EMIOENET1GMIITXD_UNCONNECTED;
  wire [31:0]NLW_PS7_i_EMIOTRACEDATA_UNCONNECTED;
  wire [1:1]NLW_PS7_i_MAXIGP0ARCACHE_UNCONNECTED;
  wire [1:1]NLW_PS7_i_MAXIGP0AWCACHE_UNCONNECTED;
  wire [1:1]NLW_PS7_i_MAXIGP1ARCACHE_UNCONNECTED;
  wire [1:1]NLW_PS7_i_MAXIGP1AWCACHE_UNCONNECTED;
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
