dave18/EBAZ4205-Daughter-Board/Test_Code/EBAZ4205_Test5.cache/ip/2019.1.3/844bc8edf4976deb/System_processing_system7_0_0_sim_netlist.vhdl

-- Copyright 1986-2019 Xilinx, Inc. All Rights Reserved.
-- --------------------------------------------------------------------------------
-- Tool Version: Vivado v.2019.1.3 (win64) Build 2644227 Wed Sep  4 09:45:24 MDT 2019
-- Date        : Sat Jan 30 14:02:05 2021
-- Host        : DESKTOP-VR9QE9J running 64-bit major release  (build 9200)
-- Command     : write_vhdl -force -mode funcsim -rename_top decalper_eb_ot_sdeen_pot_pi_dehcac_xnilix -prefix
--               decalper_eb_ot_sdeen_pot_pi_dehcac_xnilix_ System_processing_system7_0_0_sim_netlist.vhdl
-- Design      : System_processing_system7_0_0
-- Purpose     : This VHDL netlist is a functional simulation representation of the design and should not be modified or
--               synthesized. This netlist cannot be used for SDF annotated simulation.
-- Device      : xc7z010clg400-1
-- --------------------------------------------------------------------------------
library IEEE;
use IEEE.STD_LOGIC_1164.ALL;
library UNISIM;
use UNISIM.VCOMPONENTS.ALL;
entity decalper_eb_ot_sdeen_pot_pi_dehcac_xnilix_processing_system7_v5_5_processing_system7 is
  port (
    CAN0_PHY_TX : out STD_LOGIC;
    CAN0_PHY_RX : in STD_LOGIC;
    CAN1_PHY_TX : out STD_LOGIC;
    CAN1_PHY_RX : in STD_LOGIC;
    ENET0_GMII_TX_EN : out STD_LOGIC;
    ENET0_GMII_TX_ER : out STD_LOGIC;
    ENET0_MDIO_MDC : out STD_LOGIC;
    ENET0_MDIO_O : out STD_LOGIC;
    ENET0_MDIO_T : out STD_LOGIC;
    ENET0_PTP_DELAY_REQ_RX : out STD_LOGIC;
    ENET0_PTP_DELAY_REQ_TX : out STD_LOGIC;
    ENET0_PTP_PDELAY_REQ_RX : out STD_LOGIC;
    ENET0_PTP_PDELAY_REQ_TX : out STD_LOGIC;
    ENET0_PTP_PDELAY_RESP_RX : out STD_LOGIC;
    ENET0_PTP_PDELAY_RESP_TX : out STD_LOGIC;
    ENET0_PTP_SYNC_FRAME_RX : out STD_LOGIC;
    ENET0_PTP_SYNC_FRAME_TX : out STD_LOGIC;
    ENET0_SOF_RX : out STD_LOGIC;
    ENET0_SOF_TX : out STD_LOGIC;
    ENET0_GMII_TXD : out STD_LOGIC_VECTOR ( 7 downto 0 );
    ENET0_GMII_COL : in STD_LOGIC;
    ENET0_GMII_CRS : in STD_LOGIC;
    ENET0_GMII_RX_CLK : in STD_LOGIC;
    ENET0_GMII_RX_DV : in STD_LOGIC;
    ENET0_GMII_RX_ER : in STD_LOGIC;
    ENET0_GMII_TX_CLK : in STD_LOGIC;
    ENET0_MDIO_I : in STD_LOGIC;
    ENET0_EXT_INTIN : in STD_LOGIC;
    ENET0_GMII_RXD : in STD_LOGIC_VECTOR ( 7 downto 0 );
    ENET1_GMII_TX_EN : out STD_LOGIC;
    ENET1_GMII_TX_ER : out STD_LOGIC;
    ENET1_MDIO_MDC : out STD_LOGIC;
    ENET1_MDIO_O : out STD_LOGIC;
    ENET1_MDIO_T : out STD_LOGIC;
    ENET1_PTP_DELAY_REQ_RX : out STD_LOGIC;
    ENET1_PTP_DELAY_REQ_TX : out STD_LOGIC;
    ENET1_PTP_PDELAY_REQ_RX : out STD_LOGIC;
    ENET1_PTP_PDELAY_REQ_TX : out STD_LOGIC;
    ENET1_PTP_PDELAY_RESP_RX : out STD_LOGIC;
    ENET1_PTP_PDELAY_RESP_TX : out STD_LOGIC;
    ENET1_PTP_SYNC_FRAME_RX : out STD_LOGIC;
    ENET1_PTP_SYNC_FRAME_TX : out STD_LOGIC;
    ENET1_SOF_RX : out STD_LOGIC;
    ENET1_SOF_TX : out STD_LOGIC;
    ENET1_GMII_TXD : out STD_LOGIC_VECTOR ( 7 downto 0 );
    ENET1_GMII_COL : in STD_LOGIC;
    ENET1_GMII_CRS : in STD_LOGIC;
    ENET1_GMII_RX_CLK : in STD_LOGIC;
    ENET1_GMII_RX_DV : in STD_LOGIC;
    ENET1_GMII_RX_ER : in STD_LOGIC;
    ENET1_GMII_TX_CLK : in STD_LOGIC;
    ENET1_MDIO_I : in STD_LOGIC;
    ENET1_EXT_INTIN : in STD_LOGIC;
    ENET1_GMII_RXD : in STD_LOGIC_VECTOR ( 7 downto 0 );
    GPIO_I : in STD_LOGIC_VECTOR ( 63 downto 0 );
    GPIO_O : out STD_LOGIC_VECTOR ( 63 downto 0 );
    GPIO_T : out STD_LOGIC_VECTOR ( 63 downto 0 );
    I2C0_SDA_I : in STD_LOGIC;
    I2C0_SDA_O : out STD_LOGIC;
    I2C0_SDA_T : out STD_LOGIC;
    I2C0_SCL_I : in STD_LOGIC;
    I2C0_SCL_O : out STD_LOGIC;
    I2C0_SCL_T : out STD_LOGIC;
    I2C1_SDA_I : in STD_LOGIC;
    I2C1_SDA_O : out STD_LOGIC;
    I2C1_SDA_T : out STD_LOGIC;
    I2C1_SCL_I : in STD_LOGIC;
    I2C1_SCL_O : out STD_LOGIC;
    I2C1_SCL_T : out STD_LOGIC;
    PJTAG_TCK : in STD_LOGIC;
    PJTAG_TMS : in STD_LOGIC;
    PJTAG_TDI : in STD_LOGIC;
    PJTAG_TDO : out STD_LOGIC;
    SDIO0_CLK : out STD_LOGIC;
    SDIO0_CLK_FB : in STD_LOGIC;
    SDIO0_CMD_O : out STD_LOGIC;
    SDIO0_CMD_I : in STD_LOGIC;
    SDIO0_CMD_T : out STD_LOGIC;
    SDIO0_DATA_I : in STD_LOGIC_VECTOR ( 3 downto 0 );
    SDIO0_DATA_O : out STD_LOGIC_VECTOR ( 3 downto 0 );
    SDIO0_DATA_T : out STD_LOGIC_VECTOR ( 3 downto 0 );
    SDIO0_LED : out STD_LOGIC;
    SDIO0_CDN : in STD_LOGIC;
    SDIO0_WP : in STD_LOGIC;
    SDIO0_BUSPOW : out STD_LOGIC;
    SDIO0_BUSVOLT : out STD_LOGIC_VECTOR ( 2 downto 0 );
    SDIO1_CLK : out STD_LOGIC;
    SDIO1_CLK_FB : in STD_LOGIC;
    SDIO1_CMD_O : out STD_LOGIC;
    SDIO1_CMD_I : in STD_LOGIC;
    SDIO1_CMD_T : out STD_LOGIC;
    SDIO1_DATA_I : in STD_LOGIC_VECTOR ( 3 downto 0 );
    SDIO1_DATA_O : out STD_LOGIC_VECTOR ( 3 downto 0 );
    SDIO1_DATA_T : out STD_LOGIC_VECTOR ( 3 downto 0 );
    SDIO1_LED : out STD_LOGIC;
    SDIO1_CDN : in STD_LOGIC;
    SDIO1_WP : in STD_LOGIC;
    SDIO1_BUSPOW : out STD_LOGIC;
    SDIO1_BUSVOLT : out STD_LOGIC_VECTOR ( 2 downto 0 );
    SPI0_SCLK_I : in STD_LOGIC;
    SPI0_SCLK_O : out STD_LOGIC;
    SPI0_SCLK_T : out STD_LOGIC;
    SPI0_MOSI_I : in STD_LOGIC;
    SPI0_MOSI_O : out STD_LOGIC;
    SPI0_MOSI_T : out STD_LOGIC;
    SPI0_MISO_I : in STD_LOGIC;
    SPI0_MISO_O : out STD_LOGIC;
    SPI0_MISO_T : out STD_LOGIC;
    SPI0_SS_I : in STD_LOGIC;
    SPI0_SS_O : out STD_LOGIC;
    SPI0_SS1_O : out STD_LOGIC;
    SPI0_SS2_O : out STD_LOGIC;
    SPI0_SS_T : out STD_LOGIC;
    SPI1_SCLK_I : in STD_LOGIC;
    SPI1_SCLK_O : out STD_LOGIC;
    SPI1_SCLK_T : out STD_LOGIC;
    SPI1_MOSI_I : in STD_LOGIC;
    SPI1_MOSI_O : out STD_LOGIC;
    SPI1_MOSI_T : out STD_LOGIC;
    SPI1_MISO_I : in STD_LOGIC;
    SPI1_MISO_O : out STD_LOGIC;
    SPI1_MISO_T : out STD_LOGIC;
    SPI1_SS_I : in STD_LOGIC;
    SPI1_SS_O : out STD_LOGIC;
    SPI1_SS1_O : out STD_LOGIC;
    SPI1_SS2_O : out STD_LOGIC;
    SPI1_SS_T : out STD_LOGIC;
    UART0_DTRN : out STD_LOGIC;
    UART0_RTSN : out STD_LOGIC;
    UART0_TX : out STD_LOGIC;
    UART0_CTSN : in STD_LOGIC;
    UART0_DCDN : in STD_LOGIC;
    UART0_DSRN : in STD_LOGIC;
    UART0_RIN : in STD_LOGIC;
    UART0_RX : in STD_LOGIC;
    UART1_DTRN : out STD_LOGIC;
    UART1_RTSN : out STD_LOGIC;
    UART1_TX : out STD_LOGIC;
    UART1_CTSN : in STD_LOGIC;
    UART1_DCDN : in STD_LOGIC;
    UART1_DSRN : in STD_LOGIC;
    UART1_RIN : in STD_LOGIC;
    UART1_RX : in STD_LOGIC;
    TTC0_WAVE0_OUT : out STD_LOGIC;
    TTC0_WAVE1_OUT : out STD_LOGIC;
    TTC0_WAVE2_OUT : out STD_LOGIC;
    TTC0_CLK0_IN : in STD_LOGIC;
    TTC0_CLK1_IN : in STD_LOGIC;
    TTC0_CLK2_IN : in STD_LOGIC;
    TTC1_WAVE0_OUT : out STD_LOGIC;
    TTC1_WAVE1_OUT : out STD_LOGIC;
    TTC1_WAVE2_OUT : out STD_LOGIC;
    TTC1_CLK0_IN : in STD_LOGIC;
    TTC1_CLK1_IN : in STD_LOGIC;
    TTC1_CLK2_IN : in STD_LOGIC;
    WDT_CLK_IN : in STD_LOGIC;
    WDT_RST_OUT : out STD_LOGIC;
    TRACE_CLK : in STD_LOGIC;
    TRACE_CTL : out STD_LOGIC;
    TRACE_DATA : out STD_LOGIC_VECTOR ( 1 downto 0 );
    TRACE_CLK_OUT : out STD_LOGIC;
    USB0_PORT_INDCTL : out STD_LOGIC_VECTOR ( 1 downto 0 );
    USB0_VBUS_PWRSELECT : out STD_LOGIC;
    USB0_VBUS_PWRFAULT : in STD_LOGIC;
    USB1_PORT_INDCTL : out STD_LOGIC_VECTOR ( 1 downto 0 );
    USB1_VBUS_PWRSELECT : out STD_LOGIC;
    USB1_VBUS_PWRFAULT : in STD_LOGIC;
    SRAM_INTIN : in STD_LOGIC;
    M_AXI_GP0_ARESETN : out STD_LOGIC;
    M_AXI_GP0_ARVALID : out STD_LOGIC;
    M_AXI_GP0_AWVALID : out STD_LOGIC;
    M_AXI_GP0_BREADY : out STD_LOGIC;
    M_AXI_GP0_RREADY : out STD_LOGIC;
    M_AXI_GP0_WLAST : out STD_LOGIC;
    M_AXI_GP0_WVALID : out STD_LOGIC;
    M_AXI_GP0_ARID : out STD_LOGIC_VECTOR ( 11 downto 0 );
    M_AXI_GP0_AWID : out STD_LOGIC_VECTOR ( 11 downto 0 );
    M_AXI_GP0_WID : out STD_LOGIC_VECTOR ( 11 downto 0 );
    M_AXI_GP0_ARBURST : out STD_LOGIC_VECTOR ( 1 downto 0 );
    M_AXI_GP0_ARLOCK : out STD_LOGIC_VECTOR ( 1 downto 0 );
    M_AXI_GP0_ARSIZE : out STD_LOGIC_VECTOR ( 2 downto 0 );
    M_AXI_GP0_AWBURST : out STD_LOGIC_VECTOR ( 1 downto 0 );
    M_AXI_GP0_AWLOCK : out STD_LOGIC_VECTOR ( 1 downto 0 );
    M_AXI_GP0_AWSIZE : out STD_LOGIC_VECTOR ( 2 downto 0 );
    M_AXI_GP0_ARPROT : out STD_LOGIC_VECTOR ( 2 downto 0 );
    M_AXI_GP0_AWPROT : out STD_LOGIC_VECTOR ( 2 downto 0 );
    M_AXI_GP0_ARADDR : out STD_LOGIC_VECTOR ( 31 downto 0 );
    M_AXI_GP0_AWADDR : out STD_LOGIC_VECTOR ( 31 downto 0 );
    M_AXI_GP0_WDATA : out STD_LOGIC_VECTOR ( 31 downto 0 );
    M_AXI_GP0_ARCACHE : out STD_LOGIC_VECTOR ( 3 downto 0 );
    M_AXI_GP0_ARLEN : out STD_LOGIC_VECTOR ( 3 downto 0 );
    M_AXI_GP0_ARQOS : out STD_LOGIC_VECTOR ( 3 downto 0 );
    M_AXI_GP0_AWCACHE : out STD_LOGIC_VECTOR ( 3 downto 0 );
    M_AXI_GP0_AWLEN : out STD_LOGIC_VECTOR ( 3 downto 0 );
    M_AXI_GP0_AWQOS : out STD_LOGIC_VECTOR ( 3 downto 0 );
    M_AXI_GP0_WSTRB : out STD_LOGIC_VECTOR ( 3 downto 0 );
    M_AXI_GP0_ACLK : in STD_LOGIC;
    M_AXI_GP0_ARREADY : in STD_LOGIC;
    M_AXI_GP0_AWREADY : in STD_LOGIC;
    M_AXI_GP0_BVALID : in STD_LOGIC;
    M_AXI_GP0_RLAST : in STD_LOGIC;
    M_AXI_GP0_RVALID : in STD_LOGIC;
    M_AXI_GP0_WREADY : in STD_LOGIC;
    M_AXI_GP0_BID : in STD_LOGIC_VECTOR ( 11 downto 0 );
    M_AXI_GP0_RID : in STD_LOGIC_VECTOR ( 11 downto 0 );
    M_AXI_GP0_BRESP : in STD_LOGIC_VECTOR ( 1 downto 0 );
    M_AXI_GP0_RRESP : in STD_LOGIC_VECTOR ( 1 downto 0 );
    M_AXI_GP0_RDATA : in STD_LOGIC_VECTOR ( 31 downto 0 );
    M_AXI_GP1_ARESETN : out STD_LOGIC;
    M_AXI_GP1_ARVALID : out STD_LOGIC;
    M_AXI_GP1_AWVALID : out STD_LOGIC;
    M_AXI_GP1_BREADY : out STD_LOGIC;
    M_AXI_GP1_RREADY : out STD_LOGIC;
    M_AXI_GP1_WLAST : out STD_LOGIC;
    M_AXI_GP1_WVALID : out STD_LOGIC;
    M_AXI_GP1_ARID : out STD_LOGIC_VECTOR ( 11 downto 0 );
    M_AXI_GP1_AWID : out STD_LOGIC_VECTOR ( 11 downto 0 );
    M_AXI_GP1_WID : out STD_LOGIC_VECTOR ( 11 downto 0 );
    M_AXI_GP1_ARBURST : out STD_LOGIC_VECTOR ( 1 downto 0 );
    M_AXI_GP1_ARLOCK : out STD_LOGIC_VECTOR ( 1 downto 0 );
    M_AXI_GP1_ARSIZE : out STD_LOGIC_VECTOR ( 2 downto 0 );
    M_AXI_GP1_AWBURST : out STD_LOGIC_VECTOR ( 1 downto 0 );
    M_AXI_GP1_AWLOCK : out STD_LOGIC_VECTOR ( 1 downto 0 );
    M_AXI_GP1_AWSIZE : out STD_LOGIC_VECTOR ( 2 downto 0 );
    M_AXI_GP1_ARPROT : out STD_LOGIC_VECTOR ( 2 downto 0 );
    M_AXI_GP1_AWPROT : out STD_LOGIC_VECTOR ( 2 downto 0 );
    M_AXI_GP1_ARADDR : out STD_LOGIC_VECTOR ( 31 downto 0 );
    M_AXI_GP1_AWADDR : out STD_LOGIC_VECTOR ( 31 downto 0 );
    M_AXI_GP1_WDATA : out STD_LOGIC_VECTOR ( 31 downto 0 );
    M_AXI_GP1_ARCACHE : out STD_LOGIC_VECTOR ( 3 downto 0 );
    M_AXI_GP1_ARLEN : out STD_LOGIC_VECTOR ( 3 downto 0 );
    M_AXI_GP1_ARQOS : out STD_LOGIC_VECTOR ( 3 downto 0 );
    M_AXI_GP1_AWCACHE : out STD_LOGIC_VECTOR ( 3 downto 0 );
    M_AXI_GP1_AWLEN : out STD_LOGIC_VECTOR ( 3 downto 0 );
    M_AXI_GP1_AWQOS : out STD_LOGIC_VECTOR ( 3 downto 0 );
    M_AXI_GP1_WSTRB : out STD_LOGIC_VECTOR ( 3 downto 0 );
    M_AXI_GP1_ACLK : in STD_LOGIC;
    M_AXI_GP1_ARREADY : in STD_LOGIC;
    M_AXI_GP1_AWREADY : in STD_LOGIC;
    M_AXI_GP1_BVALID : in STD_LOGIC;
    M_AXI_GP1_RLAST : in STD_LOGIC;
    M_AXI_GP1_RVALID : in STD_LOGIC;
    M_AXI_GP1_WREADY : in STD_LOGIC;
    M_AXI_GP1_BID : in STD_LOGIC_VECTOR ( 11 downto 0 );
    M_AXI_GP1_RID : in STD_LOGIC_VECTOR ( 11 downto 0 );
    M_AXI_GP1_BRESP : in STD_LOGIC_VECTOR ( 1 downto 0 );
    M_AXI_GP1_RRESP : in STD_LOGIC_VECTOR ( 1 downto 0 );
    M_AXI_GP1_RDATA : in STD_LOGIC_VECTOR ( 31 downto 0 );
    S_AXI_GP0_ARESETN : out STD_LOGIC;
    S_AXI_GP0_ARREADY : out STD_LOGIC;
    S_AXI_GP0_AWREADY : out STD_LOGIC;
    S_AXI_GP0_BVALID : out STD_LOGIC;
    S_AXI_GP0_RLAST : out STD_LOGIC;
    S_AXI_GP0_RVALID : out STD_LOGIC;
    S_AXI_GP0_WREADY : out STD_LOGIC;
    S_AXI_GP0_BRESP : out STD_LOGIC_VECTOR ( 1 downto 0 );
    S_AXI_GP0_RRESP : out STD_LOGIC_VECTOR ( 1 downto 0 );
    S_AXI_GP0_RDATA : out STD_LOGIC_VECTOR ( 31 downto 0 );
    S_AXI_GP0_BID : out STD_LOGIC_VECTOR ( 5 downto 0 );
    S_AXI_GP0_RID : out STD_LOGIC_VECTOR ( 5 downto 0 );
    S_AXI_GP0_ACLK : in STD_LOGIC;
    S_AXI_GP0_ARVALID : in STD_LOGIC;
    S_AXI_GP0_AWVALID : in STD_LOGIC;
    S_AXI_GP0_BREADY : in STD_LOGIC;
    S_AXI_GP0_RREADY : in STD_LOGIC;
    S_AXI_GP0_WLAST : in STD_LOGIC;
    S_AXI_GP0_WVALID : in STD_LOGIC;
    S_AXI_GP0_ARBURST : in STD_LOGIC_VECTOR ( 1 downto 0 );
    S_AXI_GP0_ARLOCK : in STD_LOGIC_VECTOR ( 1 downto 0 );
    S_AXI_GP0_ARSIZE : in STD_LOGIC_VECTOR ( 2 downto 0 );
    S_AXI_GP0_AWBURST : in STD_LOGIC_VECTOR ( 1 downto 0 );
    S_AXI_GP0_AWLOCK : in STD_LOGIC_VECTOR ( 1 downto 0 );
    S_AXI_GP0_AWSIZE : in STD_LOGIC_VECTOR ( 2 downto 0 );
    S_AXI_GP0_ARPROT : in STD_LOGIC_VECTOR ( 2 downto 0 );
    S_AXI_GP0_AWPROT : in STD_LOGIC_VECTOR ( 2 downto 0 );
    S_AXI_GP0_ARADDR : in STD_LOGIC_VECTOR ( 31 downto 0 );
    S_AXI_GP0_AWADDR : in STD_LOGIC_VECTOR ( 31 downto 0 );
    S_AXI_GP0_WDATA : in STD_LOGIC_VECTOR ( 31 downto 0 );
    S_AXI_GP0_ARCACHE : in STD_LOGIC_VECTOR ( 3 downto 0 );
    S_AXI_GP0_ARLEN : in STD_LOGIC_VECTOR ( 3 downto 0 );
    S_AXI_GP0_ARQOS : in STD_LOGIC_VECTOR ( 3 downto 0 );
    S_AXI_GP0_AWCACHE : in STD_LOGIC_VECTOR ( 3 downto 0 );
    S_AXI_GP0_AWLEN : in STD_LOGIC_VECTOR ( 3 downto 0 );
    S_AXI_GP0_AWQOS : in STD_LOGIC_VECTOR ( 3 downto 0 );
    S_AXI_GP0_WSTRB : in STD_LOGIC_VECTOR ( 3 downto 0 );
    S_AXI_GP0_ARID : in STD_LOGIC_VECTOR ( 5 downto 0 );
    S_AXI_GP0_AWID : in STD_LOGIC_VECTOR ( 5 downto 0 );
    S_AXI_GP0_WID : in STD_LOGIC_VECTOR ( 5 downto 0 );
    S_AXI_GP1_ARESETN : out STD_LOGIC;
    S_AXI_GP1_ARREADY : out STD_LOGIC;
    S_AXI_GP1_AWREADY : out STD_LOGIC;
    S_AXI_GP1_BVALID : out STD_LOGIC;
    S_AXI_GP1_RLAST : out STD_LOGIC;
    S_AXI_GP1_RVALID : out STD_LOGIC;
    S_AXI_GP1_WREADY : out STD_LOGIC;
    S_AXI_GP1_BRESP : out STD_LOGIC_VECTOR ( 1 downto 0 );
    S_AXI_GP1_RRESP : out STD_LOGIC_VECTOR ( 1 downto 0 );
    S_AXI_GP1_RDATA : out STD_LOGIC_VECTOR ( 31 downto 0 );
    S_AXI_GP1_BID : out STD_LOGIC_VECTOR ( 5 downto 0 );
    S_AXI_GP1_RID : out STD_LOGIC_VECTOR ( 5 downto 0 );
    S_AXI_GP1_ACLK : in STD_LOGIC;
    S_AXI_GP1_ARVALID : in STD_LOGIC;
    S_AXI_GP1_AWVALID : in STD_LOGIC;
    S_AXI_GP1_BREADY : in STD_LOGIC;
    S_AXI_GP1_RREADY : in STD_LOGIC;
    S_AXI_GP1_WLAST : in STD_LOGIC;
    S_AXI_GP1_WVALID : in STD_LOGIC;
    S_AXI_GP1_ARBURST : in STD_LOGIC_VECTOR ( 1 downto 0 );
    S_AXI_GP1_ARLOCK : in STD_LOGIC_VECTOR ( 1 downto 0 );
    S_AXI_GP1_ARSIZE : in STD_LOGIC_VECTOR ( 2 downto 0 );
    S_AXI_GP1_AWBURST : in STD_LOGIC_VECTOR ( 1 downto 0 );
    S_AXI_GP1_AWLOCK : in STD_LOGIC_VECTOR ( 1 downto 0 );
    S_AXI_GP1_AWSIZE : in STD_LOGIC_VECTOR ( 2 downto 0 );
    S_AXI_GP1_ARPROT : in STD_LOGIC_VECTOR ( 2 downto 0 );
    S_AXI_GP1_AWPROT : in STD_LOGIC_VECTOR ( 2 downto 0 );
    S_AXI_GP1_ARADDR : in STD_LOGIC_VECTOR ( 31 downto 0 );
    S_AXI_GP1_AWADDR : in STD_LOGIC_VECTOR ( 31 downto 0 );
    S_AXI_GP1_WDATA : in STD_LOGIC_VECTOR ( 31 downto 0 );
    S_AXI_GP1_ARCACHE : in STD_LOGIC_VECTOR ( 3 downto 0 );
    S_AXI_GP1_ARLEN : in STD_LOGIC_VECTOR ( 3 downto 0 );
    S_AXI_GP1_ARQOS : in STD_LOGIC_VECTOR ( 3 downto 0 );
    S_AXI_GP1_AWCACHE : in STD_LOGIC_VECTOR ( 3 downto 0 );
    S_AXI_GP1_AWLEN : in STD_LOGIC_VECTOR ( 3 downto 0 );
    S_AXI_GP1_AWQOS : in STD_LOGIC_VECTOR ( 3 downto 0 );
    S_AXI_GP1_WSTRB : in STD_LOGIC_VECTOR ( 3 downto 0 );
    S_AXI_GP1_ARID : in STD_LOGIC_VECTOR ( 5 downto 0 );
    S_AXI_GP1_AWID : in STD_LOGIC_VECTOR ( 5 downto 0 );
    S_AXI_GP1_WID : in STD_LOGIC_VECTOR ( 5 downto 0 );
    S_AXI_ACP_ARESETN : out STD_LOGIC;
    S_AXI_ACP_ARREADY : out STD_LOGIC;
    S_AXI_ACP_AWREADY : out STD_LOGIC;
    S_AXI_ACP_BVALID : out STD_LOGIC;
    S_AXI_ACP_RLAST : out STD_LOGIC;
    S_AXI_ACP_RVALID : out STD_LOGIC;
    S_AXI_ACP_WREADY : out STD_LOGIC;
    S_AXI_ACP_BRESP : out STD_LOGIC_VECTOR ( 1 downto 0 );
    S_AXI_ACP_RRESP : out STD_LOGIC_VECTOR ( 1 downto 0 );
    S_AXI_ACP_BID : out STD_LOGIC_VECTOR ( 2 downto 0 );
    S_AXI_ACP_RID : out STD_LOGIC_VECTOR ( 2 downto 0 );
    S_AXI_ACP_RDATA : out STD_LOGIC_VECTOR ( 63 downto 0 );
    S_AXI_ACP_ACLK : in STD_LOGIC;
    S_AXI_ACP_ARVALID : in STD_LOGIC;
    S_AXI_ACP_AWVALID : in STD_LOGIC;
    S_AXI_ACP_BREADY : in STD_LOGIC;
    S_AXI_ACP_RREADY : in STD_LOGIC;
    S_AXI_ACP_WLAST : in STD_LOGIC;
    S_AXI_ACP_WVALID : in STD_LOGIC;
    S_AXI_ACP_ARID : in STD_LOGIC_VECTOR ( 2 downto 0 );
    S_AXI_ACP_ARPROT : in STD_LOGIC_VECTOR ( 2 downto 0 );
    S_AXI_ACP_AWID : in STD_LOGIC_VECTOR ( 2 downto 0 );
    S_AXI_ACP_AWPROT : in STD_LOGIC_VECTOR ( 2 downto 0 );
    S_AXI_ACP_WID : in STD_LOGIC_VECTOR ( 2 downto 0 );
    S_AXI_ACP_ARADDR : in STD_LOGIC_VECTOR ( 31 downto 0 );
    S_AXI_ACP_AWADDR : in STD_LOGIC_VECTOR ( 31 downto 0 );
    S_AXI_ACP_ARCACHE : in STD_LOGIC_VECTOR ( 3 downto 0 );
    S_AXI_ACP_ARLEN : in STD_LOGIC_VECTOR ( 3 downto 0 );
    S_AXI_ACP_ARQOS : in STD_LOGIC_VECTOR ( 3 downto 0 );
    S_AXI_ACP_AWCACHE : in STD_LOGIC_VECTOR ( 3 downto 0 );
    S_AXI_ACP_AWLEN : in STD_LOGIC_VECTOR ( 3 downto 0 );
    S_AXI_ACP_AWQOS : in STD_LOGIC_VECTOR ( 3 downto 0 );
    S_AXI_ACP_ARBURST : in STD_LOGIC_VECTOR ( 1 downto 0 );
    S_AXI_ACP_ARLOCK : in STD_LOGIC_VECTOR ( 1 downto 0 );
    S_AXI_ACP_ARSIZE : in STD_LOGIC_VECTOR ( 2 downto 0 );
    S_AXI_ACP_AWBURST : in STD_LOGIC_VECTOR ( 1 downto 0 );
    S_AXI_ACP_AWLOCK : in STD_LOGIC_VECTOR ( 1 downto 0 );
    S_AXI_ACP_AWSIZE : in STD_LOGIC_VECTOR ( 2 downto 0 );
    S_AXI_ACP_ARUSER : in STD_LOGIC_VECTOR ( 4 downto 0 );
    S_AXI_ACP_AWUSER : in STD_LOGIC_VECTOR ( 4 downto 0 );
    S_AXI_ACP_WDATA : in STD_LOGIC_VECTOR ( 63 downto 0 );
    S_AXI_ACP_WSTRB : in STD_LOGIC_VECTOR ( 7 downto 0 );
    S_AXI_HP0_ARESETN : out STD_LOGIC;
    S_AXI_HP0_ARREADY : out STD_LOGIC;
    S_AXI_HP0_AWREADY : out STD_LOGIC;
    S_AXI_HP0_BVALID : out STD_LOGIC;
    S_AXI_HP0_RLAST : out STD_LOGIC;
    S_AXI_HP0_RVALID : out STD_LOGIC;
    S_AXI_HP0_WREADY : out STD_LOGIC;
    S_AXI_HP0_BRESP : out STD_LOGIC_VECTOR ( 1 downto 0 );
    S_AXI_HP0_RRESP : out STD_LOGIC_VECTOR ( 1 downto 0 );
    S_AXI_HP0_BID : out STD_LOGIC_VECTOR ( 5 downto 0 );
    S_AXI_HP0_RID : out STD_LOGIC_VECTOR ( 5 downto 0 );
    S_AXI_HP0_RDATA : out STD_LOGIC_VECTOR ( 63 downto 0 );
    S_AXI_HP0_RCOUNT : out STD_LOGIC_VECTOR ( 7 downto 0 );
    S_AXI_HP0_WCOUNT : out STD_LOGIC_VECTOR ( 7 downto 0 );
    S_AXI_HP0_RACOUNT : out STD_LOGIC_VECTOR ( 2 downto 0 );
    S_AXI_HP0_WACOUNT : out STD_LOGIC_VECTOR ( 5 downto 0 );
    S_AXI_HP0_ACLK : in STD_LOGIC;
    S_AXI_HP0_ARVALID : in STD_LOGIC;
    S_AXI_HP0_AWVALID : in STD_LOGIC;
    S_AXI_HP0_BREADY : in STD_LOGIC;
    S_AXI_HP0_RDISSUECAP1_EN : in STD_LOGIC;
    S_AXI_HP0_RREADY : in STD_LOGIC;
    S_AXI_HP0_WLAST : in STD_LOGIC;
    S_AXI_HP0_WRISSUECAP1_EN : in STD_LOGIC;
    S_AXI_HP0_WVALID : in STD_LOGIC;
    S_AXI_HP0_ARBURST : in STD_LOGIC_VECTOR ( 1 downto 0 );
    S_AXI_HP0_ARLOCK : in STD_LOGIC_VECTOR ( 1 downto 0 );
    S_AXI_HP0_ARSIZE : in STD_LOGIC_VECTOR ( 2 downto 0 );
    S_AXI_HP0_AWBURST : in STD_LOGIC_VECTOR ( 1 downto 0 );
    S_AXI_HP0_AWLOCK : in STD_LOGIC_VECTOR ( 1 downto 0 );
    S_AXI_HP0_AWSIZE : in STD_LOGIC_VECTOR ( 2 downto 0 );
    S_AXI_HP0_ARPROT : in STD_LOGIC_VECTOR ( 2 downto 0 );
    S_AXI_HP0_AWPROT : in STD_LOGIC_VECTOR ( 2 downto 0 );
    S_AXI_HP0_ARADDR : in STD_LOGIC_VECTOR ( 31 downto 0 );
    S_AXI_HP0_AWADDR : in STD_LOGIC_VECTOR ( 31 downto 0 );
    S_AXI_HP0_ARCACHE : in STD_LOGIC_VECTOR ( 3 downto 0 );
    S_AXI_HP0_ARLEN : in STD_LOGIC_VECTOR ( 3 downto 0 );
    S_AXI_HP0_ARQOS : in STD_LOGIC_VECTOR ( 3 downto 0 );
    S_AXI_HP0_AWCACHE : in STD_LOGIC_VECTOR ( 3 downto 0 );
    S_AXI_HP0_AWLEN : in STD_LOGIC_VECTOR ( 3 downto 0 );
    S_AXI_HP0_AWQOS : in STD_LOGIC_VECTOR ( 3 downto 0 );
    S_AXI_HP0_ARID : in STD_LOGIC_VECTOR ( 5 downto 0 );
    S_AXI_HP0_AWID : in STD_LOGIC_VECTOR ( 5 downto 0 );
    S_AXI_HP0_WID : in STD_LOGIC_VECTOR ( 5 downto 0 );
    S_AXI_HP0_WDATA : in STD_LOGIC_VECTOR ( 63 downto 0 );
    S_AXI_HP0_WSTRB : in STD_LOGIC_VECTOR ( 7 downto 0 );
    S_AXI_HP1_ARESETN : out STD_LOGIC;
    S_AXI_HP1_ARREADY : out STD_LOGIC;
    S_AXI_HP1_AWREADY : out STD_LOGIC;
    S_AXI_HP1_BVALID : out STD_LOGIC;
    S_AXI_HP1_RLAST : out STD_LOGIC;
    S_AXI_HP1_RVALID : out STD_LOGIC;
    S_AXI_HP1_WREADY : out STD_LOGIC;
    S_AXI_HP1_BRESP : out STD_LOGIC_VECTOR ( 1 downto 0 );
    S_AXI_HP1_RRESP : out STD_LOGIC_VECTOR ( 1 downto 0 );
    S_AXI_HP1_BID : out STD_LOGIC_VECTOR ( 5 downto 0 );
    S_AXI_HP1_RID : out STD_LOGIC_VECTOR ( 5 downto 0 );
    S_AXI_HP1_RDATA : out STD_LOGIC_VECTOR ( 63 downto 0 );
    S_AXI_HP1_RCOUNT : out STD_LOGIC_VECTOR ( 7 downto 0 );
    S_AXI_HP1_WCOUNT : out STD_LOGIC_VECTOR ( 7 downto 0 );
    S_AXI_HP1_RACOUNT : out STD_LOGIC_VECTOR ( 2 downto 0 );
    S_AXI_HP1_WACOUNT : out STD_LOGIC_VECTOR ( 5 downto 0 );
    S_AXI_HP1_ACLK : in STD_LOGIC;
    S_AXI_HP1_ARVALID : in STD_LOGIC;
    S_AXI_HP1_AWVALID : in STD_LOGIC;
    S_AXI_HP1_BREADY : in STD_LOGIC;
    S_AXI_HP1_RDISSUECAP1_EN : in STD_LOGIC;
    S_AXI_HP1_RREADY : in STD_LOGIC;
    S_AXI_HP1_WLAST : in STD_LOGIC;
    S_AXI_HP1_WRISSUECAP1_EN : in STD_LOGIC;
    S_AXI_HP1_WVALID : in STD_LOGIC;
    S_AXI_HP1_ARBURST : in STD_LOGIC_VECTOR ( 1 downto 0 );
    S_AXI_HP1_ARLOCK : in STD_LOGIC_VECTOR ( 1 downto 0 );
    S_AXI_HP1_ARSIZE : in STD_LOGIC_VECTOR ( 2 downto 0 );
    S_AXI_HP1_AWBURST : in STD_LOGIC_VECTOR ( 1 downto 0 );
    S_AXI_HP1_AWLOCK : in STD_LOGIC_VECTOR ( 1 downto 0 );
    S_AXI_HP1_AWSIZE : in STD_LOGIC_VECTOR ( 2 downto 0 );
    S_AXI_HP1_ARPROT : in STD_LOGIC_VECTOR ( 2 downto 0 );
    S_AXI_HP1_AWPROT : in STD_LOGIC_VECTOR ( 2 downto 0 );
    S_AXI_HP1_ARADDR : in STD_LOGIC_VECTOR ( 31 downto 0 );
    S_AXI_HP1_AWADDR : in STD_LOGIC_VECTOR ( 31 downto 0 );
    S_AXI_HP1_ARCACHE : in STD_LOGIC_VECTOR ( 3 downto 0 );
    S_AXI_HP1_ARLEN : in STD_LOGIC_VECTOR ( 3 downto 0 );
    S_AXI_HP1_ARQOS : in STD_LOGIC_VECTOR ( 3 downto 0 );
    S_AXI_HP1_AWCACHE : in STD_LOGIC_VECTOR ( 3 downto 0 );
    S_AXI_HP1_AWLEN : in STD_LOGIC_VECTOR ( 3 downto 0 );
    S_AXI_HP1_AWQOS : in STD_LOGIC_VECTOR ( 3 downto 0 );
    S_AXI_HP1_ARID : in STD_LOGIC_VECTOR ( 5 downto 0 );
    S_AXI_HP1_AWID : in STD_LOGIC_VECTOR ( 5 downto 0 );
    S_AXI_HP1_WID : in STD_LOGIC_VECTOR ( 5 downto 0 );
    S_AXI_HP1_WDATA : in STD_LOGIC_VECTOR ( 63 downto 0 );
    S_AXI_HP1_WSTRB : in STD_LOGIC_VECTOR ( 7 downto 0 );
    S_AXI_HP2_ARESETN : out STD_LOGIC;
    S_AXI_HP2_ARREADY : out STD_LOGIC;
    S_AXI_HP2_AWREADY : out STD_LOGIC;
    S_AXI_HP2_BVALID : out STD_LOGIC;
    S_AXI_HP2_RLAST : out STD_LOGIC;
    S_AXI_HP2_RVALID : out STD_LOGIC;
    S_AXI_HP2_WREADY : out STD_LOGIC;
    S_AXI_HP2_BRESP : out STD_LOGIC_VECTOR ( 1 downto 0 );
    S_AXI_HP2_RRESP : out STD_LOGIC_VECTOR ( 1 downto 0 );
    S_AXI_HP2_BID : out STD_LOGIC_VECTOR ( 5 downto 0 );
    S_AXI_HP2_RID : out STD_LOGIC_VECTOR ( 5 downto 0 );
    S_AXI_HP2_RDATA : out STD_LOGIC_VECTOR ( 63 downto 0 );
    S_AXI_HP2_RCOUNT : out STD_LOGIC_VECTOR ( 7 downto 0 );
    S_AXI_HP2_WCOUNT : out STD_LOGIC_VECTOR ( 7 downto 0 );
    S_AXI_HP2_RACOUNT : out STD_LOGIC_VECTOR ( 2 downto 0 );
    S_AXI_HP2_WACOUNT : out STD_LOGIC_VECTOR ( 5 downto 0 );
    S_AXI_HP2_ACLK : in STD_LOGIC;
    S_AXI_HP2_ARVALID : in STD_LOGIC;
    S_AXI_HP2_AWVALID : in STD_LOGIC;
    S_AXI_HP2_BREADY : in STD_LOGIC;
    S_AXI_HP2_RDISSUECAP1_EN : in STD_LOGIC;
    S_AXI_HP2_RREADY : in STD_LOGIC;
    S_AXI_HP2_WLAST : in STD_LOGIC;
    S_AXI_HP2_WRISSUECAP1_EN : in STD_LOGIC;
    S_AXI_HP2_WVALID : in STD_LOGIC;
    S_AXI_HP2_ARBURST : in STD_LOGIC_VECTOR ( 1 downto 0 );
    S_AXI_HP2_ARLOCK : in STD_LOGIC_VECTOR ( 1 downto 0 );
    S_AXI_HP2_ARSIZE : in STD_LOGIC_VECTOR ( 2 downto 0 );
    S_AXI_HP2_AWBURST : in STD_LOGIC_VECTOR ( 1 downto 0 );
    S_AXI_HP2_AWLOCK : in STD_LOGIC_VECTOR ( 1 downto 0 );
    S_AXI_HP2_AWSIZE : in STD_LOGIC_VECTOR ( 2 downto 0 );
    S_AXI_HP2_ARPROT : in STD_LOGIC_VECTOR ( 2 downto 0 );
    S_AXI_HP2_AWPROT : in STD_LOGIC_VECTOR ( 2 downto 0 );
    S_AXI_HP2_ARADDR : in STD_LOGIC_VECTOR ( 31 downto 0 );
    S_AXI_HP2_AWADDR : in STD_LOGIC_VECTOR ( 31 downto 0 );
    S_AXI_HP2_ARCACHE : in STD_LOGIC_VECTOR ( 3 downto 0 );
    S_AXI_HP2_ARLEN : in STD_LOGIC_VECTOR ( 3 downto 0 );
    S_AXI_HP2_ARQOS : in STD_LOGIC_VECTOR ( 3 downto 0 );
    S_AXI_HP2_AWCACHE : in STD_LOGIC_VECTOR ( 3 downto 0 );
    S_AXI_HP2_AWLEN : in STD_LOGIC_VECTOR ( 3 downto 0 );
    S_AXI_HP2_AWQOS : in STD_LOGIC_VECTOR ( 3 downto 0 );
    S_AXI_HP2_ARID : in STD_LOGIC_VECTOR ( 5 downto 0 );
    S_AXI_HP2_AWID : in STD_LOGIC_VECTOR ( 5 downto 0 );
    S_AXI_HP2_WID : in STD_LOGIC_VECTOR ( 5 downto 0 );
    S_AXI_HP2_WDATA : in STD_LOGIC_VECTOR ( 63 downto 0 );
    S_AXI_HP2_WSTRB : in STD_LOGIC_VECTOR ( 7 downto 0 );
    S_AXI_HP3_ARESETN : out STD_LOGIC;
    S_AXI_HP3_ARREADY : out STD_LOGIC;
    S_AXI_HP3_AWREADY : out STD_LOGIC;
    S_AXI_HP3_BVALID : out STD_LOGIC;
    S_AXI_HP3_RLAST : out STD_LOGIC;
    S_AXI_HP3_RVALID : out STD_LOGIC;
    S_AXI_HP3_WREADY : out STD_LOGIC;
    S_AXI_HP3_BRESP : out STD_LOGIC_VECTOR ( 1 downto 0 );
    S_AXI_HP3_RRESP : out STD_LOGIC_VECTOR ( 1 downto 0 );
    S_AXI_HP3_BID : out STD_LOGIC_VECTOR ( 5 downto 0 );
    S_AXI_HP3_RID : out STD_LOGIC_VECTOR ( 5 downto 0 );
    S_AXI_HP3_RDATA : out STD_LOGIC_VECTOR ( 63 downto 0 );
    S_AXI_HP3_RCOUNT : out STD_LOGIC_VECTOR ( 7 downto 0 );
    S_AXI_HP3_WCOUNT : out STD_LOGIC_VECTOR ( 7 downto 0 );
    S_AXI_HP3_RACOUNT : out STD_LOGIC_VECTOR ( 2 downto 0 );
    S_AXI_HP3_WACOUNT : out STD_LOGIC_VECTOR ( 5 downto 0 );
    S_AXI_HP3_ACLK : in STD_LOGIC;
    S_AXI_HP3_ARVALID : in STD_LOGIC;
    S_AXI_HP3_AWVALID : in STD_LOGIC;
    S_AXI_HP3_BREADY : in STD_LOGIC;
    S_AXI_HP3_RDISSUECAP1_EN : in STD_LOGIC;
    S_AXI_HP3_RREADY : in STD_LOGIC;
    S_AXI_HP3_WLAST : in STD_LOGIC;
    S_AXI_HP3_WRISSUECAP1_EN : in STD_LOGIC;
    S_AXI_HP3_WVALID : in STD_LOGIC;
    S_AXI_HP3_ARBURST : in STD_LOGIC_VECTOR ( 1 downto 0 );
    S_AXI_HP3_ARLOCK : in STD_LOGIC_VECTOR ( 1 downto 0 );
    S_AXI_HP3_ARSIZE : in STD_LOGIC_VECTOR ( 2 downto 0 );
    S_AXI_HP3_AWBURST : in STD_LOGIC_VECTOR ( 1 downto 0 );
    S_AXI_HP3_AWLOCK : in STD_LOGIC_VECTOR ( 1 downto 0 );
    S_AXI_HP3_AWSIZE : in STD_LOGIC_VECTOR ( 2 downto 0 );
    S_AXI_HP3_ARPROT : in STD_LOGIC_VECTOR ( 2 downto 0 );
    S_AXI_HP3_AWPROT : in STD_LOGIC_VECTOR ( 2 downto 0 );
    S_AXI_HP3_ARADDR : in STD_LOGIC_VECTOR ( 31 downto 0 );
    S_AXI_HP3_AWADDR : in STD_LOGIC_VECTOR ( 31 downto 0 );
    S_AXI_HP3_ARCACHE : in STD_LOGIC_VECTOR ( 3 downto 0 );
    S_AXI_HP3_ARLEN : in STD_LOGIC_VECTOR ( 3 downto 0 );
    S_AXI_HP3_ARQOS : in STD_LOGIC_VECTOR ( 3 downto 0 );
    S_AXI_HP3_AWCACHE : in STD_LOGIC_VECTOR ( 3 downto 0 );
    S_AXI_HP3_AWLEN : in STD_LOGIC_VECTOR ( 3 downto 0 );
    S_AXI_HP3_AWQOS : in STD_LOGIC_VECTOR ( 3 downto 0 );
    S_AXI_HP3_ARID : in STD_LOGIC_VECTOR ( 5 downto 0 );
    S_AXI_HP3_AWID : in STD_LOGIC_VECTOR ( 5 downto 0 );
    S_AXI_HP3_WID : in STD_LOGIC_VECTOR ( 5 downto 0 );
    S_AXI_HP3_WDATA : in STD_LOGIC_VECTOR ( 63 downto 0 );
    S_AXI_HP3_WSTRB : in STD_LOGIC_VECTOR ( 7 downto 0 );
    IRQ_P2F_DMAC_ABORT : out STD_LOGIC;
    IRQ_P2F_DMAC0 : out STD_LOGIC;
    IRQ_P2F_DMAC1 : out STD_LOGIC;
    IRQ_P2F_DMAC2 : out STD_LOGIC;
    IRQ_P2F_DMAC3 : out STD_LOGIC;
    IRQ_P2F_DMAC4 : out STD_LOGIC;
    IRQ_P2F_DMAC5 : out STD_LOGIC;
    IRQ_P2F_DMAC6 : out STD_LOGIC;
    IRQ_P2F_DMAC7 : out STD_LOGIC;
    IRQ_P2F_SMC : out STD_LOGIC;
    IRQ_P2F_QSPI : out STD_LOGIC;
    IRQ_P2F_CTI : out STD_LOGIC;
    IRQ_P2F_GPIO : out STD_LOGIC;
    IRQ_P2F_USB0 : out STD_LOGIC;
    IRQ_P2F_ENET0 : out STD_LOGIC;
    IRQ_P2F_ENET_WAKE0 : out STD_LOGIC;
    IRQ_P2F_SDIO0 : out STD_LOGIC;
    IRQ_P2F_I2C0 : out STD_LOGIC;
    IRQ_P2F_SPI0 : out STD_LOGIC;
    IRQ_P2F_UART0 : out STD_LOGIC;
    IRQ_P2F_CAN0 : out STD_LOGIC;
    IRQ_P2F_USB1 : out STD_LOGIC;
    IRQ_P2F_ENET1 : out STD_LOGIC;
    IRQ_P2F_ENET_WAKE1 : out STD_LOGIC;
    IRQ_P2F_SDIO1 : out STD_LOGIC;
    IRQ_P2F_I2C1 : out STD_LOGIC;
    IRQ_P2F_SPI1 : out STD_LOGIC;
    IRQ_P2F_UART1 : out STD_LOGIC;
    IRQ_P2F_CAN1 : out STD_LOGIC;
    IRQ_F2P : in STD_LOGIC_VECTOR ( 0 to 0 );
    Core0_nFIQ : in STD_LOGIC;
    Core0_nIRQ : in STD_LOGIC;
    Core1_nFIQ : in STD_LOGIC;
    Core1_nIRQ : in STD_LOGIC;
    DMA0_DATYPE : out STD_LOGIC_VECTOR ( 1 downto 0 );
    DMA0_DAVALID : out STD_LOGIC;
    DMA0_DRREADY : out STD_LOGIC;
    DMA0_RSTN : out STD_LOGIC;
    DMA1_DATYPE : out STD_LOGIC_VECTOR ( 1 downto 0 );
    DMA1_DAVALID : out STD_LOGIC;
    DMA1_DRREADY : out STD_LOGIC;
    DMA1_RSTN : out STD_LOGIC;
    DMA2_DATYPE : out STD_LOGIC_VECTOR ( 1 downto 0 );
    DMA2_DAVALID : out STD_LOGIC;
    DMA2_DRREADY : out STD_LOGIC;
    DMA2_RSTN : out STD_LOGIC;
    DMA3_DATYPE : out STD_LOGIC_VECTOR ( 1 downto 0 );
    DMA3_DAVALID : out STD_LOGIC;
    DMA3_DRREADY : out STD_LOGIC;
    DMA3_RSTN : out STD_LOGIC;
    DMA0_ACLK : in STD_LOGIC;
    DMA0_DAREADY : in STD_LOGIC;
    DMA0_DRLAST : in STD_LOGIC;
    DMA0_DRVALID : in STD_LOGIC;
    DMA1_ACLK : in STD_LOGIC;
    DMA1_DAREADY : in STD_LOGIC;
    DMA1_DRLAST : in STD_LOGIC;
    DMA1_DRVALID : in STD_LOGIC;
    DMA2_ACLK : in STD_LOGIC;
    DMA2_DAREADY : in STD_LOGIC;
    DMA2_DRLAST : in STD_LOGIC;
    DMA2_DRVALID : in STD_LOGIC;
    DMA3_ACLK : in STD_LOGIC;
    DMA3_DAREADY : in STD_LOGIC;
    DMA3_DRLAST : in STD_LOGIC;
    DMA3_DRVALID : in STD_LOGIC;
    DMA0_DRTYPE : in STD_LOGIC_VECTOR ( 1 downto 0 );
    DMA1_DRTYPE : in STD_LOGIC_VECTOR ( 1 downto 0 );
    DMA2_DRTYPE : in STD_LOGIC_VECTOR ( 1 downto 0 );
    DMA3_DRTYPE : in STD_LOGIC_VECTOR ( 1 downto 0 );
    FCLK_CLK3 : out STD_LOGIC;
    FCLK_CLK2 : out STD_LOGIC;
    FCLK_CLK1 : out STD_LOGIC;
    FCLK_CLK0 : out STD_LOGIC;
    FCLK_CLKTRIG3_N : in STD_LOGIC;
    FCLK_CLKTRIG2_N : in STD_LOGIC;
    FCLK_CLKTRIG1_N : in STD_LOGIC;
    FCLK_CLKTRIG0_N : in STD_LOGIC;
    FCLK_RESET3_N : out STD_LOGIC;
    FCLK_RESET2_N : out STD_LOGIC;
    FCLK_RESET1_N : out STD_LOGIC;
    FCLK_RESET0_N : out STD_LOGIC;
    FTMD_TRACEIN_DATA : in STD_LOGIC_VECTOR ( 31 downto 0 );
    FTMD_TRACEIN_VALID : in STD_LOGIC;
    FTMD_TRACEIN_CLK : in STD_LOGIC;
    FTMD_TRACEIN_ATID : in STD_LOGIC_VECTOR ( 3 downto 0 );
    FTMT_F2P_TRIG_0 : in STD_LOGIC;
    FTMT_F2P_TRIGACK_0 : out STD_LOGIC;
    FTMT_F2P_TRIG_1 : in STD_LOGIC;
    FTMT_F2P_TRIGACK_1 : out STD_LOGIC;
    FTMT_F2P_TRIG_2 : in STD_LOGIC;
    FTMT_F2P_TRIGACK_2 : out STD_LOGIC;
    FTMT_F2P_TRIG_3 : in STD_LOGIC;
    FTMT_F2P_TRIGACK_3 : out STD_LOGIC;
    FTMT_F2P_DEBUG : in STD_LOGIC_VECTOR ( 31 downto 0 );
    FTMT_P2F_TRIGACK_0 : in STD_LOGIC;
    FTMT_P2F_TRIG_0 : out STD_LOGIC;
    FTMT_P2F_TRIGACK_1 : in STD_LOGIC;
    FTMT_P2F_TRIG_1 : out STD_LOGIC;
    FTMT_P2F_TRIGACK_2 : in STD_LOGIC;
    FTMT_P2F_TRIG_2 : out STD_LOGIC;
    FTMT_P2F_TRIGACK_3 : in STD_LOGIC;
    FTMT_P2F_TRIG_3 : out STD_LOGIC;
    FTMT_P2F_DEBUG : out STD_LOGIC_VECTOR ( 31 downto 0 );
    FPGA_IDLE_N : in STD_LOGIC;
    EVENT_EVENTO : out STD_LOGIC;
    EVENT_STANDBYWFE : out STD_LOGIC_VECTOR ( 1 downto 0 );
    EVENT_STANDBYWFI : out STD_LOGIC_VECTOR ( 1 downto 0 );
    EVENT_EVENTI : in STD_LOGIC;
    DDR_ARB : in STD_LOGIC_VECTOR ( 3 downto 0 );
    MIO : inout STD_LOGIC_VECTOR ( 53 downto 0 );
    DDR_CAS_n : inout STD_LOGIC;
    DDR_CKE : inout STD_LOGIC;
    DDR_Clk_n : inout STD_LOGIC;
    DDR_Clk : inout STD_LOGIC;
    DDR_CS_n : inout STD_LOGIC;
    DDR_DRSTB : inout STD_LOGIC;
    DDR_ODT : inout STD_LOGIC;
    DDR_RAS_n : inout STD_LOGIC;
    DDR_WEB : inout STD_LOGIC;
    DDR_BankAddr : inout STD_LOGIC_VECTOR ( 2 downto 0 );
    DDR_Addr : inout STD_LOGIC_VECTOR ( 14 downto 0 );
    DDR_VRN : inout STD_LOGIC;
    DDR_VRP : inout STD_LOGIC;
    DDR_DM : inout STD_LOGIC_VECTOR ( 3 downto 0 );
    DDR_DQ : inout STD_LOGIC_VECTOR ( 31 downto 0 );
    DDR_DQS_n : inout STD_LOGIC_VECTOR ( 3 downto 0 );
    DDR_DQS : inout STD_LOGIC_VECTOR ( 3 downto 0 );
    PS_SRSTB : inout STD_LOGIC;
    PS_CLK : inout STD_LOGIC;
    PS_PORB : inout STD_LOGIC
  );
  attribute C_DM_WIDTH : integer;
  attribute C_DM_WIDTH of decalper_eb_ot_sdeen_pot_pi_dehcac_xnilix_processing_system7_v5_5_processing_system7 : entity is 4;
  attribute C_DQS_WIDTH : integer;
  attribute C_DQS_WIDTH of decalper_eb_ot_sdeen_pot_pi_dehcac_xnilix_processing_system7_v5_5_processing_system7 : entity is 4;
  attribute C_DQ_WIDTH : integer;
  attribute C_DQ_WIDTH of decalper_eb_ot_sdeen_pot_pi_dehcac_xnilix_processing_system7_v5_5_processing_system7 : entity is 32;
  attribute C_EMIO_GPIO_WIDTH : integer;
  attribute C_EMIO_GPIO_WIDTH of decalper_eb_ot_sdeen_pot_pi_dehcac_xnilix_processing_system7_v5_5_processing_system7 : entity is 64;
  attribute C_EN_EMIO_ENET0 : integer;
  attribute C_EN_EMIO_ENET0 of decalper_eb_ot_sdeen_pot_pi_dehcac_xnilix_processing_system7_v5_5_processing_system7 : entity is 0;
  attribute C_EN_EMIO_ENET1 : integer;
  attribute C_EN_EMIO_ENET1 of decalper_eb_ot_sdeen_pot_pi_dehcac_xnilix_processing_system7_v5_5_processing_system7 : entity is 0;
  attribute C_EN_EMIO_PJTAG : integer;
  attribute C_EN_EMIO_PJTAG of decalper_eb_ot_sdeen_pot_pi_dehcac_xnilix_processing_system7_v5_5_processing_system7 : entity is 0;
  attribute C_EN_EMIO_TRACE : integer;
  attribute C_EN_EMIO_TRACE of decalper_eb_ot_sdeen_pot_pi_dehcac_xnilix_processing_system7_v5_5_processing_system7 : entity is 0;
  attribute C_FCLK_CLK0_BUF : string;
  attribute C_FCLK_CLK0_BUF of decalper_eb_ot_sdeen_pot_pi_dehcac_xnilix_processing_system7_v5_5_processing_system7 : entity is "TRUE";
  attribute C_FCLK_CLK1_BUF : string;
  attribute C_FCLK_CLK1_BUF of decalper_eb_ot_sdeen_pot_pi_dehcac_xnilix_processing_system7_v5_5_processing_system7 : entity is "FALSE";
  attribute C_FCLK_CLK2_BUF : string;
  attribute C_FCLK_CLK2_BUF of decalper_eb_ot_sdeen_pot_pi_dehcac_xnilix_processing_system7_v5_5_processing_system7 : entity is "FALSE";
  attribute C_FCLK_CLK3_BUF : string;
  attribute C_FCLK_CLK3_BUF of decalper_eb_ot_sdeen_pot_pi_dehcac_xnilix_processing_system7_v5_5_processing_system7 : entity is "FALSE";
  attribute C_GP0_EN_MODIFIABLE_TXN : integer;
  attribute C_GP0_EN_MODIFIABLE_TXN of decalper_eb_ot_sdeen_pot_pi_dehcac_xnilix_processing_system7_v5_5_processing_system7 : entity is 1;
  attribute C_GP1_EN_MODIFIABLE_TXN : integer;
  attribute C_GP1_EN_MODIFIABLE_TXN of decalper_eb_ot_sdeen_pot_pi_dehcac_xnilix_processing_system7_v5_5_processing_system7 : entity is 1;
  attribute C_INCLUDE_ACP_TRANS_CHECK : integer;
  attribute C_INCLUDE_ACP_TRANS_CHECK of decalper_eb_ot_sdeen_pot_pi_dehcac_xnilix_processing_system7_v5_5_processing_system7 : entity is 0;
  attribute C_INCLUDE_TRACE_BUFFER : integer;
  attribute C_INCLUDE_TRACE_BUFFER of decalper_eb_ot_sdeen_pot_pi_dehcac_xnilix_processing_system7_v5_5_processing_system7 : entity is 0;
  attribute C_IRQ_F2P_MODE : string;
  attribute C_IRQ_F2P_MODE of decalper_eb_ot_sdeen_pot_pi_dehcac_xnilix_processing_system7_v5_5_processing_system7 : entity is "DIRECT";
  attribute C_MIO_PRIMITIVE : integer;
  attribute C_MIO_PRIMITIVE of decalper_eb_ot_sdeen_pot_pi_dehcac_xnilix_processing_system7_v5_5_processing_system7 : entity is 54;
  attribute C_M_AXI_GP0_ENABLE_STATIC_REMAP : integer;
  attribute C_M_AXI_GP0_ENABLE_STATIC_REMAP of decalper_eb_ot_sdeen_pot_pi_dehcac_xnilix_processing_system7_v5_5_processing_system7 : entity is 0;
  attribute C_M_AXI_GP0_ID_WIDTH : integer;
  attribute C_M_AXI_GP0_ID_WIDTH of decalper_eb_ot_sdeen_pot_pi_dehcac_xnilix_processing_system7_v5_5_processing_system7 : entity is 12;
  attribute C_M_AXI_GP0_THREAD_ID_WIDTH : integer;
  attribute C_M_AXI_GP0_THREAD_ID_WIDTH of decalper_eb_ot_sdeen_pot_pi_dehcac_xnilix_processing_system7_v5_5_processing_system7 : entity is 12;
  attribute C_M_AXI_GP1_ENABLE_STATIC_REMAP : integer;
  attribute C_M_AXI_GP1_ENABLE_STATIC_REMAP of decalper_eb_ot_sdeen_pot_pi_dehcac_xnilix_processing_system7_v5_5_processing_system7 : entity is 0;
  attribute C_M_AXI_GP1_ID_WIDTH : integer;
  attribute C_M_AXI_GP1_ID_WIDTH of decalper_eb_ot_sdeen_pot_pi_dehcac_xnilix_processing_system7_v5_5_processing_system7 : entity is 12;
  attribute C_M_AXI_GP1_THREAD_ID_WIDTH : integer;
  attribute C_M_AXI_GP1_THREAD_ID_WIDTH of decalper_eb_ot_sdeen_pot_pi_dehcac_xnilix_processing_system7_v5_5_processing_system7 : entity is 12;
  attribute C_NUM_F2P_INTR_INPUTS : integer;
  attribute C_NUM_F2P_INTR_INPUTS of decalper_eb_ot_sdeen_pot_pi_dehcac_xnilix_processing_system7_v5_5_processing_system7 : entity is 1;
  attribute C_PACKAGE_NAME : string;
  attribute C_PACKAGE_NAME of decalper_eb_ot_sdeen_pot_pi_dehcac_xnilix_processing_system7_v5_5_processing_system7 : entity is "clg400";
  attribute C_PS7_SI_REV : string;
  attribute C_PS7_SI_REV of decalper_eb_ot_sdeen_pot_pi_dehcac_xnilix_processing_system7_v5_5_processing_system7 : entity is "PRODUCTION";
  attribute C_S_AXI_ACP_ARUSER_VAL : integer;
  attribute C_S_AXI_ACP_ARUSER_VAL of decalper_eb_ot_sdeen_pot_pi_dehcac_xnilix_processing_system7_v5_5_processing_system7 : entity is 31;
  attribute C_S_AXI_ACP_AWUSER_VAL : integer;
  attribute C_S_AXI_ACP_AWUSER_VAL of decalper_eb_ot_sdeen_pot_pi_dehcac_xnilix_processing_system7_v5_5_processing_system7 : entity is 31;
  attribute C_S_AXI_ACP_ID_WIDTH : integer;
  attribute C_S_AXI_ACP_ID_WIDTH of decalper_eb_ot_sdeen_pot_pi_dehcac_xnilix_processing_system7_v5_5_processing_system7 : entity is 3;
  attribute C_S_AXI_GP0_ID_WIDTH : integer;
  attribute C_S_AXI_GP0_ID_WIDTH of decalper_eb_ot_sdeen_pot_pi_dehcac_xnilix_processing_system7_v5_5_processing_system7 : entity is 6;
  attribute C_S_AXI_GP1_ID_WIDTH : integer;
  attribute C_S_AXI_GP1_ID_WIDTH of decalper_eb_ot_sdeen_pot_pi_dehcac_xnilix_processing_system7_v5_5_processing_system7 : entity is 6;
  attribute C_S_AXI_HP0_DATA_WIDTH : integer;
  attribute C_S_AXI_HP0_DATA_WIDTH of decalper_eb_ot_sdeen_pot_pi_dehcac_xnilix_processing_system7_v5_5_processing_system7 : entity is 64;
  attribute C_S_AXI_HP0_ID_WIDTH : integer;
  attribute C_S_AXI_HP0_ID_WIDTH of decalper_eb_ot_sdeen_pot_pi_dehcac_xnilix_processing_system7_v5_5_processing_system7 : entity is 6;
  attribute C_S_AXI_HP1_DATA_WIDTH : integer;
  attribute C_S_AXI_HP1_DATA_WIDTH of decalper_eb_ot_sdeen_pot_pi_dehcac_xnilix_processing_system7_v5_5_processing_system7 : entity is 64;
  attribute C_S_AXI_HP1_ID_WIDTH : integer;
  attribute C_S_AXI_HP1_ID_WIDTH of decalper_eb_ot_sdeen_pot_pi_dehcac_xnilix_processing_system7_v5_5_processing_system7 : entity is 6;
  attribute C_S_AXI_HP2_DATA_WIDTH : integer;
  attribute C_S_AXI_HP2_DATA_WIDTH of decalper_eb_ot_sdeen_pot_pi_dehcac_xnilix_processing_system7_v5_5_processing_system7 : entity is 64;
  attribute C_S_AXI_HP2_ID_WIDTH : integer;
  attribute C_S_AXI_HP2_ID_WIDTH of decalper_eb_ot_sdeen_pot_pi_dehcac_xnilix_processing_system7_v5_5_processing_system7 : entity is 6;
  attribute C_S_AXI_HP3_DATA_WIDTH : integer;
  attribute C_S_AXI_HP3_DATA_WIDTH of decalper_eb_ot_sdeen_pot_pi_dehcac_xnilix_processing_system7_v5_5_processing_system7 : entity is 64;
  attribute C_S_AXI_HP3_ID_WIDTH : integer;
  attribute C_S_AXI_HP3_ID_WIDTH of decalper_eb_ot_sdeen_pot_pi_dehcac_xnilix_processing_system7_v5_5_processing_system7 : entity is 6;
  attribute C_TRACE_BUFFER_CLOCK_DELAY : integer;
  attribute C_TRACE_BUFFER_CLOCK_DELAY of decalper_eb_ot_sdeen_pot_pi_dehcac_xnilix_processing_system7_v5_5_processing_system7 : entity is 12;
  attribute C_TRACE_BUFFER_FIFO_SIZE : integer;
  attribute C_TRACE_BUFFER_FIFO_SIZE of decalper_eb_ot_sdeen_pot_pi_dehcac_xnilix_processing_system7_v5_5_processing_system7 : entity is 128;
  attribute C_TRACE_INTERNAL_WIDTH : integer;
  attribute C_TRACE_INTERNAL_WIDTH of decalper_eb_ot_sdeen_pot_pi_dehcac_xnilix_processing_system7_v5_5_processing_system7 : entity is 2;
  attribute C_TRACE_PIPELINE_WIDTH : integer;
  attribute C_TRACE_PIPELINE_WIDTH of decalper_eb_ot_sdeen_pot_pi_dehcac_xnilix_processing_system7_v5_5_processing_system7 : entity is 8;
  attribute C_USE_AXI_NONSECURE : integer;
  attribute C_USE_AXI_NONSECURE of decalper_eb_ot_sdeen_pot_pi_dehcac_xnilix_processing_system7_v5_5_processing_system7 : entity is 0;
  attribute C_USE_DEFAULT_ACP_USER_VAL : integer;
  attribute C_USE_DEFAULT_ACP_USER_VAL of decalper_eb_ot_sdeen_pot_pi_dehcac_xnilix_processing_system7_v5_5_processing_system7 : entity is 0;
  attribute C_USE_M_AXI_GP0 : integer;
  attribute C_USE_M_AXI_GP0 of decalper_eb_ot_sdeen_pot_pi_dehcac_xnilix_processing_system7_v5_5_processing_system7 : entity is 0;
  attribute C_USE_M_AXI_GP1 : integer;
  attribute C_USE_M_AXI_GP1 of decalper_eb_ot_sdeen_pot_pi_dehcac_xnilix_processing_system7_v5_5_processing_system7 : entity is 0;
  attribute C_USE_S_AXI_ACP : integer;
  attribute C_USE_S_AXI_ACP of decalper_eb_ot_sdeen_pot_pi_dehcac_xnilix_processing_system7_v5_5_processing_system7 : entity is 0;
  attribute C_USE_S_AXI_GP0 : integer;
  attribute C_USE_S_AXI_GP0 of decalper_eb_ot_sdeen_pot_pi_dehcac_xnilix_processing_system7_v5_5_processing_system7 : entity is 0;
  attribute C_USE_S_AXI_GP1 : integer;
  attribute C_USE_S_AXI_GP1 of decalper_eb_ot_sdeen_pot_pi_dehcac_xnilix_processing_system7_v5_5_processing_system7 : entity is 0;
  attribute C_USE_S_AXI_HP0 : integer;
  attribute C_USE_S_AXI_HP0 of decalper_eb_ot_sdeen_pot_pi_dehcac_xnilix_processing_system7_v5_5_processing_system7 : entity is 0;
  attribute C_USE_S_AXI_HP1 : integer;
  attribute C_USE_S_AXI_HP1 of decalper_eb_ot_sdeen_pot_pi_dehcac_xnilix_processing_system7_v5_5_processing_system7 : entity is 0;
  attribute C_USE_S_AXI_HP2 : integer;
  attribute C_USE_S_AXI_HP2 of decalper_eb_ot_sdeen_pot_pi_dehcac_xnilix_processing_system7_v5_5_processing_system7 : entity is 0;
  attribute C_USE_S_AXI_HP3 : integer;
  attribute C_USE_S_AXI_HP3 of decalper_eb_ot_sdeen_pot_pi_dehcac_xnilix_processing_system7_v5_5_processing_system7 : entity is 0;
  attribute HW_HANDOFF : string;
  attribute HW_HANDOFF of decalper_eb_ot_sdeen_pot_pi_dehcac_xnilix_processing_system7_v5_5_processing_system7 : entity is "System_processing_system7_0_0.hwdef";
  attribute POWER : string;
  attribute POWER of decalper_eb_ot_sdeen_pot_pi_dehcac_xnilix_processing_system7_v5_5_processing_system7 : entity is "<PROCESSOR name={system} numA9Cores={2} clockFreq={666.666666} load={0.5} /><MEMORY name={code} memType={DDR3} dataWidth={16} clockFreq={533.333333} readRate={0.5} writeRate={0.5} /><IO interface={UART} ioStandard={LVCMOS33} bidis={2} ioBank={Vcco_p1} clockFreq={100.000000} usageRate={0.5} /><IO interface={NAND} ioStandard={} bidis={14} ioBank={} clockFreq={100.000000} usageRate={0.5} /><PLL domain={Processor} vco={1333.333} /><PLL domain={Memory} vco={1066.667} /><PLL domain={IO} vco={1600.000} />/>";
  attribute USE_TRACE_DATA_EDGE_DETECTOR : integer;
  attribute USE_TRACE_DATA_EDGE_DETECTOR of decalper_eb_ot_sdeen_pot_pi_dehcac_xnilix_processing_system7_v5_5_processing_system7 : entity is 0;
end decalper_eb_ot_sdeen_pot_pi_dehcac_xnilix_processing_system7_v5_5_processing_system7;

architecture STRUCTURE of decalper_eb_ot_sdeen_pot_pi_dehcac_xnilix_processing_system7_v5_5_processing_system7 is
  signal \<const0>\ : STD_LOGIC;
  signal \<const1>\ : STD_LOGIC;
  signal ENET0_MDIO_T_n : STD_LOGIC;
  signal ENET1_MDIO_T_n : STD_LOGIC;
  signal FCLK_CLK_unbuffered : STD_LOGIC_VECTOR ( 0 to 0 );
  signal I2C0_SCL_T_n : STD_LOGIC;
  signal I2C0_SDA_T_n : STD_LOGIC;
  signal I2C1_SCL_T_n : STD_LOGIC;
  signal I2C1_SDA_T_n : STD_LOGIC;
  signal \^m_axi_gp0_arcache\ : STD_LOGIC_VECTOR ( 3 downto 0 );
  signal \^m_axi_gp0_arsize\ : STD_LOGIC_VECTOR ( 1 downto 0 );
  signal \^m_axi_gp0_awcache\ : STD_LOGIC_VECTOR ( 3 downto 0 );
  signal \^m_axi_gp0_awsize\ : STD_LOGIC_VECTOR ( 1 downto 0 );
  signal \^m_axi_gp1_arcache\ : STD_LOGIC_VECTOR ( 3 downto 0 );
  signal \^m_axi_gp1_arsize\ : STD_LOGIC_VECTOR ( 1 downto 0 );
  signal \^m_axi_gp1_awcache\ : STD_LOGIC_VECTOR ( 3 downto 0 );
  signal \^m_axi_gp1_awsize\ : STD_LOGIC_VECTOR ( 1 downto 0 );
  signal SDIO0_CMD_T_n : STD_LOGIC;
  signal SDIO0_DATA_T_n : STD_LOGIC_VECTOR ( 3 downto 0 );
  signal SDIO1_CMD_T_n : STD_LOGIC;
  signal SDIO1_DATA_T_n : STD_LOGIC_VECTOR ( 3 downto 0 );
  signal SPI0_MISO_T_n : STD_LOGIC;
  signal SPI0_MOSI_T_n : STD_LOGIC;
  signal SPI0_SCLK_T_n : STD_LOGIC;
  signal SPI0_SS_T_n : STD_LOGIC;
  signal SPI1_MISO_T_n : STD_LOGIC;
  signal SPI1_MOSI_T_n : STD_LOGIC;
  signal SPI1_SCLK_T_n : STD_LOGIC;
  signal SPI1_SS_T_n : STD_LOGIC;
  signal \TRACE_CTL_PIPE[0]\ : STD_LOGIC;
  attribute RTL_KEEP : string;
  attribute RTL_KEEP of \TRACE_CTL_PIPE[0]\ : signal is "true";
  signal \TRACE_CTL_PIPE[1]\ : STD_LOGIC;
  attribute RTL_KEEP of \TRACE_CTL_PIPE[1]\ : signal is "true";
  signal \TRACE_CTL_PIPE[2]\ : STD_LOGIC;
  attribute RTL_KEEP of \TRACE_CTL_PIPE[2]\ : signal is "true";
  signal \TRACE_CTL_PIPE[3]\ : STD_LOGIC;
  attribute RTL_KEEP of \TRACE_CTL_PIPE[3]\ : signal is "true";
  signal \TRACE_CTL_PIPE[4]\ : STD_LOGIC;
  attribute RTL_KEEP of \TRACE_CTL_PIPE[4]\ : signal is "true";
  signal \TRACE_CTL_PIPE[5]\ : STD_LOGIC;
  attribute RTL_KEEP of \TRACE_CTL_PIPE[5]\ : signal is "true";
  signal \TRACE_CTL_PIPE[6]\ : STD_LOGIC;
  attribute RTL_KEEP of \TRACE_CTL_PIPE[6]\ : signal is "true";
  signal \TRACE_CTL_PIPE[7]\ : STD_LOGIC;
  attribute RTL_KEEP of \TRACE_CTL_PIPE[7]\ : signal is "true";
  signal \TRACE_DATA_PIPE[0]\ : STD_LOGIC_VECTOR ( 1 downto 0 );
  attribute RTL_KEEP of \TRACE_DATA_PIPE[0]\ : signal is "true";
  signal \TRACE_DATA_PIPE[1]\ : STD_LOGIC_VECTOR ( 1 downto 0 );
  attribute RTL_KEEP of \TRACE_DATA_PIPE[1]\ : signal is "true";
  signal \TRACE_DATA_PIPE[2]\ : STD_LOGIC_VECTOR ( 1 downto 0 );
  attribute RTL_KEEP of \TRACE_DATA_PIPE[2]\ : signal is "true";
  signal \TRACE_DATA_PIPE[3]\ : STD_LOGIC_VECTOR ( 1 downto 0 );
  attribute RTL_KEEP of \TRACE_DATA_PIPE[3]\ : signal is "true";
  signal \TRACE_DATA_PIPE[4]\ : STD_LOGIC_VECTOR ( 1 downto 0 );
  attribute RTL_KEEP of \TRACE_DATA_PIPE[4]\ : signal is "true";
  signal \TRACE_DATA_PIPE[5]\ : STD_LOGIC_VECTOR ( 1 downto 0 );
  attribute RTL_KEEP of \TRACE_DATA_PIPE[5]\ : signal is "true";
  signal \TRACE_DATA_PIPE[6]\ : STD_LOGIC_VECTOR ( 1 downto 0 );
  attribute RTL_KEEP of \TRACE_DATA_PIPE[6]\ : signal is "true";
  signal \TRACE_DATA_PIPE[7]\ : STD_LOGIC_VECTOR ( 1 downto 0 );
  attribute RTL_KEEP of \TRACE_DATA_PIPE[7]\ : signal is "true";
  signal buffered_DDR_Addr : STD_LOGIC_VECTOR ( 14 downto 0 );
  signal buffered_DDR_BankAddr : STD_LOGIC_VECTOR ( 2 downto 0 );
  signal buffered_DDR_CAS_n : STD_LOGIC;
  signal buffered_DDR_CKE : STD_LOGIC;
  signal buffered_DDR_CS_n : STD_LOGIC;
  signal buffered_DDR_Clk : STD_LOGIC;
  signal buffered_DDR_Clk_n : STD_LOGIC;
  signal buffered_DDR_DM : STD_LOGIC_VECTOR ( 3 downto 0 );
  signal buffered_DDR_DQ : STD_LOGIC_VECTOR ( 31 downto 0 );
  signal buffered_DDR_DQS : STD_LOGIC_VECTOR ( 3 downto 0 );
  signal buffered_DDR_DQS_n : STD_LOGIC_VECTOR ( 3 downto 0 );
  signal buffered_DDR_DRSTB : STD_LOGIC;
  signal buffered_DDR_ODT : STD_LOGIC;
  signal buffered_DDR_RAS_n : STD_LOGIC;
  signal buffered_DDR_VRN : STD_LOGIC;
  signal buffered_DDR_VRP : STD_LOGIC;
  signal buffered_DDR_WEB : STD_LOGIC;
  signal buffered_MIO : STD_LOGIC_VECTOR ( 53 downto 0 );
  signal buffered_PS_CLK : STD_LOGIC;
  signal buffered_PS_PORB : STD_LOGIC;
  signal buffered_PS_SRSTB : STD_LOGIC;
  signal gpio_out_t_n : STD_LOGIC_VECTOR ( 63 downto 0 );
  signal NLW_PS7_i_EMIOENET0GMIITXEN_UNCONNECTED : STD_LOGIC;
  signal NLW_PS7_i_EMIOENET0GMIITXER_UNCONNECTED : STD_LOGIC;
  signal NLW_PS7_i_EMIOENET1GMIITXEN_UNCONNECTED : STD_LOGIC;
  signal NLW_PS7_i_EMIOENET1GMIITXER_UNCONNECTED : STD_LOGIC;
  signal NLW_PS7_i_EMIOPJTAGTDO_UNCONNECTED : STD_LOGIC;
  signal NLW_PS7_i_EMIOPJTAGTDTN_UNCONNECTED : STD_LOGIC;
  signal NLW_PS7_i_EMIOTRACECTL_UNCONNECTED : STD_LOGIC;
  signal NLW_PS7_i_EMIOENET0GMIITXD_UNCONNECTED : STD_LOGIC_VECTOR ( 7 downto 0 );
  signal NLW_PS7_i_EMIOENET1GMIITXD_UNCONNECTED : STD_LOGIC_VECTOR ( 7 downto 0 );
  signal NLW_PS7_i_EMIOTRACEDATA_UNCONNECTED : STD_LOGIC_VECTOR ( 31 downto 0 );
  signal NLW_PS7_i_MAXIGP0ARCACHE_UNCONNECTED : STD_LOGIC_VECTOR ( 1 to 1 );
  signal NLW_PS7_i_MAXIGP0AWCACHE_UNCONNECTED : STD_LOGIC_VECTOR ( 1 to 1 );
  signal NLW_PS7_i_MAXIGP1ARCACHE_UNCONNECTED : STD_LOGIC_VECTOR ( 1 to 1 );
  signal NLW_PS7_i_MAXIGP1AWCACHE_UNCONNECTED : STD_LOGIC_VECTOR ( 1 to 1 );
  attribute BOX_TYPE : string;
  attribute BOX_TYPE of DDR_CAS_n_BIBUF : label is "PRIMITIVE";
  attribute BOX_TYPE of DDR_CKE_BIBUF : label is "PRIMITIVE";
  attribute BOX_TYPE of DDR_CS_n_BIBUF : label is "PRIMITIVE";
  attribute BOX_TYPE of DDR_Clk_BIBUF : label is "PRIMITIVE";
  attribute BOX_TYPE of DDR_Clk_n_BIBUF : label is "PRIMITIVE";
  attribute BOX_TYPE of DDR_DRSTB_BIBUF : label is "PRIMITIVE";
  attribute BOX_TYPE of DDR_ODT_BIBUF : label is "PRIMITIVE";
  attribute BOX_TYPE of DDR_RAS_n_BIBUF : label is "PRIMITIVE";
  attribute BOX_TYPE of DDR_VRN_BIBUF : label is "PRIMITIVE";
  attribute BOX_TYPE of DDR_VRP_BIBUF : label is "PRIMITIVE";
  attribute BOX_TYPE of DDR_WEB_BIBUF : label is "PRIMITIVE";
  attribute BOX_TYPE of PS7_i : label is "PRIMITIVE";
  attribute BOX_TYPE of PS_CLK_BIBUF : label is "PRIMITIVE";
  attribute BOX_TYPE of PS_PORB_BIBUF : label is "PRIMITIVE";
  attribute BOX_TYPE of PS_SRSTB_BIBUF : label is "PRIMITIVE";
  attribute BOX_TYPE of \buffer_fclk_clk_0.FCLK_CLK_0_BUFG\ : label is "PRIMITIVE";
  attribute BOX_TYPE of \genblk13[0].MIO_BIBUF\ : label is "PRIMITIVE";
  attribute BOX_TYPE of \genblk13[10].MIO_BIBUF\ : label is "PRIMITIVE";
  attribute BOX_TYPE of \genblk13[11].MIO_BIBUF\ : label is "PRIMITIVE";
  attribute BOX_TYPE of \genblk13[12].MIO_BIBUF\ : label is "PRIMITIVE";
  attribute BOX_TYPE of \genblk13[13].MIO_BIBUF\ : label is "PRIMITIVE";
  attribute BOX_TYPE of \genblk13[14].MIO_BIBUF\ : label is "PRIMITIVE";
  attribute BOX_TYPE of \genblk13[15].MIO_BIBUF\ : label is "PRIMITIVE";
  attribute BOX_TYPE of \genblk13[16].MIO_BIBUF\ : label is "PRIMITIVE";
  attribute BOX_TYPE of \genblk13[17].MIO_BIBUF\ : label is "PRIMITIVE";
  attribute BOX_TYPE of \genblk13[18].MIO_BIBUF\ : label is "PRIMITIVE";
  attribute BOX_TYPE of \genblk13[19].MIO_BIBUF\ : label is "PRIMITIVE";
  attribute BOX_TYPE of \genblk13[1].MIO_BIBUF\ : label is "PRIMITIVE";
  attribute BOX_TYPE of \genblk13[20].MIO_BIBUF\ : label is "PRIMITIVE";
  attribute BOX_TYPE of \genblk13[21].MIO_BIBUF\ : label is "PRIMITIVE";
  attribute BOX_TYPE of \genblk13[22].MIO_BIBUF\ : label is "PRIMITIVE";
  attribute BOX_TYPE of \genblk13[23].MIO_BIBUF\ : label is "PRIMITIVE";
  attribute BOX_TYPE of \genblk13[24].MIO_BIBUF\ : label is "PRIMITIVE";
  attribute BOX_TYPE of \genblk13[25].MIO_BIBUF\ : label is "PRIMITIVE";
  attribute BOX_TYPE of \genblk13[26].MIO_BIBUF\ : label is "PRIMITIVE";
  attribute BOX_TYPE of \genblk13[27].MIO_BIBUF\ : label is "PRIMITIVE";
  attribute BOX_TYPE of \genblk13[28].MIO_BIBUF\ : label is "PRIMITIVE";
  attribute BOX_TYPE of \genblk13[29].MIO_BIBUF\ : label is "PRIMITIVE";
  attribute BOX_TYPE of \genblk13[2].MIO_BIBUF\ : label is "PRIMITIVE";
  attribute BOX_TYPE of \genblk13[30].MIO_BIBUF\ : label is "PRIMITIVE";
  attribute BOX_TYPE of \genblk13[31].MIO_BIBUF\ : label is "PRIMITIVE";
  attribute BOX_TYPE of \genblk13[32].MIO_BIBUF\ : label is "PRIMITIVE";
  attribute BOX_TYPE of \genblk13[33].MIO_BIBUF\ : label is "PRIMITIVE";
  attribute BOX_TYPE of \genblk13[34].MIO_BIBUF\ : label is "PRIMITIVE";
  attribute BOX_TYPE of \genblk13[35].MIO_BIBUF\ : label is "PRIMITIVE";
  attribute BOX_TYPE of \genblk13[36].MIO_BIBUF\ : label is "PRIMITIVE";
  attribute BOX_TYPE of \genblk13[37].MIO_BIBUF\ : label is "PRIMITIVE";
  attribute BOX_TYPE of \genblk13[38].MIO_BIBUF\ : label is "PRIMITIVE";
  attribute BOX_TYPE of \genblk13[39].MIO_BIBUF\ : label is "PRIMITIVE";
  attribute BOX_TYPE of \genblk13[3].MIO_BIBUF\ : label is "PRIMITIVE";
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
  attribute BOX_TYPE of \genblk17[23].DDR_DQ_BIBUF\ : label is "PRIMITIVE";
  attribute BOX_TYPE of \genblk17[24].DDR_DQ_BIBUF\ : label is "PRIMITIVE";
  attribute BOX_TYPE of \genblk17[25].DDR_DQ_BIBUF\ : label is "PRIMITIVE";
  attribute BOX_TYPE of \genblk17[26].DDR_DQ_BIBUF\ : label is "PRIMITIVE";
  attribute BOX_TYPE of \genblk17[27].DDR_DQ_BIBUF\ : label is "PRIMITIVE";
  attribute BOX_TYPE of \genblk17[28].DDR_DQ_BIBUF\ : label is "PRIMITIVE";
  attribute BOX_TYPE of \genblk17[29].DDR_DQ_BIBUF\ : label is "PRIMITIVE";
  attribute BOX_TYPE of \genblk17[2].DDR_DQ_BIBUF\ : label is "PRIMITIVE";
  attribute BOX_TYPE of \genblk17[30].DDR_DQ_BIBUF\ : label is "PRIMITIVE";
  attribute BOX_TYPE of \genblk17[31].DDR_DQ_BIBUF\ : label is "PRIMITIVE";
  attribute BOX_TYPE of \genblk17[3].DDR_DQ_BIBUF\ : label is "PRIMITIVE";
  attribute BOX_TYPE of \genblk17[4].DDR_DQ_BIBUF\ : label is "PRIMITIVE";
  attribute BOX_TYPE of \genblk17[5].DDR_DQ_BIBUF\ : label is "PRIMITIVE";
  attribute BOX_TYPE of \genblk17[6].DDR_DQ_BIBUF\ : label is "PRIMITIVE";
  attribute BOX_TYPE of \genblk17[7].DDR_DQ_BIBUF\ : label is "PRIMITIVE";
  attribute BOX_TYPE of \genblk17[8].DDR_DQ_BIBUF\ : label is "PRIMITIVE";
  attribute BOX_TYPE of \genblk17[9].DDR_DQ_BIBUF\ : label is "PRIMITIVE";
  attribute BOX_TYPE of \genblk18[0].DDR_DQS_n_BIBUF\ : label is "PRIMITIVE";
  attribute BOX_TYPE of \genblk18[1].DDR_DQS_n_BIBUF\ : label is "PRIMITIVE";
  attribute BOX_TYPE of \genblk18[2].DDR_DQS_n_BIBUF\ : label is "PRIMITIVE";
  attribute BOX_TYPE of \genblk18[3].DDR_DQS_n_BIBUF\ : label is "PRIMITIVE";
  attribute BOX_TYPE of \genblk19[0].DDR_DQS_BIBUF\ : label is "PRIMITIVE";
  attribute BOX_TYPE of \genblk19[1].DDR_DQS_BIBUF\ : label is "PRIMITIVE";
  attribute BOX_TYPE of \genblk19[2].DDR_DQS_BIBUF\ : label is "PRIMITIVE";
  attribute BOX_TYPE of \genblk19[3].DDR_DQS_BIBUF\ : label is "PRIMITIVE";
begin
  ENET0_GMII_TXD(7) <= \<const0>\;
  ENET0_GMII_TXD(6) <= \<const0>\;
  ENET0_GMII_TXD(5) <= \<const0>\;
  ENET0_GMII_TXD(4) <= \<const0>\;
  ENET0_GMII_TXD(3) <= \<const0>\;
  ENET0_GMII_TXD(2) <= \<const0>\;
  ENET0_GMII_TXD(1) <= \<const0>\;
  ENET0_GMII_TXD(0) <= \<const0>\;
  ENET0_GMII_TX_EN <= \<const0>\;
  ENET0_GMII_TX_ER <= \<const0>\;
  ENET1_GMII_TXD(7) <= \<const0>\;
  ENET1_GMII_TXD(6) <= \<const0>\;
  ENET1_GMII_TXD(5) <= \<const0>\;
  ENET1_GMII_TXD(4) <= \<const0>\;
  ENET1_GMII_TXD(3) <= \<const0>\;
  ENET1_GMII_TXD(2) <= \<const0>\;
  ENET1_GMII_TXD(1) <= \<const0>\;
  ENET1_GMII_TXD(0) <= \<const0>\;
  ENET1_GMII_TX_EN <= \<const0>\;
  ENET1_GMII_TX_ER <= \<const0>\;
  M_AXI_GP0_ARCACHE(3 downto 2) <= \^m_axi_gp0_arcache\(3 downto 2);
  M_AXI_GP0_ARCACHE(1) <= \<const1>\;
  M_AXI_GP0_ARCACHE(0) <= \^m_axi_gp0_arcache\(0);
  M_AXI_GP0_ARSIZE(2) <= \<const0>\;
  M_AXI_GP0_ARSIZE(1 downto 0) <= \^m_axi_gp0_arsize\(1 downto 0);
  M_AXI_GP0_AWCACHE(3 downto 2) <= \^m_axi_gp0_awcache\(3 downto 2);
  M_AXI_GP0_AWCACHE(1) <= \<const1>\;
  M_AXI_GP0_AWCACHE(0) <= \^m_axi_gp0_awcache\(0);
  M_AXI_GP0_AWSIZE(2) <= \<const0>\;
  M_AXI_GP0_AWSIZE(1 downto 0) <= \^m_axi_gp0_awsize\(1 downto 0);
  M_AXI_GP1_ARCACHE(3 downto 2) <= \^m_axi_gp1_arcache\(3 downto 2);
  M_AXI_GP1_ARCACHE(1) <= \<const1>\;
  M_AXI_GP1_ARCACHE(0) <= \^m_axi_gp1_arcache\(0);
  M_AXI_GP1_ARSIZE(2) <= \<const0>\;
  M_AXI_GP1_ARSIZE(1 downto 0) <= \^m_axi_gp1_arsize\(1 downto 0);
  M_AXI_GP1_AWCACHE(3 downto 2) <= \^m_axi_gp1_awcache\(3 downto 2);
  M_AXI_GP1_AWCACHE(1) <= \<const1>\;
  M_AXI_GP1_AWCACHE(0) <= \^m_axi_gp1_awcache\(0);
  M_AXI_GP1_AWSIZE(2) <= \<const0>\;
  M_AXI_GP1_AWSIZE(1 downto 0) <= \^m_axi_gp1_awsize\(1 downto 0);
  PJTAG_TDO <= \<const0>\;
  TRACE_CLK_OUT <= \<const0>\;
  TRACE_CTL <= \TRACE_CTL_PIPE[0]\;
  TRACE_DATA(1 downto 0) <= \TRACE_DATA_PIPE[0]\(1 downto 0);
DDR_CAS_n_BIBUF: unisim.vcomponents.BIBUF
     port map (
      IO => buffered_DDR_CAS_n,
      PAD => DDR_CAS_n
    );
DDR_CKE_BIBUF: unisim.vcomponents.BIBUF
     port map (
      IO => buffered_DDR_CKE,
      PAD => DDR_CKE
    );
DDR_CS_n_BIBUF: unisim.vcomponents.BIBUF
     port map (
      IO => buffered_DDR_CS_n,
      PAD => DDR_CS_n
    );
DDR_Clk_BIBUF: unisim.vcomponents.BIBUF
     port map (
      IO => buffered_DDR_Clk,
      PAD => DDR_Clk
    );
DDR_Clk_n_BIBUF: unisim.vcomponents.BIBUF
     port map (
      IO => buffered_DDR_Clk_n,
      PAD => DDR_Clk_n
    );
DDR_DRSTB_BIBUF: unisim.vcomponents.BIBUF
     port map (
      IO => buffered_DDR_DRSTB,
      PAD => DDR_DRSTB
    );
DDR_ODT_BIBUF: unisim.vcomponents.BIBUF
     port map (
      IO => buffered_DDR_ODT,
      PAD => DDR_ODT
    );
DDR_RAS_n_BIBUF: unisim.vcomponents.BIBUF
     port map (
      IO => buffered_DDR_RAS_n,
      PAD => DDR_RAS_n
    );
DDR_VRN_BIBUF: unisim.vcomponents.BIBUF
     port map (
      IO => buffered_DDR_VRN,
      PAD => DDR_VRN
    );
DDR_VRP_BIBUF: unisim.vcomponents.BIBUF
     port map (
      IO => buffered_DDR_VRP,
      PAD => DDR_VRP
    );
DDR_WEB_BIBUF: unisim.vcomponents.BIBUF
     port map (
      IO => buffered_DDR_WEB,
      PAD => DDR_WEB
    );
ENET0_MDIO_T_INST_0: unisim.vcomponents.LUT1
    generic map(
      INIT => X"1"
    )
        port map (
      I0 => ENET0_MDIO_T_n,
      O => ENET0_MDIO_T
    );
ENET1_MDIO_T_INST_0: unisim.vcomponents.LUT1
    generic map(
      INIT => X"1"
    )
        port map (
      I0 => ENET1_MDIO_T_n,
      O => ENET1_MDIO_T
    );
GND: unisim.vcomponents.GND
     port map (
      G => \<const0>\
    );
\GPIO_T[0]_INST_0\: unisim.vcomponents.LUT1
    generic map(
      INIT => X"1"
    )
        port map (
      I0 => gpio_out_t_n(0),
      O => GPIO_T(0)
    );
\GPIO_T[10]_INST_0\: unisim.vcomponents.LUT1
    generic map(
      INIT => X"1"
    )
        port map (
      I0 => gpio_out_t_n(10),
      O => GPIO_T(10)
    );
\GPIO_T[11]_INST_0\: unisim.vcomponents.LUT1
    generic map(
      INIT => X"1"
    )
        port map (
      I0 => gpio_out_t_n(11),
      O => GPIO_T(11)
    );
\GPIO_T[12]_INST_0\: unisim.vcomponents.LUT1
    generic map(
      INIT => X"1"
    )
        port map (
      I0 => gpio_out_t_n(12),
      O => GPIO_T(12)
    );
\GPIO_T[13]_INST_0\: unisim.vcomponents.LUT1
    generic map(
      INIT => X"1"
    )
        port map (
      I0 => gpio_out_t_n(13),
      O => GPIO_T(13)
    );
\GPIO_T[14]_INST_0\: unisim.vcomponents.LUT1
    generic map(
      INIT => X"1"
    )
        port map (
      I0 => gpio_out_t_n(14),
      O => GPIO_T(14)
    );
\GPIO_T[15]_INST_0\: unisim.vcomponents.LUT1
    generic map(
      INIT => X"1"
    )
        port map (
      I0 => gpio_out_t_n(15),
      O => GPIO_T(15)
    );
\GPIO_T[16]_INST_0\: unisim.vcomponents.LUT1
    generic map(
      INIT => X"1"
    )
        port map (
      I0 => gpio_out_t_n(16),
      O => GPIO_T(16)
    );
\GPIO_T[17]_INST_0\: unisim.vcomponents.LUT1
    generic map(
      INIT => X"1"
    )
        port map (
      I0 => gpio_out_t_n(17),
      O => GPIO_T(17)
    );
\GPIO_T[18]_INST_0\: unisim.vcomponents.LUT1
    generic map(
      INIT => X"1"
    )
        port map (
      I0 => gpio_out_t_n(18),
      O => GPIO_T(18)
    );
\GPIO_T[19]_INST_0\: unisim.vcomponents.LUT1
    generic map(
      INIT => X"1"
    )
        port map (
      I0 => gpio_out_t_n(19),
      O => GPIO_T(19)
    );
\GPIO_T[1]_INST_0\: unisim.vcomponents.LUT1
    generic map(
      INIT => X"1"
    )
        port map (
      I0 => gpio_out_t_n(1),
      O => GPIO_T(1)
    );
\GPIO_T[20]_INST_0\: unisim.vcomponents.LUT1
    generic map(
      INIT => X"1"
    )
        port map (
      I0 => gpio_out_t_n(20),
      O => GPIO_T(20)
    );
\GPIO_T[21]_INST_0\: unisim.vcomponents.LUT1
    generic map(
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
    );
\GPIO_T[61]_INST_0\: unisim.vcomponents.LUT1
    generic map(
      INIT => X"1"
    )
        port map (
      I0 => gpio_out_t_n(61),
      O => GPIO_T(61)
    );
\GPIO_T[62]_INST_0\: unisim.vcomponents.LUT1
    generic map(
      INIT => X"1"
    )
        port map (
      I0 => gpio_out_t_n(62),
      O => GPIO_T(62)
    );
\GPIO_T[63]_INST_0\: unisim.vcomponents.LUT1
    generic map(
      INIT => X"1"
    )
        port map (
      I0 => gpio_out_t_n(63),
      O => GPIO_T(63)
    );
\GPIO_T[6]_INST_0\: unisim.vcomponents.LUT1
    generic map(
      INIT => X"1"
    )
        port map (
      I0 => gpio_out_t_n(6),
      O => GPIO_T(6)
    );
\GPIO_T[7]_INST_0\: unisim.vcomponents.LUT1
    generic map(
      INIT => X"1"
    )
        port map (
      I0 => gpio_out_t_n(7),
      O => GPIO_T(7)
    );
\GPIO_T[8]_INST_0\: unisim.vcomponents.LUT1
    generic map(
      INIT => X"1"
    )
        port map (
      I0 => gpio_out_t_n(8),
      O => GPIO_T(8)
    );
\GPIO_T[9]_INST_0\: unisim.vcomponents.LUT1
    generic map(
      INIT => X"1"
    )
        port map (
      I0 => gpio_out_t_n(9),
      O => GPIO_T(9)
    );
I2C0_SCL_T_INST_0: unisim.vcomponents.LUT1
    generic map(
      INIT => X"1"
    )
        port map (
      I0 => I2C0_SCL_T_n,
      O => I2C0_SCL_T
    );
I2C0_SDA_T_INST_0: unisim.vcomponents.LUT1
    generic map(
      INIT => X"1"
    )
        port map (
      I0 => I2C0_SDA_T_n,
      O => I2C0_SDA_T
    );
I2C1_SCL_T_INST_0: unisim.vcomponents.LUT1
    generic map(
      INIT => X"1"
    )
        port map (
      I0 => I2C1_SCL_T_n,
      O => I2C1_SCL_T
    );
I2C1_SDA_T_INST_0: unisim.vcomponents.LUT1
    generic map(
      INIT => X"1"
    )
        port map (
      I0 => I2C1_SDA_T_n,
      O => I2C1_SDA_T
    );
PS7_i: unisim.vcomponents.PS7
     port map (
      DDRA(14 downto 0) => buffered_DDR_Addr(14 downto 0),
      DDRARB(3 downto 0) => DDR_ARB(3 downto 0),
      DDRBA(2 downto 0) => buffered_DDR_BankAddr(2 downto 0),
      DDRCASB => buffered_DDR_CAS_n,
      DDRCKE => buffered_DDR_CKE,
      DDRCKN => buffered_DDR_Clk_n,
      DDRCKP => buffered_DDR_Clk,
      DDRCSB => buffered_DDR_CS_n,
      DDRDM(3 downto 0) => buffered_DDR_DM(3 downto 0),
      DDRDQ(31 downto 0) => buffered_DDR_DQ(31 downto 0),
      DDRDQSN(3 downto 0) => buffered_DDR_DQS_n(3 downto 0),
      DDRDQSP(3 downto 0) => buffered_DDR_DQS(3 downto 0),
      DDRDRSTB => buffered_DDR_DRSTB,
      DDRODT => buffered_DDR_ODT,
      DDRRASB => buffered_DDR_RAS_n,
      DDRVRN => buffered_DDR_VRN,
      DDRVRP => buffered_DDR_VRP,
      DDRWEB => buffered_DDR_WEB,
      DMA0ACLK => DMA0_ACLK,
      DMA0DAREADY => DMA0_DAREADY,
      DMA0DATYPE(1 downto 0) => DMA0_DATYPE(1 downto 0),
      DMA0DAVALID => DMA0_DAVALID,
      DMA0DRLAST => DMA0_DRLAST,
      DMA0DRREADY => DMA0_DRREADY,
      DMA0DRTYPE(1 downto 0) => DMA0_DRTYPE(1 downto 0),
      DMA0DRVALID => DMA0_DRVALID,
      DMA0RSTN => DMA0_RSTN,
      DMA1ACLK => DMA1_ACLK,
      DMA1DAREADY => DMA1_DAREADY,
      DMA1DATYPE(1 downto 0) => DMA1_DATYPE(1 downto 0),
      DMA1DAVALID => DMA1_DAVALID,
      DMA1DRLAST => DMA1_DRLAST,
      DMA1DRREADY => DMA1_DRREADY,
      DMA1DRTYPE(1 downto 0) => DMA1_DRTYPE(1 downto 0),
      DMA1DRVALID => DMA1_DRVALID,
      DMA1RSTN => DMA1_RSTN,
      DMA2ACLK => DMA2_ACLK,
      DMA2DAREADY => DMA2_DAREADY,
      DMA2DATYPE(1 downto 0) => DMA2_DATYPE(1 downto 0),
      DMA2DAVALID => DMA2_DAVALID,
      DMA2DRLAST => DMA2_DRLAST,
      DMA2DRREADY => DMA2_DRREADY,
      DMA2DRTYPE(1 downto 0) => DMA2_DRTYPE(1 downto 0),
      DMA2DRVALID => DMA2_DRVALID,
      DMA2RSTN => DMA2_RSTN,
      DMA3ACLK => DMA3_ACLK,
      DMA3DAREADY => DMA3_DAREADY,
      DMA3DATYPE(1 downto 0) => DMA3_DATYPE(1 downto 0),
      DMA3DAVALID => DMA3_DAVALID,
      DMA3DRLAST => DMA3_DRLAST,
      DMA3DRREADY => DMA3_DRREADY,
      DMA3DRTYPE(1 downto 0) => DMA3_DRTYPE(1 downto 0),
      DMA3DRVALID => DMA3_DRVALID,
      DMA3RSTN => DMA3_RSTN,
      EMIOCAN0PHYRX => CAN0_PHY_RX,
      EMIOCAN0PHYTX => CAN0_PHY_TX,
      EMIOCAN1PHYRX => CAN1_PHY_RX,
      EMIOCAN1PHYTX => CAN1_PHY_TX,
      EMIOENET0EXTINTIN => ENET0_EXT_INTIN,
      EMIOENET0GMIICOL => '0',
      EMIOENET0GMIICRS => '0',
      EMIOENET0GMIIRXCLK => ENET0_GMII_RX_CLK,
      EMIOENET0GMIIRXD(7 downto 0) => B"00000000",
      EMIOENET0GMIIRXDV => '0',
      EMIOENET0GMIIRXER => '0',
      EMIOENET0GMIITXCLK => ENET0_GMII_TX_CLK,
      EMIOENET0GMIITXD(7 downto 0) => NLW_PS7_i_EMIOENET0GMIITXD_UNCONNECTED(7 downto 0),
      EMIOENET0GMIITXEN => NLW_PS7_i_EMIOENET0GMIITXEN_UNCONNECTED,
      EMIOENET0GMIITXER => NLW_PS7_i_EMIOENET0GMIITXER_UNCONNECTED,
      EMIOENET0MDIOI => ENET0_MDIO_I,
      EMIOENET0MDIOMDC => ENET0_MDIO_MDC,
      EMIOENET0MDIOO => ENET0_MDIO_O,
      EMIOENET0MDIOTN => ENET0_MDIO_T_n,
      EMIOENET0PTPDELAYREQRX => ENET0_PTP_DELAY_REQ_RX,
      EMIOENET0PTPDELAYREQTX => ENET0_PTP_DELAY_REQ_TX,
      EMIOENET0PTPPDELAYREQRX => ENET0_PTP_PDELAY_REQ_RX,
      EMIOENET0PTPPDELAYREQTX => ENET0_PTP_PDELAY_REQ_TX,
      EMIOENET0PTPPDELAYRESPRX => ENET0_PTP_PDELAY_RESP_RX,
      EMIOENET0PTPPDELAYRESPTX => ENET0_PTP_PDELAY_RESP_TX,
      EMIOENET0PTPSYNCFRAMERX => ENET0_PTP_SYNC_FRAME_RX,
      EMIOENET0PTPSYNCFRAMETX => ENET0_PTP_SYNC_FRAME_TX,
      EMIOENET0SOFRX => ENET0_SOF_RX,
      EMIOENET0SOFTX => ENET0_SOF_TX,
      EMIOENET1EXTINTIN => ENET1_EXT_INTIN,
      EMIOENET1GMIICOL => '0',
      EMIOENET1GMIICRS => '0',
      EMIOENET1GMIIRXCLK => ENET1_GMII_RX_CLK,
      EMIOENET1GMIIRXD(7 downto 0) => B"00000000",
      EMIOENET1GMIIRXDV => '0',
      EMIOENET1GMIIRXER => '0',
      EMIOENET1GMIITXCLK => ENET1_GMII_TX_CLK,
      EMIOENET1GMIITXD(7 downto 0) => NLW_PS7_i_EMIOENET1GMIITXD_UNCONNECTED(7 downto 0),
      EMIOENET1GMIITXEN => NLW_PS7_i_EMIOENET1GMIITXEN_UNCONNECTED,
      EMIOENET1GMIITXER => NLW_PS7_i_EMIOENET1GMIITXER_UNCONNECTED,
      EMIOENET1MDIOI => ENET1_MDIO_I,
      EMIOENET1MDIOMDC => ENET1_MDIO_MDC,
      EMIOENET1MDIOO => ENET1_MDIO_O,
      EMIOENET1MDIOTN => ENET1_MDIO_T_n,
      EMIOENET1PTPDELAYREQRX => ENET1_PTP_DELAY_REQ_RX,
      EMIOENET1PTPDELAYREQTX => ENET1_PTP_DELAY_REQ_TX,
      EMIOENET1PTPPDELAYREQRX => ENET1_PTP_PDELAY_REQ_RX,
      EMIOENET1PTPPDELAYREQTX => ENET1_PTP_PDELAY_REQ_TX,
      EMIOENET1PTPPDELAYRESPRX => ENET1_PTP_PDELAY_RESP_RX,
      EMIOENET1PTPPDELAYRESPTX => ENET1_PTP_PDELAY_RESP_TX,
      EMIOENET1PTPSYNCFRAMERX => ENET1_PTP_SYNC_FRAME_RX,
      EMIOENET1PTPSYNCFRAMETX => ENET1_PTP_SYNC_FRAME_TX,
      EMIOENET1SOFRX => ENET1_SOF_RX,
      EMIOENET1SOFTX => ENET1_SOF_TX,
      EMIOGPIOI(63 downto 0) => GPIO_I(63 downto 0),
      EMIOGPIOO(63 downto 0) => GPIO_O(63 downto 0),
      EMIOGPIOTN(63 downto 0) => gpio_out_t_n(63 downto 0),
      EMIOI2C0SCLI => I2C0_SCL_I,
      EMIOI2C0SCLO => I2C0_SCL_O,
      EMIOI2C0SCLTN => I2C0_SCL_T_n,
      EMIOI2C0SDAI => I2C0_SDA_I,
      EMIOI2C0SDAO => I2C0_SDA_O,
      EMIOI2C0SDATN => I2C0_SDA_T_n,
      EMIOI2C1SCLI => I2C1_SCL_I,
      EMIOI2C1SCLO => I2C1_SCL_O,
      EMIOI2C1SCLTN => I2C1_SCL_T_n,
      EMIOI2C1SDAI => I2C1_SDA_I,
      EMIOI2C1SDAO => I2C1_SDA_O,
      EMIOI2C1SDATN => I2C1_SDA_T_n,
      EMIOPJTAGTCK => PJTAG_TCK,
      EMIOPJTAGTDI => PJTAG_TDI,
      EMIOPJTAGTDO => NLW_PS7_i_EMIOPJTAGTDO_UNCONNECTED,
      EMIOPJTAGTDTN => NLW_PS7_i_EMIOPJTAGTDTN_UNCONNECTED,
      EMIOPJTAGTMS => PJTAG_TMS,
      EMIOSDIO0BUSPOW => SDIO0_BUSPOW,
      EMIOSDIO0BUSVOLT(2 downto 0) => SDIO0_BUSVOLT(2 downto 0),
      EMIOSDIO0CDN => SDIO0_CDN,
      EMIOSDIO0CLK => SDIO0_CLK,
      EMIOSDIO0CLKFB => SDIO0_CLK_FB,
      EMIOSDIO0CMDI => SDIO0_CMD_I,
      EMIOSDIO0CMDO => SDIO0_CMD_O,
      EMIOSDIO0CMDTN => SDIO0_CMD_T_n,
      EMIOSDIO0DATAI(3 downto 0) => SDIO0_DATA_I(3 downto 0),
      EMIOSDIO0DATAO(3 downto 0) => SDIO0_DATA_O(3 downto 0),
      EMIOSDIO0DATATN(3 downto 0) => SDIO0_DATA_T_n(3 downto 0),
      EMIOSDIO0LED => SDIO0_LED,
      EMIOSDIO0WP => SDIO0_WP,
      EMIOSDIO1BUSPOW => SDIO1_BUSPOW,
      EMIOSDIO1BUSVOLT(2 downto 0) => SDIO1_BUSVOLT(2 downto 0),
      EMIOSDIO1CDN => SDIO1_CDN,
      EMIOSDIO1CLK => SDIO1_CLK,
      EMIOSDIO1CLKFB => SDIO1_CLK_FB,
      EMIOSDIO1CMDI => SDIO1_CMD_I,
      EMIOSDIO1CMDO => SDIO1_CMD_O,
      EMIOSDIO1CMDTN => SDIO1_CMD_T_n,
      EMIOSDIO1DATAI(3 downto 0) => SDIO1_DATA_I(3 downto 0),
      EMIOSDIO1DATAO(3 downto 0) => SDIO1_DATA_O(3 downto 0),
      EMIOSDIO1DATATN(3 downto 0) => SDIO1_DATA_T_n(3 downto 0),
      EMIOSDIO1LED => SDIO1_LED,
      EMIOSDIO1WP => SDIO1_WP,
      EMIOSPI0MI => SPI0_MISO_I,
      EMIOSPI0MO => SPI0_MOSI_O,
      EMIOSPI0MOTN => SPI0_MOSI_T_n,
      EMIOSPI0SCLKI => SPI0_SCLK_I,
      EMIOSPI0SCLKO => SPI0_SCLK_O,
      EMIOSPI0SCLKTN => SPI0_SCLK_T_n,
      EMIOSPI0SI => SPI0_MOSI_I,
      EMIOSPI0SO => SPI0_MISO_O,
      EMIOSPI0SSIN => SPI0_SS_I,
      EMIOSPI0SSNTN => SPI0_SS_T_n,
      EMIOSPI0SSON(2) => SPI0_SS2_O,
      EMIOSPI0SSON(1) => SPI0_SS1_O,
      EMIOSPI0SSON(0) => SPI0_SS_O,
      EMIOSPI0STN => SPI0_MISO_T_n,
      EMIOSPI1MI => SPI1_MISO_I,
      EMIOSPI1MO => SPI1_MOSI_O,
      EMIOSPI1MOTN => SPI1_MOSI_T_n,
      EMIOSPI1SCLKI => SPI1_SCLK_I,
      EMIOSPI1SCLKO => SPI1_SCLK_O,
      EMIOSPI1SCLKTN => SPI1_SCLK_T_n,
      EMIOSPI1SI => SPI1_MOSI_I,
      EMIOSPI1SO => SPI1_MISO_O,
      EMIOSPI1SSIN => SPI1_SS_I,
      EMIOSPI1SSNTN => SPI1_SS_T_n,
      EMIOSPI1SSON(2) => SPI1_SS2_O,
      EMIOSPI1SSON(1) => SPI1_SS1_O,
      EMIOSPI1SSON(0) => SPI1_SS_O,
      EMIOSPI1STN => SPI1_MISO_T_n,
      EMIOSRAMINTIN => SRAM_INTIN,
      EMIOTRACECLK => TRACE_CLK,
      EMIOTRACECTL => NLW_PS7_i_EMIOTRACECTL_UNCONNECTED,
      EMIOTRACEDATA(31 downto 0) => NLW_PS7_i_EMIOTRACEDATA_UNCONNECTED(31 downto 0),
      EMIOTTC0CLKI(2) => TTC0_CLK2_IN,
      EMIOTTC0CLKI(1) => TTC0_CLK1_IN,
      EMIOTTC0CLKI(0) => TTC0_CLK0_IN,
      EMIOTTC0WAVEO(2) => TTC0_WAVE2_OUT,
      EMIOTTC0WAVEO(1) => TTC0_WAVE1_OUT,
      EMIOTTC0WAVEO(0) => TTC0_WAVE0_OUT,
      EMIOTTC1CLKI(2) => TTC1_CLK2_IN,
      EMIOTTC1CLKI(1) => TTC1_CLK1_IN,
      EMIOTTC1CLKI(0) => TTC1_CLK0_IN,
      EMIOTTC1WAVEO(2) => TTC1_WAVE2_OUT,
      EMIOTTC1WAVEO(1) => TTC1_WAVE1_OUT,
      EMIOTTC1WAVEO(0) => TTC1_WAVE0_OUT,
      EMIOUART0CTSN => UART0_CTSN,
      EMIOUART0DCDN => UART0_DCDN,
      EMIOUART0DSRN => UART0_DSRN,
      EMIOUART0DTRN => UART0_DTRN,
      EMIOUART0RIN => UART0_RIN,
      EMIOUART0RTSN => UART0_RTSN,
      EMIOUART0RX => UART0_RX,
      EMIOUART0TX => UART0_TX,
      EMIOUART1CTSN => UART1_CTSN,
      EMIOUART1DCDN => UART1_DCDN,
      EMIOUART1DSRN => UART1_DSRN,
      EMIOUART1DTRN => UART1_DTRN,
      EMIOUART1RIN => UART1_RIN,
      EMIOUART1RTSN => UART1_RTSN,
      EMIOUART1RX => UART1_RX,
      EMIOUART1TX => UART1_TX,
      EMIOUSB0PORTINDCTL(1 downto 0) => USB0_PORT_INDCTL(1 downto 0),
      EMIOUSB0VBUSPWRFAULT => USB0_VBUS_PWRFAULT,
      EMIOUSB0VBUSPWRSELECT => USB0_VBUS_PWRSELECT,
      EMIOUSB1PORTINDCTL(1 downto 0) => USB1_PORT_INDCTL(1 downto 0),
      EMIOUSB1VBUSPWRFAULT => USB1_VBUS_PWRFAULT,
      EMIOUSB1VBUSPWRSELECT => USB1_VBUS_PWRSELECT,
      EMIOWDTCLKI => WDT_CLK_IN,
      EMIOWDTRSTO => WDT_RST_OUT,
      EVENTEVENTI => EVENT_EVENTI,
      EVENTEVENTO => EVENT_EVENTO,
      EVENTSTANDBYWFE(1 downto 0) => EVENT_STANDBYWFE(1 downto 0),
      EVENTSTANDBYWFI(1 downto 0) => EVENT_STANDBYWFI(1 downto 0),
      FCLKCLK(3) => FCLK_CLK3,
      FCLKCLK(2) => FCLK_CLK2,
      FCLKCLK(1) => FCLK_CLK1,
      FCLKCLK(0) => FCLK_CLK_unbuffered(0),
      FCLKCLKTRIGN(3 downto 0) => B"0000",
      FCLKRESETN(3) => FCLK_RESET3_N,
      FCLKRESETN(2) => FCLK_RESET2_N,
      FCLKRESETN(1) => FCLK_RESET1_N,
      FCLKRESETN(0) => FCLK_RESET0_N,
      FPGAIDLEN => FPGA_IDLE_N,
      FTMDTRACEINATID(3 downto 0) => B"0000",
      FTMDTRACEINCLOCK => FTMD_TRACEIN_CLK,
      FTMDTRACEINDATA(31 downto 0) => B"00000000000000000000000000000000",
      FTMDTRACEINVALID => '0',
      FTMTF2PDEBUG(31 downto 0) => FTMT_F2P_DEBUG(31 downto 0),
      FTMTF2PTRIG(3) => FTMT_F2P_TRIG_3,
      FTMTF2PTRIG(2) => FTMT_F2P_TRIG_2,
      FTMTF2PTRIG(1) => FTMT_F2P_TRIG_1,
      FTMTF2PTRIG(0) => FTMT_F2P_TRIG_0,
      FTMTF2PTRIGACK(3) => FTMT_F2P_TRIGACK_3,
      FTMTF2PTRIGACK(2) => FTMT_F2P_TRIGACK_2,
      FTMTF2PTRIGACK(1) => FTMT_F2P_TRIGACK_1,
      FTMTF2PTRIGACK(0) => FTMT_F2P_TRIGACK_0,
      FTMTP2FDEBUG(31 downto 0) => FTMT_P2F_DEBUG(31 downto 0),
      FTMTP2FTRIG(3) => FTMT_P2F_TRIG_3,
      FTMTP2FTRIG(2) => FTMT_P2F_TRIG_2,
      FTMTP2FTRIG(1) => FTMT_P2F_TRIG_1,
      FTMTP2FTRIG(0) => FTMT_P2F_TRIG_0,
      FTMTP2FTRIGACK(3) => FTMT_P2F_TRIGACK_3,
      FTMTP2FTRIGACK(2) => FTMT_P2F_TRIGACK_2,
      FTMTP2FTRIGACK(1) => FTMT_P2F_TRIGACK_1,
      FTMTP2FTRIGACK(0) => FTMT_P2F_TRIGACK_0,
      IRQF2P(19) => Core1_nFIQ,
      IRQF2P(18) => Core0_nFIQ,
      IRQF2P(17) => Core1_nIRQ,
      IRQF2P(16) => Core0_nIRQ,
      IRQF2P(15 downto 1) => B"000000000000000",
      IRQF2P(0) => IRQ_F2P(0),
      IRQP2F(28) => IRQ_P2F_DMAC_ABORT,
      IRQP2F(27) => IRQ_P2F_DMAC7,
      IRQP2F(26) => IRQ_P2F_DMAC6,
      IRQP2F(25) => IRQ_P2F_DMAC5,
      IRQP2F(24) => IRQ_P2F_DMAC4,
      IRQP2F(23) => IRQ_P2F_DMAC3,
      IRQP2F(22) => IRQ_P2F_DMAC2,
      IRQP2F(21) => IRQ_P2F_DMAC1,
      IRQP2F(20) => IRQ_P2F_DMAC0,
      IRQP2F(19) => IRQ_P2F_SMC,
      IRQP2F(18) => IRQ_P2F_QSPI,
      IRQP2F(17) => IRQ_P2F_CTI,
      IRQP2F(16) => IRQ_P2F_GPIO,
      IRQP2F(15) => IRQ_P2F_USB0,
      IRQP2F(14) => IRQ_P2F_ENET0,
      IRQP2F(13) => IRQ_P2F_ENET_WAKE0,
      IRQP2F(12) => IRQ_P2F_SDIO0,
      IRQP2F(11) => IRQ_P2F_I2C0,
      IRQP2F(10) => IRQ_P2F_SPI0,
      IRQP2F(9) => IRQ_P2F_UART0,
      IRQP2F(8) => IRQ_P2F_CAN0,
      IRQP2F(7) => IRQ_P2F_USB1,
      IRQP2F(6) => IRQ_P2F_ENET1,
      IRQP2F(5) => IRQ_P2F_ENET_WAKE1,
      IRQP2F(4) => IRQ_P2F_SDIO1,
      IRQP2F(3) => IRQ_P2F_I2C1,
      IRQP2F(2) => IRQ_P2F_SPI1,
      IRQP2F(1) => IRQ_P2F_UART1,
      IRQP2F(0) => IRQ_P2F_CAN1,
      MAXIGP0ACLK => M_AXI_GP0_ACLK,
      MAXIGP0ARADDR(31 downto 0) => M_AXI_GP0_ARADDR(31 downto 0),
      MAXIGP0ARBURST(1 downto 0) => M_AXI_GP0_ARBURST(1 downto 0),
      MAXIGP0ARCACHE(3 downto 2) => \^m_axi_gp0_arcache\(3 downto 2),
      MAXIGP0ARCACHE(1) => NLW_PS7_i_MAXIGP0ARCACHE_UNCONNECTED(1),
      MAXIGP0ARCACHE(0) => \^m_axi_gp0_arcache\(0),
      MAXIGP0ARESETN => M_AXI_GP0_ARESETN,
      MAXIGP0ARID(11 downto 0) => M_AXI_GP0_ARID(11 downto 0),
      MAXIGP0ARLEN(3 downto 0) => M_AXI_GP0_ARLEN(3 downto 0),
      MAXIGP0ARLOCK(1 downto 0) => M_AXI_GP0_ARLOCK(1 downto 0),
      MAXIGP0ARPROT(2 downto 0) => M_AXI_GP0_ARPROT(2 downto 0),
      MAXIGP0ARQOS(3 downto 0) => M_AXI_GP0_ARQOS(3 downto 0),
      MAXIGP0ARREADY => M_AXI_GP0_ARREADY,
      MAXIGP0ARSIZE(1 downto 0) => \^m_axi_gp0_arsize\(1 downto 0),
      MAXIGP0ARVALID => M_AXI_GP0_ARVALID,
      MAXIGP0AWADDR(31 downto 0) => M_AXI_GP0_AWADDR(31 downto 0),
      MAXIGP0AWBURST(1 downto 0) => M_AXI_GP0_AWBURST(1 downto 0),
      MAXIGP0AWCACHE(3 downto 2) => \^m_axi_gp0_awcache\(3 downto 2),
      MAXIGP0AWCACHE(1) => NLW_PS7_i_MAXIGP0AWCACHE_UNCONNECTED(1),
      MAXIGP0AWCACHE(0) => \^m_axi_gp0_awcache\(0),
      MAXIGP0AWID(11 downto 0) => M_AXI_GP0_AWID(11 downto 0),
      MAXIGP0AWLEN(3 downto 0) => M_AXI_GP0_AWLEN(3 downto 0),
      MAXIGP0AWLOCK(1 downto 0) => M_AXI_GP0_AWLOCK(1 downto 0),
      MAXIGP0AWPROT(2 downto 0) => M_AXI_GP0_AWPROT(2 downto 0),
      MAXIGP0AWQOS(3 downto 0) => M_AXI_GP0_AWQOS(3 downto 0),
      MAXIGP0AWREADY => M_AXI_GP0_AWREADY,
      MAXIGP0AWSIZE(1 downto 0) => \^m_axi_gp0_awsize\(1 downto 0),
      MAXIGP0AWVALID => M_AXI_GP0_AWVALID,
      MAXIGP0BID(11 downto 0) => M_AXI_GP0_BID(11 downto 0),
      MAXIGP0BREADY => M_AXI_GP0_BREADY,
      MAXIGP0BRESP(1 downto 0) => M_AXI_GP0_BRESP(1 downto 0),
      MAXIGP0BVALID => M_AXI_GP0_BVALID,
      MAXIGP0RDATA(31 downto 0) => M_AXI_GP0_RDATA(31 downto 0),
      MAXIGP0RID(11 downto 0) => M_AXI_GP0_RID(11 downto 0),
      MAXIGP0RLAST => M_AXI_GP0_RLAST,
      MAXIGP0RREADY => M_AXI_GP0_RREADY,
      MAXIGP0RRESP(1 downto 0) => M_AXI_GP0_RRESP(1 downto 0),
      MAXIGP0RVALID => M_AXI_GP0_RVALID,
      MAXIGP0WDATA(31 downto 0) => M_AXI_GP0_WDATA(31 downto 0),
      MAXIGP0WID(11 downto 0) => M_AXI_GP0_WID(11 downto 0),
      MAXIGP0WLAST => M_AXI_GP0_WLAST,
      MAXIGP0WREADY => M_AXI_GP0_WREADY,
      MAXIGP0WSTRB(3 downto 0) => M_AXI_GP0_WSTRB(3 downto 0),
      MAXIGP0WVALID => M_AXI_GP0_WVALID,
      MAXIGP1ACLK => M_AXI_GP1_ACLK,
      MAXIGP1ARADDR(31 downto 0) => M_AXI_GP1_ARADDR(31 downto 0),
      MAXIGP1ARBURST(1 downto 0) => M_AXI_GP1_ARBURST(1 downto 0),
      MAXIGP1ARCACHE(3 downto 2) => \^m_axi_gp1_arcache\(3 downto 2),
      MAXIGP1ARCACHE(1) => NLW_PS7_i_MAXIGP1ARCACHE_UNCONNECTED(1),
      MAXIGP1ARCACHE(0) => \^m_axi_gp1_arcache\(0),
      MAXIGP1ARESETN => M_AXI_GP1_ARESETN,
      MAXIGP1ARID(11 downto 0) => M_AXI_GP1_ARID(11 downto 0),
      MAXIGP1ARLEN(3 downto 0) => M_AXI_GP1_ARLEN(3 downto 0),
      MAXIGP1ARLOCK(1 downto 0) => M_AXI_GP1_ARLOCK(1 downto 0),
      MAXIGP1ARPROT(2 downto 0) => M_AXI_GP1_ARPROT(2 downto 0),
      MAXIGP1ARQOS(3 downto 0) => M_AXI_GP1_ARQOS(3 downto 0),
      MAXIGP1ARREADY => M_AXI_GP1_ARREADY,
      MAXIGP1ARSIZE(1 downto 0) => \^m_axi_gp1_arsize\(1 downto 0),
      MAXIGP1ARVALID => M_AXI_GP1_ARVALID,
      MAXIGP1AWADDR(31 downto 0) => M_AXI_GP1_AWADDR(31 downto 0),
      MAXIGP1AWBURST(1 downto 0) => M_AXI_GP1_AWBURST(1 downto 0),
      MAXIGP1AWCACHE(3 downto 2) => \^m_axi_gp1_awcache\(3 downto 2),
      MAXIGP1AWCACHE(1) => NLW_PS7_i_MAXIGP1AWCACHE_UNCONNECTED(1),
      MAXIGP1AWCACHE(0) => \^m_axi_gp1_awcache\(0),
      MAXIGP1AWID(11 downto 0) => M_AXI_GP1_AWID(11 downto 0),
      MAXIGP1AWLEN(3 downto 0) => M_AXI_GP1_AWLEN(3 downto 0),
      MAXIGP1AWLOCK(1 downto 0) => M_AXI_GP1_AWLOCK(1 downto 0),
      MAXIGP1AWPROT(2 downto 0) => M_AXI_GP1_AWPROT(2 downto 0),
      MAXIGP1AWQOS(3 downto 0) => M_AXI_GP1_AWQOS(3 downto 0),
      MAXIGP1AWREADY => M_AXI_GP1_AWREADY,
      MAXIGP1AWSIZE(1 downto 0) => \^m_axi_gp1_awsize\(1 downto 0),
      MAXIGP1AWVALID => M_AXI_GP1_AWVALID,
      MAXIGP1BID(11 downto 0) => M_AXI_GP1_BID(11 downto 0),
      MAXIGP1BREADY => M_AXI_GP1_BREADY,
      MAXIGP1BRESP(1 downto 0) => M_AXI_GP1_BRESP(1 downto 0),
      MAXIGP1BVALID => M_AXI_GP1_BVALID,
      MAXIGP1RDATA(31 downto 0) => M_AXI_GP1_RDATA(31 downto 0),
      MAXIGP1RID(11 downto 0) => M_AXI_GP1_RID(11 downto 0),
      MAXIGP1RLAST => M_AXI_GP1_RLAST,
      MAXIGP1RREADY => M_AXI_GP1_RREADY,
      MAXIGP1RRESP(1 downto 0) => M_AXI_GP1_RRESP(1 downto 0),
      MAXIGP1RVALID => M_AXI_GP1_RVALID,
      MAXIGP1WDATA(31 downto 0) => M_AXI_GP1_WDATA(31 downto 0),
      MAXIGP1WID(11 downto 0) => M_AXI_GP1_WID(11 downto 0),
      MAXIGP1WLAST => M_AXI_GP1_WLAST,
      MAXIGP1WREADY => M_AXI_GP1_WREADY,
      MAXIGP1WSTRB(3 downto 0) => M_AXI_GP1_WSTRB(3 downto 0),
      MAXIGP1WVALID => M_AXI_GP1_WVALID,
      MIO(53 downto 0) => buffered_MIO(53 downto 0),
      PSCLK => buffered_PS_CLK,
      PSPORB => buffered_PS_PORB,
      PSSRSTB => buffered_PS_SRSTB,
      SAXIACPACLK => S_AXI_ACP_ACLK,
      SAXIACPARADDR(31 downto 0) => S_AXI_ACP_ARADDR(31 downto 0),
      SAXIACPARBURST(1 downto 0) => S_AXI_ACP_ARBURST(1 downto 0),
      SAXIACPARCACHE(3 downto 0) => S_AXI_ACP_ARCACHE(3 downto 0),
      SAXIACPARESETN => S_AXI_ACP_ARESETN,
      SAXIACPARID(2 downto 0) => S_AXI_ACP_ARID(2 downto 0),
      SAXIACPARLEN(3 downto 0) => S_AXI_ACP_ARLEN(3 downto 0),
      SAXIACPARLOCK(1 downto 0) => S_AXI_ACP_ARLOCK(1 downto 0),
      SAXIACPARPROT(2 downto 0) => S_AXI_ACP_ARPROT(2 downto 0),
      SAXIACPARQOS(3 downto 0) => S_AXI_ACP_ARQOS(3 downto 0),
      SAXIACPARREADY => S_AXI_ACP_ARREADY,
      SAXIACPARSIZE(1 downto 0) => S_AXI_ACP_ARSIZE(1 downto 0),
      SAXIACPARUSER(4 downto 0) => S_AXI_ACP_ARUSER(4 downto 0),
      SAXIACPARVALID => S_AXI_ACP_ARVALID,
      SAXIACPAWADDR(31 downto 0) => S_AXI_ACP_AWADDR(31 downto 0),
      SAXIACPAWBURST(1 downto 0) => S_AXI_ACP_AWBURST(1 downto 0),
      SAXIACPAWCACHE(3 downto 0) => S_AXI_ACP_AWCACHE(3 downto 0),
      SAXIACPAWID(2 downto 0) => S_AXI_ACP_AWID(2 downto 0),
      SAXIACPAWLEN(3 downto 0) => S_AXI_ACP_AWLEN(3 downto 0),
      SAXIACPAWLOCK(1 downto 0) => S_AXI_ACP_AWLOCK(1 downto 0),
      SAXIACPAWPROT(2 downto 0) => S_AXI_ACP_AWPROT(2 downto 0),
      SAXIACPAWQOS(3 downto 0) => S_AXI_ACP_AWQOS(3 downto 0),
      SAXIACPAWREADY => S_AXI_ACP_AWREADY,
      SAXIACPAWSIZE(1 downto 0) => S_AXI_ACP_AWSIZE(1 downto 0),
      SAXIACPAWUSER(4 downto 0) => S_AXI_ACP_AWUSER(4 downto 0),
      SAXIACPAWVALID => S_AXI_ACP_AWVALID,
      SAXIACPBID(2 downto 0) => S_AXI_ACP_BID(2 downto 0),
      SAXIACPBREADY => S_AXI_ACP_BREADY,
      SAXIACPBRESP(1 downto 0) => S_AXI_ACP_BRESP(1 downto 0),
      SAXIACPBVALID => S_AXI_ACP_BVALID,
      SAXIACPRDATA(63 downto 0) => S_AXI_ACP_RDATA(63 downto 0),
      SAXIACPRID(2 downto 0) => S_AXI_ACP_RID(2 downto 0),
      SAXIACPRLAST => S_AXI_ACP_RLAST,
      SAXIACPRREADY => S_AXI_ACP_RREADY,
      SAXIACPRRESP(1 downto 0) => S_AXI_ACP_RRESP(1 downto 0),
      SAXIACPRVALID => S_AXI_ACP_RVALID,
      SAXIACPWDATA(63 downto 0) => S_AXI_ACP_WDATA(63 downto 0),
      SAXIACPWID(2 downto 0) => S_AXI_ACP_WID(2 downto 0),
      SAXIACPWLAST => S_AXI_ACP_WLAST,
      SAXIACPWREADY => S_AXI_ACP_WREADY,
      SAXIACPWSTRB(7 downto 0) => S_AXI_ACP_WSTRB(7 downto 0),
      SAXIACPWVALID => S_AXI_ACP_WVALID,
      SAXIGP0ACLK => S_AXI_GP0_ACLK,
      SAXIGP0ARADDR(31 downto 0) => S_AXI_GP0_ARADDR(31 downto 0),
      SAXIGP0ARBURST(1 downto 0) => S_AXI_GP0_ARBURST(1 downto 0),
      SAXIGP0ARCACHE(3 downto 0) => S_AXI_GP0_ARCACHE(3 downto 0),
      SAXIGP0ARESETN => S_AXI_GP0_ARESETN,
      SAXIGP0ARID(5 downto 0) => S_AXI_GP0_ARID(5 downto 0),
      SAXIGP0ARLEN(3 downto 0) => S_AXI_GP0_ARLEN(3 downto 0),
      SAXIGP0ARLOCK(1 downto 0) => S_AXI_GP0_ARLOCK(1 downto 0),
      SAXIGP0ARPROT(2 downto 0) => S_AXI_GP0_ARPROT(2 downto 0),
      SAXIGP0ARQOS(3 downto 0) => S_AXI_GP0_ARQOS(3 downto 0),
      SAXIGP0ARREADY => S_AXI_GP0_ARREADY,
      SAXIGP0ARSIZE(1 downto 0) => S_AXI_GP0_ARSIZE(1 downto 0),
      SAXIGP0ARVALID => S_AXI_GP0_ARVALID,
      SAXIGP0AWADDR(31 downto 0) => S_AXI_GP0_AWADDR(31 downto 0),
      SAXIGP0AWBURST(1 downto 0) => S_AXI_GP0_AWBURST(1 downto 0),
      SAXIGP0AWCACHE(3 downto 0) => S_AXI_GP0_AWCACHE(3 downto 0),
      SAXIGP0AWID(5 downto 0) => S_AXI_GP0_AWID(5 downto 0),
      SAXIGP0AWLEN(3 downto 0) => S_AXI_GP0_AWLEN(3 downto 0),
      SAXIGP0AWLOCK(1 downto 0) => S_AXI_GP0_AWLOCK(1 downto 0),
      SAXIGP0AWPROT(2 downto 0) => S_AXI_GP0_AWPROT(2 downto 0),
      SAXIGP0AWQOS(3 downto 0) => S_AXI_GP0_AWQOS(3 downto 0),
      SAXIGP0AWREADY => S_AXI_GP0_AWREADY,
      SAXIGP0AWSIZE(1 downto 0) => S_AXI_GP0_AWSIZE(1 downto 0),
      SAXIGP0AWVALID => S_AXI_GP0_AWVALID,
      SAXIGP0BID(5 downto 0) => S_AXI_GP0_BID(5 downto 0),
      SAXIGP0BREADY => S_AXI_GP0_BREADY,
      SAXIGP0BRESP(1 downto 0) => S_AXI_GP0_BRESP(1 downto 0),
      SAXIGP0BVALID => S_AXI_GP0_BVALID,
      SAXIGP0RDATA(31 downto 0) => S_AXI_GP0_RDATA(31 downto 0),
      SAXIGP0RID(5 downto 0) => S_AXI_GP0_RID(5 downto 0),
      SAXIGP0RLAST => S_AXI_GP0_RLAST,
      SAXIGP0RREADY => S_AXI_GP0_RREADY,
      SAXIGP0RRESP(1 downto 0) => S_AXI_GP0_RRESP(1 downto 0),
      SAXIGP0RVALID => S_AXI_GP0_RVALID,
      SAXIGP0WDATA(31 downto 0) => S_AXI_GP0_WDATA(31 downto 0),
      SAXIGP0WID(5 downto 0) => S_AXI_GP0_WID(5 downto 0),
      SAXIGP0WLAST => S_AXI_GP0_WLAST,
      SAXIGP0WREADY => S_AXI_GP0_WREADY,
      SAXIGP0WSTRB(3 downto 0) => S_AXI_GP0_WSTRB(3 downto 0),
      SAXIGP0WVALID => S_AXI_GP0_WVALID,
      SAXIGP1ACLK => S_AXI_GP1_ACLK,
      SAXIGP1ARADDR(31 downto 0) => S_AXI_GP1_ARADDR(31 downto 0),
      SAXIGP1ARBURST(1 downto 0) => S_AXI_GP1_ARBURST(1 downto 0),
      SAXIGP1ARCACHE(3 downto 0) => S_AXI_GP1_ARCACHE(3 downto 0),
      SAXIGP1ARESETN => S_AXI_GP1_ARESETN,
      SAXIGP1ARID(5 downto 0) => S_AXI_GP1_ARID(5 downto 0),
      SAXIGP1ARLEN(3 downto 0) => S_AXI_GP1_ARLEN(3 downto 0),
      SAXIGP1ARLOCK(1 downto 0) => S_AXI_GP1_ARLOCK(1 downto 0),
      SAXIGP1ARPROT(2 downto 0) => S_AXI_GP1_ARPROT(2 downto 0),
      SAXIGP1ARQOS(3 downto 0) => S_AXI_GP1_ARQOS(3 downto 0),
      SAXIGP1ARREADY => S_AXI_GP1_ARREADY,
      SAXIGP1ARSIZE(1 downto 0) => S_AXI_GP1_ARSIZE(1 downto 0),
      SAXIGP1ARVALID => S_AXI_GP1_ARVALID,
      SAXIGP1AWADDR(31 downto 0) => S_AXI_GP1_AWADDR(31 downto 0),
      SAXIGP1AWBURST(1 downto 0) => S_AXI_GP1_AWBURST(1 downto 0),
      SAXIGP1AWCACHE(3 downto 0) => S_AXI_GP1_AWCACHE(3 downto 0),
      SAXIGP1AWID(5 downto 0) => S_AXI_GP1_AWID(5 downto 0),
      SAXIGP1AWLEN(3 downto 0) => S_AXI_GP1_AWLEN(3 downto 0),
      SAXIGP1AWLOCK(1 downto 0) => S_AXI_GP1_AWLOCK(1 downto 0),
      SAXIGP1AWPROT(2 downto 0) => S_AXI_GP1_AWPROT(2 downto 0),
      SAXIGP1AWQOS(3 downto 0) => S_AXI_GP1_AWQOS(3 downto 0),
      SAXIGP1AWREADY => S_AXI_GP1_AWREADY,
      SAXIGP1AWSIZE(1 downto 0) => S_AXI_GP1_AWSIZE(1 downto 0),
      SAXIGP1AWVALID => S_AXI_GP1_AWVALID,
      SAXIGP1BID(5 downto 0) => S_AXI_GP1_BID(5 downto 0),
      SAXIGP1BREADY => S_AXI_GP1_BREADY,
      SAXIGP1BRESP(1 downto 0) => S_AXI_GP1_BRESP(1 downto 0),
      SAXIGP1BVALID => S_AXI_GP1_BVALID,
      SAXIGP1RDATA(31 downto 0) => S_AXI_GP1_RDATA(31 downto 0),
      SAXIGP1RID(5 downto 0) => S_AXI_GP1_RID(5 downto 0),
      SAXIGP1RLAST => S_AXI_GP1_RLAST,
      SAXIGP1RREADY => S_AXI_GP1_RREADY,
      SAXIGP1RRESP(1 downto 0) => S_AXI_GP1_RRESP(1 downto 0),
      SAXIGP1RVALID => S_AXI_GP1_RVALID,
      SAXIGP1WDATA(31 downto 0) => S_AXI_GP1_WDATA(31 downto 0),
      SAXIGP1WID(5 downto 0) => S_AXI_GP1_WID(5 downto 0),
      SAXIGP1WLAST => S_AXI_GP1_WLAST,
      SAXIGP1WREADY => S_AXI_GP1_WREADY,
      SAXIGP1WSTRB(3 downto 0) => S_AXI_GP1_WSTRB(3 downto 0),
      SAXIGP1WVALID => S_AXI_GP1_WVALID,
      SAXIHP0ACLK => S_AXI_HP0_ACLK,
      SAXIHP0ARADDR(31 downto 0) => S_AXI_HP0_ARADDR(31 downto 0),
      SAXIHP0ARBURST(1 downto 0) => S_AXI_HP0_ARBURST(1 downto 0),
      SAXIHP0ARCACHE(3 downto 0) => S_AXI_HP0_ARCACHE(3 downto 0),
      SAXIHP0ARESETN => S_AXI_HP0_ARESETN,
      SAXIHP0ARID(5 downto 0) => S_AXI_HP0_ARID(5 downto 0),
      SAXIHP0ARLEN(3 downto 0) => S_AXI_HP0_ARLEN(3 downto 0),
      SAXIHP0ARLOCK(1 downto 0) => S_AXI_HP0_ARLOCK(1 downto 0),
      SAXIHP0ARPROT(2 downto 0) => S_AXI_HP0_ARPROT(2 downto 0),
      SAXIHP0ARQOS(3 downto 0) => S_AXI_HP0_ARQOS(3 downto 0),
      SAXIHP0ARREADY => S_AXI_HP0_ARREADY,
      SAXIHP0ARSIZE(1 downto 0) => S_AXI_HP0_ARSIZE(1 downto 0),
      SAXIHP0ARVALID => S_AXI_HP0_ARVALID,
      SAXIHP0AWADDR(31 downto 0) => S_AXI_HP0_AWADDR(31 downto 0),
      SAXIHP0AWBURST(1 downto 0) => S_AXI_HP0_AWBURST(1 downto 0),
      SAXIHP0AWCACHE(3 downto 0) => S_AXI_HP0_AWCACHE(3 downto 0),
      SAXIHP0AWID(5 downto 0) => S_AXI_HP0_AWID(5 downto 0),
      SAXIHP0AWLEN(3 downto 0) => S_AXI_HP0_AWLEN(3 downto 0),
      SAXIHP0AWLOCK(1 downto 0) => S_AXI_HP0_AWLOCK(1 downto 0),
      SAXIHP0AWPROT(2 downto 0) => S_AXI_HP0_AWPROT(2 downto 0),
      SAXIHP0AWQOS(3 downto 0) => S_AXI_HP0_AWQOS(3 downto 0),
      SAXIHP0AWREADY => S_AXI_HP0_AWREADY,
      SAXIHP0AWSIZE(1 downto 0) => S_AXI_HP0_AWSIZE(1 downto 0),
      SAXIHP0AWVALID => S_AXI_HP0_AWVALID,
      SAXIHP0BID(5 downto 0) => S_AXI_HP0_BID(5 downto 0),
      SAXIHP0BREADY => S_AXI_HP0_BREADY,
      SAXIHP0BRESP(1 downto 0) => S_AXI_HP0_BRESP(1 downto 0),
      SAXIHP0BVALID => S_AXI_HP0_BVALID,
      SAXIHP0RACOUNT(2 downto 0) => S_AXI_HP0_RACOUNT(2 downto 0),
      SAXIHP0RCOUNT(7 downto 0) => S_AXI_HP0_RCOUNT(7 downto 0),
      SAXIHP0RDATA(63 downto 0) => S_AXI_HP0_RDATA(63 downto 0),
      SAXIHP0RDISSUECAP1EN => S_AXI_HP0_RDISSUECAP1_EN,
      SAXIHP0RID(5 downto 0) => S_AXI_HP0_RID(5 downto 0),
      SAXIHP0RLAST => S_AXI_HP0_RLAST,
      SAXIHP0RREADY => S_AXI_HP0_RREADY,
      SAXIHP0RRESP(1 downto 0) => S_AXI_HP0_RRESP(1 downto 0),
      SAXIHP0RVALID => S_AXI_HP0_RVALID,
      SAXIHP0WACOUNT(5 downto 0) => S_AXI_HP0_WACOUNT(5 downto 0),
      SAXIHP0WCOUNT(7 downto 0) => S_AXI_HP0_WCOUNT(7 downto 0),
      SAXIHP0WDATA(63 downto 0) => S_AXI_HP0_WDATA(63 downto 0),
      SAXIHP0WID(5 downto 0) => S_AXI_HP0_WID(5 downto 0),
      SAXIHP0WLAST => S_AXI_HP0_WLAST,
      SAXIHP0WREADY => S_AXI_HP0_WREADY,
      SAXIHP0WRISSUECAP1EN => S_AXI_HP0_WRISSUECAP1_EN,
      SAXIHP0WSTRB(7 downto 0) => S_AXI_HP0_WSTRB(7 downto 0),
      SAXIHP0WVALID => S_AXI_HP0_WVALID,
      SAXIHP1ACLK => S_AXI_HP1_ACLK,
      SAXIHP1ARADDR(31 downto 0) => S_AXI_HP1_ARADDR(31 downto 0),
      SAXIHP1ARBURST(1 downto 0) => S_AXI_HP1_ARBURST(1 downto 0),
      SAXIHP1ARCACHE(3 downto 0) => S_AXI_HP1_ARCACHE(3 downto 0),
      SAXIHP1ARESETN => S_AXI_HP1_ARESETN,
      SAXIHP1ARID(5 downto 0) => S_AXI_HP1_ARID(5 downto 0),
      SAXIHP1ARLEN(3 downto 0) => S_AXI_HP1_ARLEN(3 downto 0),
      SAXIHP1ARLOCK(1 downto 0) => S_AXI_HP1_ARLOCK(1 downto 0),
      SAXIHP1ARPROT(2 downto 0) => S_AXI_HP1_ARPROT(2 downto 0),
      SAXIHP1ARQOS(3 downto 0) => S_AXI_HP1_ARQOS(3 downto 0),
      SAXIHP1ARREADY => S_AXI_HP1_ARREADY,
      SAXIHP1ARSIZE(1 downto 0) => S_AXI_HP1_ARSIZE(1 downto 0),
      SAXIHP1ARVALID => S_AXI_HP1_ARVALID,
      SAXIHP1AWADDR(31 downto 0) => S_AXI_HP1_AWADDR(31 downto 0),
      SAXIHP1AWBURST(1 downto 0) => S_AXI_HP1_AWBURST(1 downto 0),
      SAXIHP1AWCACHE(3 downto 0) => S_AXI_HP1_AWCACHE(3 downto 0),
      SAXIHP1AWID(5 downto 0) => S_AXI_HP1_AWID(5 downto 0),
      SAXIHP1AWLEN(3 downto 0) => S_AXI_HP1_AWLEN(3 downto 0),
      SAXIHP1AWLOCK(1 downto 0) => S_AXI_HP1_AWLOCK(1 downto 0),
      SAXIHP1AWPROT(2 downto 0) => S_AXI_HP1_AWPROT(2 downto 0),
      SAXIHP1AWQOS(3 downto 0) => S_AXI_HP1_AWQOS(3 downto 0),
      SAXIHP1AWREADY => S_AXI_HP1_AWREADY,
      SAXIHP1AWSIZE(1 downto 0) => S_AXI_HP1_AWSIZE(1 downto 0),
      SAXIHP1AWVALID => S_AXI_HP1_AWVALID,
      SAXIHP1BID(5 downto 0) => S_AXI_HP1_BID(5 downto 0),
      SAXIHP1BREADY => S_AXI_HP1_BREADY,
      SAXIHP1BRESP(1 downto 0) => S_AXI_HP1_BRESP(1 downto 0),
      SAXIHP1BVALID => S_AXI_HP1_BVALID,
      SAXIHP1RACOUNT(2 downto 0) => S_AXI_HP1_RACOUNT(2 downto 0),
      SAXIHP1RCOUNT(7 downto 0) => S_AXI_HP1_RCOUNT(7 downto 0),
      SAXIHP1RDATA(63 downto 0) => S_AXI_HP1_RDATA(63 downto 0),
      SAXIHP1RDISSUECAP1EN => S_AXI_HP1_RDISSUECAP1_EN,
      SAXIHP1RID(5 downto 0) => S_AXI_HP1_RID(5 downto 0),
      SAXIHP1RLAST => S_AXI_HP1_RLAST,
      SAXIHP1RREADY => S_AXI_HP1_RREADY,
      SAXIHP1RRESP(1 downto 0) => S_AXI_HP1_RRESP(1 downto 0),
      SAXIHP1RVALID => S_AXI_HP1_RVALID,
      SAXIHP1WACOUNT(5 downto 0) => S_AXI_HP1_WACOUNT(5 downto 0),
      SAXIHP1WCOUNT(7 downto 0) => S_AXI_HP1_WCOUNT(7 downto 0),
      SAXIHP1WDATA(63 downto 0) => S_AXI_HP1_WDATA(63 downto 0),
      SAXIHP1WID(5 downto 0) => S_AXI_HP1_WID(5 downto 0),
      SAXIHP1WLAST => S_AXI_HP1_WLAST,
      SAXIHP1WREADY => S_AXI_HP1_WREADY,
      SAXIHP1WRISSUECAP1EN => S_AXI_HP1_WRISSUECAP1_EN,
      SAXIHP1WSTRB(7 downto 0) => S_AXI_HP1_WSTRB(7 downto 0),
      SAXIHP1WVALID => S_AXI_HP1_WVALID,
      SAXIHP2ACLK => S_AXI_HP2_ACLK,
      SAXIHP2ARADDR(31 downto 0) => S_AXI_HP2_ARADDR(31 downto 0),
      SAXIHP2ARBURST(1 downto 0) => S_AXI_HP2_ARBURST(1 downto 0),
      SAXIHP2ARCACHE(3 downto 0) => S_AXI_HP2_ARCACHE(3 downto 0),
      SAXIHP2ARESETN => S_AXI_HP2_ARESETN,
      SAXIHP2ARID(5 downto 0) => S_AXI_HP2_ARID(5 downto 0),
      SAXIHP2ARLEN(3 downto 0) => S_AXI_HP2_ARLEN(3 downto 0),
      SAXIHP2ARLOCK(1 downto 0) => S_AXI_HP2_ARLOCK(1 downto 0),
      SAXIHP2ARPROT(2 downto 0) => S_AXI_HP2_ARPROT(2 downto 0),
      SAXIHP2ARQOS(3 downto 0) => S_AXI_HP2_ARQOS(3 downto 0),
      SAXIHP2ARREADY => S_AXI_HP2_ARREADY,
      SAXIHP2ARSIZE(1 downto 0) => S_AXI_HP2_ARSIZE(1 downto 0),
      SAXIHP2ARVALID => S_AXI_HP2_ARVALID,
      SAXIHP2AWADDR(31 downto 0) => S_AXI_HP2_AWADDR(31 downto 0),
      SAXIHP2AWBURST(1 downto 0) => S_AXI_HP2_AWBURST(1 downto 0),
      SAXIHP2AWCACHE(3 downto 0) => S_AXI_HP2_AWCACHE(3 downto 0),
      SAXIHP2AWID(5 downto 0) => S_AXI_HP2_AWID(5 downto 0),
      SAXIHP2AWLEN(3 downto 0) => S_AXI_HP2_AWLEN(3 downto 0),
      SAXIHP2AWLOCK(1 downto 0) => S_AXI_HP2_AWLOCK(1 downto 0),
      SAXIHP2AWPROT(2 downto 0) => S_AXI_HP2_AWPROT(2 downto 0),
      SAXIHP2AWQOS(3 downto 0) => S_AXI_HP2_AWQOS(3 downto 0),
      SAXIHP2AWREADY => S_AXI_HP2_AWREADY,
      SAXIHP2AWSIZE(1 downto 0) => S_AXI_HP2_AWSIZE(1 downto 0),
      SAXIHP2AWVALID => S_AXI_HP2_AWVALID,
      SAXIHP2BID(5 downto 0) => S_AXI_HP2_BID(5 downto 0),
      SAXIHP2BREADY => S_AXI_HP2_BREADY,
      SAXIHP2BRESP(1 downto 0) => S_AXI_HP2_BRESP(1 downto 0),
      SAXIHP2BVALID => S_AXI_HP2_BVALID,
      SAXIHP2RACOUNT(2 downto 0) => S_AXI_HP2_RACOUNT(2 downto 0),
      SAXIHP2RCOUNT(7 downto 0) => S_AXI_HP2_RCOUNT(7 downto 0),
      SAXIHP2RDATA(63 downto 0) => S_AXI_HP2_RDATA(63 downto 0),
      SAXIHP2RDISSUECAP1EN => S_AXI_HP2_RDISSUECAP1_EN,
      SAXIHP2RID(5 downto 0) => S_AXI_HP2_RID(5 downto 0),
      SAXIHP2RLAST => S_AXI_HP2_RLAST,
      SAXIHP2RREADY => S_AXI_HP2_RREADY,
      SAXIHP2RRESP(1 downto 0) => S_AXI_HP2_RRESP(1 downto 0),
      SAXIHP2RVALID => S_AXI_HP2_RVALID,
      SAXIHP2WACOUNT(5 downto 0) => S_AXI_HP2_WACOUNT(5 downto 0),
      SAXIHP2WCOUNT(7 downto 0) => S_AXI_HP2_WCOUNT(7 downto 0),
      SAXIHP2WDATA(63 downto 0) => S_AXI_HP2_WDATA(63 downto 0),
      SAXIHP2WID(5 downto 0) => S_AXI_HP2_WID(5 downto 0),
      SAXIHP2WLAST => S_AXI_HP2_WLAST,
      SAXIHP2WREADY => S_AXI_HP2_WREADY,
      SAXIHP2WRISSUECAP1EN => S_AXI_HP2_WRISSUECAP1_EN,
      SAXIHP2WSTRB(7 downto 0) => S_AXI_HP2_WSTRB(7 downto 0),
      SAXIHP2WVALID => S_AXI_HP2_WVALID,
      SAXIHP3ACLK => S_AXI_HP3_ACLK,
      SAXIHP3ARADDR(31 downto 0) => S_AXI_HP3_ARADDR(31 downto 0),
      SAXIHP3ARBURST(1 downto 0) => S_AXI_HP3_ARBURST(1 downto 0),
      SAXIHP3ARCACHE(3 downto 0) => S_AXI_HP3_ARCACHE(3 downto 0),
      SAXIHP3ARESETN => S_AXI_HP3_ARESETN,
      SAXIHP3ARID(5 downto 0) => S_AXI_HP3_ARID(5 downto 0),
      SAXIHP3ARLEN(3 downto 0) => S_AXI_HP3_ARLEN(3 downto 0),
      SAXIHP3ARLOCK(1 downto 0) => S_AXI_HP3_ARLOCK(1 downto 0),
      SAXIHP3ARPROT(2 downto 0) => S_AXI_HP3_ARPROT(2 downto 0),
      SAXIHP3ARQOS(3 downto 0) => S_AXI_HP3_ARQOS(3 downto 0),
      SAXIHP3ARREADY => S_AXI_HP3_ARREADY,
      SAXIHP3ARSIZE(1 downto 0) => S_AXI_HP3_ARSIZE(1 downto 0),
      SAXIHP3ARVALID => S_AXI_HP3_ARVALID,
      SAXIHP3AWADDR(31 downto 0) => S_AXI_HP3_AWADDR(31 downto 0),
      SAXIHP3AWBURST(1 downto 0) => S_AXI_HP3_AWBURST(1 downto 0),
      SAXIHP3AWCACHE(3 downto 0) => S_AXI_HP3_AWCACHE(3 downto 0),
      SAXIHP3AWID(5 downto 0) => S_AXI_HP3_AWID(5 downto 0),
      SAXIHP3AWLEN(3 downto 0) => S_AXI_HP3_AWLEN(3 downto 0),
      SAXIHP3AWLOCK(1 downto 0) => S_AXI_HP3_AWLOCK(1 downto 0),
      SAXIHP3AWPROT(2 downto 0) => S_AXI_HP3_AWPROT(2 downto 0),
      SAXIHP3AWQOS(3 downto 0) => S_AXI_HP3_AWQOS(3 downto 0),
      SAXIHP3AWREADY => S_AXI_HP3_AWREADY,
      SAXIHP3AWSIZE(1 downto 0) => S_AXI_HP3_AWSIZE(1 downto 0),
      SAXIHP3AWVALID => S_AXI_HP3_AWVALID,
      SAXIHP3BID(5 downto 0) => S_AXI_HP3_BID(5 downto 0),
      SAXIHP3BREADY => S_AXI_HP3_BREADY,
      SAXIHP3BRESP(1 downto 0) => S_AXI_HP3_BRESP(1 downto 0),
      SAXIHP3BVALID => S_AXI_HP3_BVALID,
      SAXIHP3RACOUNT(2 downto 0) => S_AXI_HP3_RACOUNT(2 downto 0),
      SAXIHP3RCOUNT(7 downto 0) => S_AXI_HP3_RCOUNT(7 downto 0),
      SAXIHP3RDATA(63 downto 0) => S_AXI_HP3_RDATA(63 downto 0),
      SAXIHP3RDISSUECAP1EN => S_AXI_HP3_RDISSUECAP1_EN,
      SAXIHP3RID(5 downto 0) => S_AXI_HP3_RID(5 downto 0),
      SAXIHP3RLAST => S_AXI_HP3_RLAST,
      SAXIHP3RREADY => S_AXI_HP3_RREADY,
      SAXIHP3RRESP(1 downto 0) => S_AXI_HP3_RRESP(1 downto 0),
      SAXIHP3RVALID => S_AXI_HP3_RVALID,
      SAXIHP3WACOUNT(5 downto 0) => S_AXI_HP3_WACOUNT(5 downto 0),
      SAXIHP3WCOUNT(7 downto 0) => S_AXI_HP3_WCOUNT(7 downto 0),
      SAXIHP3WDATA(63 downto 0) => S_AXI_HP3_WDATA(63 downto 0),
      SAXIHP3WID(5 downto 0) => S_AXI_HP3_WID(5 downto 0),
      SAXIHP3WLAST => S_AXI_HP3_WLAST,
      SAXIHP3WREADY => S_AXI_HP3_WREADY,
      SAXIHP3WRISSUECAP1EN => S_AXI_HP3_WRISSUECAP1_EN,
      SAXIHP3WSTRB(7 downto 0) => S_AXI_HP3_WSTRB(7 downto 0),
      SAXIHP3WVALID => S_AXI_HP3_WVALID
    );
PS_CLK_BIBUF: unisim.vcomponents.BIBUF
     port map (
      IO => buffered_PS_CLK,
      PAD => PS_CLK
    );
PS_PORB_BIBUF: unisim.vcomponents.BIBUF
     port map (
      IO => buffered_PS_PORB,
      PAD => PS_PORB
    );
PS_SRSTB_BIBUF: unisim.vcomponents.BIBUF
     port map (
      IO => buffered_PS_SRSTB,
      PAD => PS_SRSTB
    );
SDIO0_CMD_T_INST_0: unisim.vcomponents.LUT1
    generic map(
      INIT => X"1"
    )
        port map (
      I0 => SDIO0_CMD_T_n,
      O => SDIO0_CMD_T
    );
\SDIO0_DATA_T[0]_INST_0\: unisim.vcomponents.LUT1
    generic map(
      INIT => X"1"
    )
        port map (
      I0 => SDIO0_DATA_T_n(0),
      O => SDIO0_DATA_T(0)
    );
\SDIO0_DATA_T[1]_INST_0\: unisim.vcomponents.LUT1
    generic map(
      INIT => X"1"
    )
        port map (
      I0 => SDIO0_DATA_T_n(1),
      O => SDIO0_DATA_T(1)
    );
\SDIO0_DATA_T[2]_INST_0\: unisim.vcomponents.LUT1
    generic map(
      INIT => X"1"
    )
        port map (
      I0 => SDIO0_DATA_T_n(2),
      O => SDIO0_DATA_T(2)
    );
\SDIO0_DATA_T[3]_INST_0\: unisim.vcomponents.LUT1
    generic map(
      INIT => X"1"
    )
        port map (
      I0 => SDIO0_DATA_T_n(3),
      O => SDIO0_DATA_T(3)
    );
SDIO1_CMD_T_INST_0: unisim.vcomponents.LUT1
    generic map(
      INIT => X"1"
    )
        port map (
      I0 => SDIO1_CMD_T_n,
      O => SDIO1_CMD_T
    );
\SDIO1_DATA_T[0]_INST_0\: unisim.vcomponents.LUT1
    generic map(
      INIT => X"1"
    )
        port map (
      I0 => SDIO1_DATA_T_n(0),
      O => SDIO1_DATA_T(0)
    );
\SDIO1_DATA_T[1]_INST_0\: unisim.vcomponents.LUT1
    generic map(
      INIT => X"1"
    )
        port map (
      I0 => SDIO1_DATA_T_n(1),
      O => SDIO1_DATA_T(1)
    );
\SDIO1_DATA_T[2]_INST_0\: unisim.vcomponents.LUT1
    generic map(
      INIT => X"1"
    )
        port map (
      I0 => SDIO1_DATA_T_n(2),
      O => SDIO1_DATA_T(2)
    );
\SDIO1_DATA_T[3]_INST_0\: unisim.vcomponents.LUT1
    generic map(
      INIT => X"1"
    )
        port map (
      I0 => SDIO1_DATA_T_n(3),
      O => SDIO1_DATA_T(3)
    );
SPI0_MISO_T_INST_0: unisim.vcomponents.LUT1
    generic map(
      INIT => X"1"
    )
        port map (
      I0 => SPI0_MISO_T_n,
      O => SPI0_MISO_T
    );
SPI0_MOSI_T_INST_0: unisim.vcomponents.LUT1
    generic map(
      INIT => X"1"
    )
        port map (
      I0 => SPI0_MOSI_T_n,
      O => SPI0_MOSI_T
    );
SPI0_SCLK_T_INST_0: unisim.vcomponents.LUT1
    generic map(
      INIT => X"1"
    )
        port map (
      I0 => SPI0_SCLK_T_n,
      O => SPI0_SCLK_T
    );
SPI0_SS_T_INST_0: unisim.vcomponents.LUT1
    generic map(
      INIT => X"1"
    )
        port map (
      I0 => SPI0_SS_T_n,
      O => SPI0_SS_T
    );
SPI1_MISO_T_INST_0: unisim.vcomponents.LUT1
    generic map(
      INIT => X"1"
    )
        port map (
      I0 => SPI1_MISO_T_n,
      O => SPI1_MISO_T
    );
SPI1_MOSI_T_INST_0: unisim.vcomponents.LUT1
    generic map(
      INIT => X"1"
    )
        port map (
      I0 => SPI1_MOSI_T_n,
      O => SPI1_MOSI_T
    );
SPI1_SCLK_T_INST_0: unisim.vcomponents.LUT1
    generic map(
      INIT => X"1"
    )
        port map (
      I0 => SPI1_SCLK_T_n,
      O => SPI1_SCLK_T
    );
SPI1_SS_T_INST_0: unisim.vcomponents.LUT1
    generic map(
      INIT => X"1"
    )
        port map (
      I0 => SPI1_SS_T_n,
      O => SPI1_SS_T
    );
VCC: unisim.vcomponents.VCC
     port map (
      P => \<const1>\
    );
\buffer_fclk_clk_0.FCLK_CLK_0_BUFG\: unisim.vcomponents.BUFG
     port map (
      I => FCLK_CLK_unbuffered(0),
      O => FCLK_CLK0
    );
\genblk13[0].MIO_BIBUF\: unisim.vcomponents.BIBUF
     port map (
      IO => buffered_MIO(0),
      PAD => MIO(0)
    );
\genblk13[10].MIO_BIBUF\: unisim.vcomponents.BIBUF
     port map (
      IO => buffered_MIO(10),
      PAD => MIO(10)
    );
\genblk13[11].MIO_BIBUF\: unisim.vcomponents.BIBUF
     port map (
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
     port map (
      IO => buffered_DDR_Addr(11),
      PAD => DDR_Addr(11)
    );
\genblk15[12].DDR_Addr_BIBUF\: unisim.vcomponents.BIBUF
     port map (
      IO => buffered_DDR_Addr(12),
      PAD => DDR_Addr(12)
    );
\genblk15[13].DDR_Addr_BIBUF\: unisim.vcomponents.BIBUF
     port map (
      IO => buffered_DDR_Addr(13),
      PAD => DDR_Addr(13)
    );
\genblk15[14].DDR_Addr_BIBUF\: unisim.vcomponents.BIBUF
     port map (
      IO => buffered_DDR_Addr(14),
      PAD => DDR_Addr(14)
    );
\genblk15[1].DDR_Addr_BIBUF\: unisim.vcomponents.BIBUF
     port map (
      IO => buffered_DDR_Addr(1),
      PAD => DDR_Addr(1)
    );
\genblk15[2].DDR_Addr_BIBUF\: unisim.vcomponents.BIBUF
     port map (
      IO => buffered_DDR_Addr(2),
      PAD => DDR_Addr(2)
    );
\genblk15[3].DDR_Addr_BIBUF\: unisim.vcomponents.BIBUF
     port map (
      IO => buffered_DDR_Addr(3),
      PAD => DDR_Addr(3)
    );
\genblk15[4].DDR_Addr_BIBUF\: unisim.vcomponents.BIBUF
     port map (
      IO => buffered_DDR_Addr(4),
      PAD => DDR_Addr(4)
    );
\genblk15[5].DDR_Addr_BIBUF\: unisim.vcomponents.BIBUF
     port map (
      IO => buffered_DDR_Addr(5),
      PAD => DDR_Addr(5)
    );
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
