dave18/EBAZ4205-Daughter-Board/Test_Code/EBAZ4205_Test5.srcs/sources_1/bd/System/ip/System_processing_system7_0_0/sim/System_processing_system7_0_0.sv

`timescale 1ns/1ps

//PORTS

      bit  CAN0_PHY_TX;
      bit  CAN0_PHY_RX;
      bit  CAN1_PHY_TX;
      bit  CAN1_PHY_RX;
      bit  [0 : 0] ENET0_GMII_TX_EN;
      bit  [0 : 0] ENET0_GMII_TX_ER;
      bit  ENET0_MDIO_MDC;
      bit  ENET0_MDIO_O;
      bit  ENET0_MDIO_T;
      bit  ENET0_PTP_DELAY_REQ_RX;
      bit  ENET0_PTP_DELAY_REQ_TX;
      bit  ENET0_PTP_PDELAY_REQ_RX;
      bit  ENET0_PTP_PDELAY_REQ_TX;
      bit  ENET0_PTP_PDELAY_RESP_RX;
      bit  ENET0_PTP_PDELAY_RESP_TX;
      bit  ENET0_PTP_SYNC_FRAME_RX;
      bit  ENET0_PTP_SYNC_FRAME_TX;
      bit  ENET0_SOF_RX;
      bit  ENET0_SOF_TX;
      bit  [7 : 0] ENET0_GMII_TXD;
      bit  ENET0_GMII_COL;
      bit  ENET0_GMII_CRS;
      bit  ENET0_GMII_RX_CLK;
      bit  ENET0_GMII_RX_DV;
      bit  ENET0_GMII_RX_ER;
      bit  ENET0_GMII_TX_CLK;
      bit  ENET0_MDIO_I;
      bit  ENET0_EXT_INTIN;
      bit  [7 : 0] ENET0_GMII_RXD;
      bit  [0 : 0] ENET1_GMII_TX_EN;
      bit  [0 : 0] ENET1_GMII_TX_ER;
      bit  ENET1_MDIO_MDC;
      bit  ENET1_MDIO_O;
      bit  ENET1_MDIO_T;
      bit  ENET1_PTP_DELAY_REQ_RX;
      bit  ENET1_PTP_DELAY_REQ_TX;
      bit  ENET1_PTP_PDELAY_REQ_RX;
      bit  ENET1_PTP_PDELAY_REQ_TX;
      bit  ENET1_PTP_PDELAY_RESP_RX;
      bit  ENET1_PTP_PDELAY_RESP_TX;
      bit  ENET1_PTP_SYNC_FRAME_RX;
      bit  ENET1_PTP_SYNC_FRAME_TX;
      bit  ENET1_SOF_RX;
      bit  ENET1_SOF_TX;
      bit  [7 : 0] ENET1_GMII_TXD;
      bit  ENET1_GMII_COL;
      bit  ENET1_GMII_CRS;
      bit  ENET1_GMII_RX_CLK;
      bit  ENET1_GMII_RX_DV;
      bit  ENET1_GMII_RX_ER;
      bit  ENET1_GMII_TX_CLK;
      bit  ENET1_MDIO_I;
      bit  ENET1_EXT_INTIN;
      bit  [7 : 0] ENET1_GMII_RXD;
      bit  [63 : 0] GPIO_I;
      bit  [63 : 0] GPIO_O;
      bit  [63 : 0] GPIO_T;
      bit  I2C0_SDA_I;
      bit  I2C0_SDA_O;
      bit  I2C0_SDA_T;
      bit  I2C0_SCL_I;
      bit  I2C0_SCL_O;
      bit  I2C0_SCL_T;
      bit  I2C1_SDA_I;
      bit  I2C1_SDA_O;
      bit  I2C1_SDA_T;
      bit  I2C1_SCL_I;
      bit  I2C1_SCL_O;
      bit  I2C1_SCL_T;
      bit  PJTAG_TCK;
      bit  PJTAG_TMS;
      bit  PJTAG_TDI;
      bit  PJTAG_TDO;
      bit  SDIO0_CLK;
      bit  SDIO0_CLK_FB;
      bit  SDIO0_CMD_O;
      bit  SDIO0_CMD_I;
      bit  SDIO0_CMD_T;
      bit  [3 : 0] SDIO0_DATA_I;
      bit  [3 : 0] SDIO0_DATA_O;
      bit  [3 : 0] SDIO0_DATA_T;
      bit  SDIO0_LED;
      bit  SDIO0_CDN;
      bit  SDIO0_WP;
      bit  SDIO0_BUSPOW;
      bit  [2 : 0] SDIO0_BUSVOLT;
      bit  SDIO1_CLK;
      bit  SDIO1_CLK_FB;
      bit  SDIO1_CMD_O;
      bit  SDIO1_CMD_I;
      bit  SDIO1_CMD_T;
      bit  [3 : 0] SDIO1_DATA_I;
      bit  [3 : 0] SDIO1_DATA_O;
      bit  [3 : 0] SDIO1_DATA_T;
      bit  SDIO1_LED;
      bit  SDIO1_CDN;
      bit  SDIO1_WP;
      bit  SDIO1_BUSPOW;
      bit  [2 : 0] SDIO1_BUSVOLT;
      bit  SPI0_SCLK_I;
      bit  SPI0_SCLK_O;
      bit  SPI0_SCLK_T;
      bit  SPI0_MOSI_I;
      bit  SPI0_MOSI_O;
      bit  SPI0_MOSI_T;
      bit  SPI0_MISO_I;
      bit  SPI0_MISO_O;
      bit  SPI0_MISO_T;
      bit  SPI0_SS_I;
      bit  SPI0_SS_O;
      bit  SPI0_SS1_O;
      bit  SPI0_SS2_O;
      bit  SPI0_SS_T;
      bit  SPI1_SCLK_I;
      bit  SPI1_SCLK_O;
      bit  SPI1_SCLK_T;
      bit  SPI1_MOSI_I;
      bit  SPI1_MOSI_O;
      bit  SPI1_MOSI_T;
      bit  SPI1_MISO_I;
      bit  SPI1_MISO_O;
      bit  SPI1_MISO_T;
      bit  SPI1_SS_I;
      bit  SPI1_SS_O;
      bit  SPI1_SS1_O;
      bit  SPI1_SS2_O;
      bit  SPI1_SS_T;
      bit  UART0_DTRN;
      bit  UART0_RTSN;
      bit  UART0_TX;
      bit  UART0_CTSN;
      bit  UART0_DCDN;
      bit  UART0_DSRN;
      bit  UART0_RIN;
      bit  UART0_RX;
      bit  UART1_DTRN;
      bit  UART1_RTSN;
      bit  UART1_TX;
      bit  UART1_CTSN;
      bit  UART1_DCDN;
      bit  UART1_DSRN;
      bit  UART1_RIN;
      bit  UART1_RX;
      bit  TTC0_WAVE0_OUT;
      bit  TTC0_WAVE1_OUT;
      bit  TTC0_WAVE2_OUT;
      bit  TTC0_CLK0_IN;
      bit  TTC0_CLK1_IN;
      bit  TTC0_CLK2_IN;
      bit  TTC1_WAVE0_OUT;
      bit  TTC1_WAVE1_OUT;
      bit  TTC1_WAVE2_OUT;
      bit  TTC1_CLK0_IN;
      bit  TTC1_CLK1_IN;
      bit  TTC1_CLK2_IN;
      bit  WDT_CLK_IN;
      bit  WDT_RST_OUT;
      bit  TRACE_CLK;
      bit  TRACE_CLK_OUT;
      bit  TRACE_CTL;
      bit  [1 : 0] TRACE_DATA;
      bit  [1 : 0] USB0_PORT_INDCTL;
      bit  USB0_VBUS_PWRSELECT;
      bit  USB0_VBUS_PWRFAULT;
      bit  [1 : 0] USB1_PORT_INDCTL;
      bit  USB1_VBUS_PWRSELECT;
      bit  USB1_VBUS_PWRFAULT;
      bit  SRAM_INTIN;
      bit  M_AXI_GP0_ARVALID;
      bit  M_AXI_GP0_AWVALID;
      bit  M_AXI_GP0_BREADY;
      bit  M_AXI_GP0_RREADY;
      bit  M_AXI_GP0_WLAST;
      bit  M_AXI_GP0_WVALID;
      bit  [11 : 0] M_AXI_GP0_ARID;
      bit  [11 : 0] M_AXI_GP0_AWID;
      bit  [11 : 0] M_AXI_GP0_WID;
      bit  [1 : 0] M_AXI_GP0_ARBURST;
      bit  [1 : 0] M_AXI_GP0_ARLOCK;
      bit  [2 : 0] M_AXI_GP0_ARSIZE;
      bit  [1 : 0] M_AXI_GP0_AWBURST;
      bit  [1 : 0] M_AXI_GP0_AWLOCK;
      bit  [2 : 0] M_AXI_GP0_AWSIZE;
      bit  [2 : 0] M_AXI_GP0_ARPROT;
      bit  [2 : 0] M_AXI_GP0_AWPROT;
      bit  [31 : 0] M_AXI_GP0_ARADDR;
      bit  [31 : 0] M_AXI_GP0_AWADDR;
      bit  [31 : 0] M_AXI_GP0_WDATA;
      bit  [3 : 0] M_AXI_GP0_ARCACHE;
      bit  [3 : 0] M_AXI_GP0_ARLEN;
      bit  [3 : 0] M_AXI_GP0_ARQOS;
      bit  [3 : 0] M_AXI_GP0_AWCACHE;
      bit  [3 : 0] M_AXI_GP0_AWLEN;
      bit  [3 : 0] M_AXI_GP0_AWQOS;
      bit  [3 : 0] M_AXI_GP0_WSTRB;
      bit  M_AXI_GP0_ACLK;
      bit  M_AXI_GP0_ARREADY;
      bit  M_AXI_GP0_AWREADY;
      bit  M_AXI_GP0_BVALID;
      bit  M_AXI_GP0_RLAST;
      bit  M_AXI_GP0_RVALID;
      bit  M_AXI_GP0_WREADY;
      bit  [11 : 0] M_AXI_GP0_BID;
      bit  [11 : 0] M_AXI_GP0_RID;
      bit  [1 : 0] M_AXI_GP0_BRESP;
      bit  [1 : 0] M_AXI_GP0_RRESP;
      bit  [31 : 0] M_AXI_GP0_RDATA;
      bit  M_AXI_GP1_ARVALID;
      bit  M_AXI_GP1_AWVALID;
      bit  M_AXI_GP1_BREADY;
      bit  M_AXI_GP1_RREADY;
      bit  M_AXI_GP1_WLAST;
      bit  M_AXI_GP1_WVALID;
      bit  [11 : 0] M_AXI_GP1_ARID;
      bit  [11 : 0] M_AXI_GP1_AWID;
      bit  [11 : 0] M_AXI_GP1_WID;
      bit  [1 : 0] M_AXI_GP1_ARBURST;
      bit  [1 : 0] M_AXI_GP1_ARLOCK;
      bit  [2 : 0] M_AXI_GP1_ARSIZE;
      bit  [1 : 0] M_AXI_GP1_AWBURST;
      bit  [1 : 0] M_AXI_GP1_AWLOCK;
      bit  [2 : 0] M_AXI_GP1_AWSIZE;
      bit  [2 : 0] M_AXI_GP1_ARPROT;
      bit  [2 : 0] M_AXI_GP1_AWPROT;
      bit  [31 : 0] M_AXI_GP1_ARADDR;
      bit  [31 : 0] M_AXI_GP1_AWADDR;
      bit  [31 : 0] M_AXI_GP1_WDATA;
      bit  [3 : 0] M_AXI_GP1_ARCACHE;
      bit  [3 : 0] M_AXI_GP1_ARLEN;
      bit  [3 : 0] M_AXI_GP1_ARQOS;
      bit  [3 : 0] M_AXI_GP1_AWCACHE;
      bit  [3 : 0] M_AXI_GP1_AWLEN;
      bit  [3 : 0] M_AXI_GP1_AWQOS;
      bit  [3 : 0] M_AXI_GP1_WSTRB;
      bit  M_AXI_GP1_ACLK;
      bit  M_AXI_GP1_ARREADY;
      bit  M_AXI_GP1_AWREADY;
      bit  M_AXI_GP1_BVALID;
      bit  M_AXI_GP1_RLAST;
      bit  M_AXI_GP1_RVALID;
      bit  M_AXI_GP1_WREADY;
      bit  [11 : 0] M_AXI_GP1_BID;
      bit  [11 : 0] M_AXI_GP1_RID;
      bit  [1 : 0] M_AXI_GP1_BRESP;
      bit  [1 : 0] M_AXI_GP1_RRESP;
      bit  [31 : 0] M_AXI_GP1_RDATA;
      bit  S_AXI_GP0_ARREADY;
      bit  S_AXI_GP0_AWREADY;
      bit  S_AXI_GP0_BVALID;
      bit  S_AXI_GP0_RLAST;
      bit  S_AXI_GP0_RVALID;
      bit  S_AXI_GP0_WREADY;
      bit  [1 : 0] S_AXI_GP0_BRESP;
      bit  [1 : 0] S_AXI_GP0_RRESP;
      bit  [31 : 0] S_AXI_GP0_RDATA;
      bit  [5 : 0] S_AXI_GP0_BID;
      bit  [5 : 0] S_AXI_GP0_RID;
      bit  S_AXI_GP0_ACLK;
      bit  S_AXI_GP0_ARVALID;
      bit  S_AXI_GP0_AWVALID;
      bit  S_AXI_GP0_BREADY;
      bit  S_AXI_GP0_RREADY;
      bit  S_AXI_GP0_WLAST;
      bit  S_AXI_GP0_WVALID;
      bit  [1 : 0] S_AXI_GP0_ARBURST;
      bit  [1 : 0] S_AXI_GP0_ARLOCK;
      bit  [2 : 0] S_AXI_GP0_ARSIZE;
      bit  [1 : 0] S_AXI_GP0_AWBURST;
      bit  [1 : 0] S_AXI_GP0_AWLOCK;
      bit  [2 : 0] S_AXI_GP0_AWSIZE;
      bit  [2 : 0] S_AXI_GP0_ARPROT;
      bit  [2 : 0] S_AXI_GP0_AWPROT;
      bit  [31 : 0] S_AXI_GP0_ARADDR;
      bit  [31 : 0] S_AXI_GP0_AWADDR;
      bit  [31 : 0] S_AXI_GP0_WDATA;
      bit  [3 : 0] S_AXI_GP0_ARCACHE;
      bit  [3 : 0] S_AXI_GP0_ARLEN;
      bit  [3 : 0] S_AXI_GP0_ARQOS;
      bit  [3 : 0] S_AXI_GP0_AWCACHE;
      bit  [3 : 0] S_AXI_GP0_AWLEN;
      bit  [3 : 0] S_AXI_GP0_AWQOS;
      bit  [3 : 0] S_AXI_GP0_WSTRB;
      bit  [5 : 0] S_AXI_GP0_ARID;
      bit  [5 : 0] S_AXI_GP0_AWID;
      bit  [5 : 0] S_AXI_GP0_WID;
      bit  S_AXI_GP1_ARREADY;
      bit  S_AXI_GP1_AWREADY;
      bit  S_AXI_GP1_BVALID;
      bit  S_AXI_GP1_RLAST;
      bit  S_AXI_GP1_RVALID;
      bit  S_AXI_GP1_WREADY;
      bit  [1 : 0] S_AXI_GP1_BRESP;
      bit  [1 : 0] S_AXI_GP1_RRESP;
      bit  [31 : 0] S_AXI_GP1_RDATA;
      bit  [5 : 0] S_AXI_GP1_BID;
      bit  [5 : 0] S_AXI_GP1_RID;
      bit  S_AXI_GP1_ACLK;
      bit  S_AXI_GP1_ARVALID;
      bit  S_AXI_GP1_AWVALID;
      bit  S_AXI_GP1_BREADY;
      bit  S_AXI_GP1_RREADY;
      bit  S_AXI_GP1_WLAST;
      bit  S_AXI_GP1_WVALID;
      bit  [1 : 0] S_AXI_GP1_ARBURST;
      bit  [1 : 0] S_AXI_GP1_ARLOCK;
      bit  [2 : 0] S_AXI_GP1_ARSIZE;
      bit  [1 : 0] S_AXI_GP1_AWBURST;
      bit  [1 : 0] S_AXI_GP1_AWLOCK;
      bit  [2 : 0] S_AXI_GP1_AWSIZE;
      bit  [2 : 0] S_AXI_GP1_ARPROT;
      bit  [2 : 0] S_AXI_GP1_AWPROT;
      bit  [31 : 0] S_AXI_GP1_ARADDR;
      bit  [31 : 0] S_AXI_GP1_AWADDR;
      bit  [31 : 0] S_AXI_GP1_WDATA;
      bit  [3 : 0] S_AXI_GP1_ARCACHE;
      bit  [3 : 0] S_AXI_GP1_ARLEN;
      bit  [3 : 0] S_AXI_GP1_ARQOS;
      bit  [3 : 0] S_AXI_GP1_AWCACHE;
      bit  [3 : 0] S_AXI_GP1_AWLEN;
      bit  [3 : 0] S_AXI_GP1_AWQOS;
      bit  [3 : 0] S_AXI_GP1_WSTRB;
      bit  [5 : 0] S_AXI_GP1_ARID;
      bit  [5 : 0] S_AXI_GP1_AWID;
      bit  [5 : 0] S_AXI_GP1_WID;
      bit  S_AXI_ACP_ARREADY;
      bit  S_AXI_ACP_AWREADY;
      bit  S_AXI_ACP_BVALID;
      bit  S_AXI_ACP_RLAST;
      bit  S_AXI_ACP_RVALID;
      bit  S_AXI_ACP_WREADY;
      bit  [1 : 0] S_AXI_ACP_BRESP;
      bit  [1 : 0] S_AXI_ACP_RRESP;
      bit  [2 : 0] S_AXI_ACP_BID;
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
